kholia/HF-PA-v10/R4-Minimal-K1TE/README.md

Minor tweaks - previous versions are 100% fine ;)

List of changes:

- Base resistor changed to 3.3R

- Use M3 holes ;)

- Longer pads for the SMD-coupled-inductor

- Use SMT caps in LPF
