kholia/HF-PA-v10/R7.1/README.md

Minor tweaks - previous versions are 100% fine ;)

List of changes:

- Various silkscreen improvements
