kholia/HF-PA-v10/GSD-Hacks-v2-SMD/README.md

This version uses SOP-8 gate driver (UCC27614DR) and GSD pinout FET.
