kholia/HF-PA-v10/GSD-Hacks-v3-SMD/README.md

This version uses SOIC-8 gate driver (NCP81074ADR2G) and GSD pinout FET.
