kholia/HF-PA-v10/IRFP-Hacks-v5-SMD/README.md

This works great - tested in June 2024.

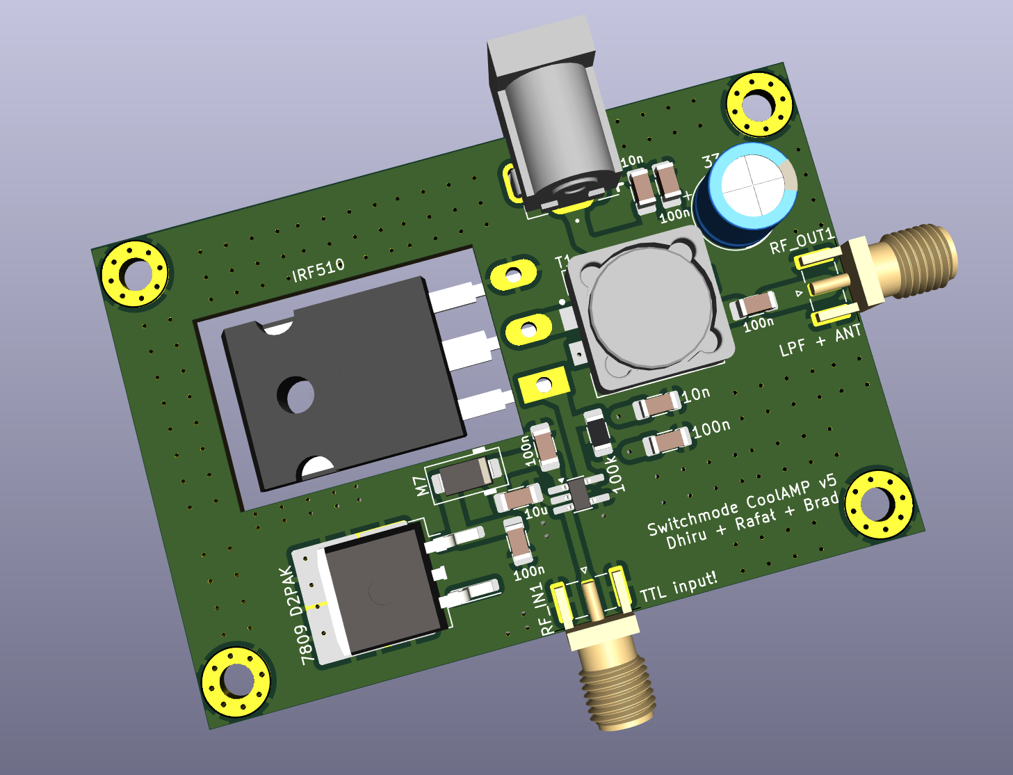
[picture p13: IRFP-Hacks-v5-SMD/Screenshot_2024-08-01_07-13-50.png]
3D render
