kholia/HF-PA-v10/3-Pole-LPF/Screenshot_2024-05-31_14-55-14.png

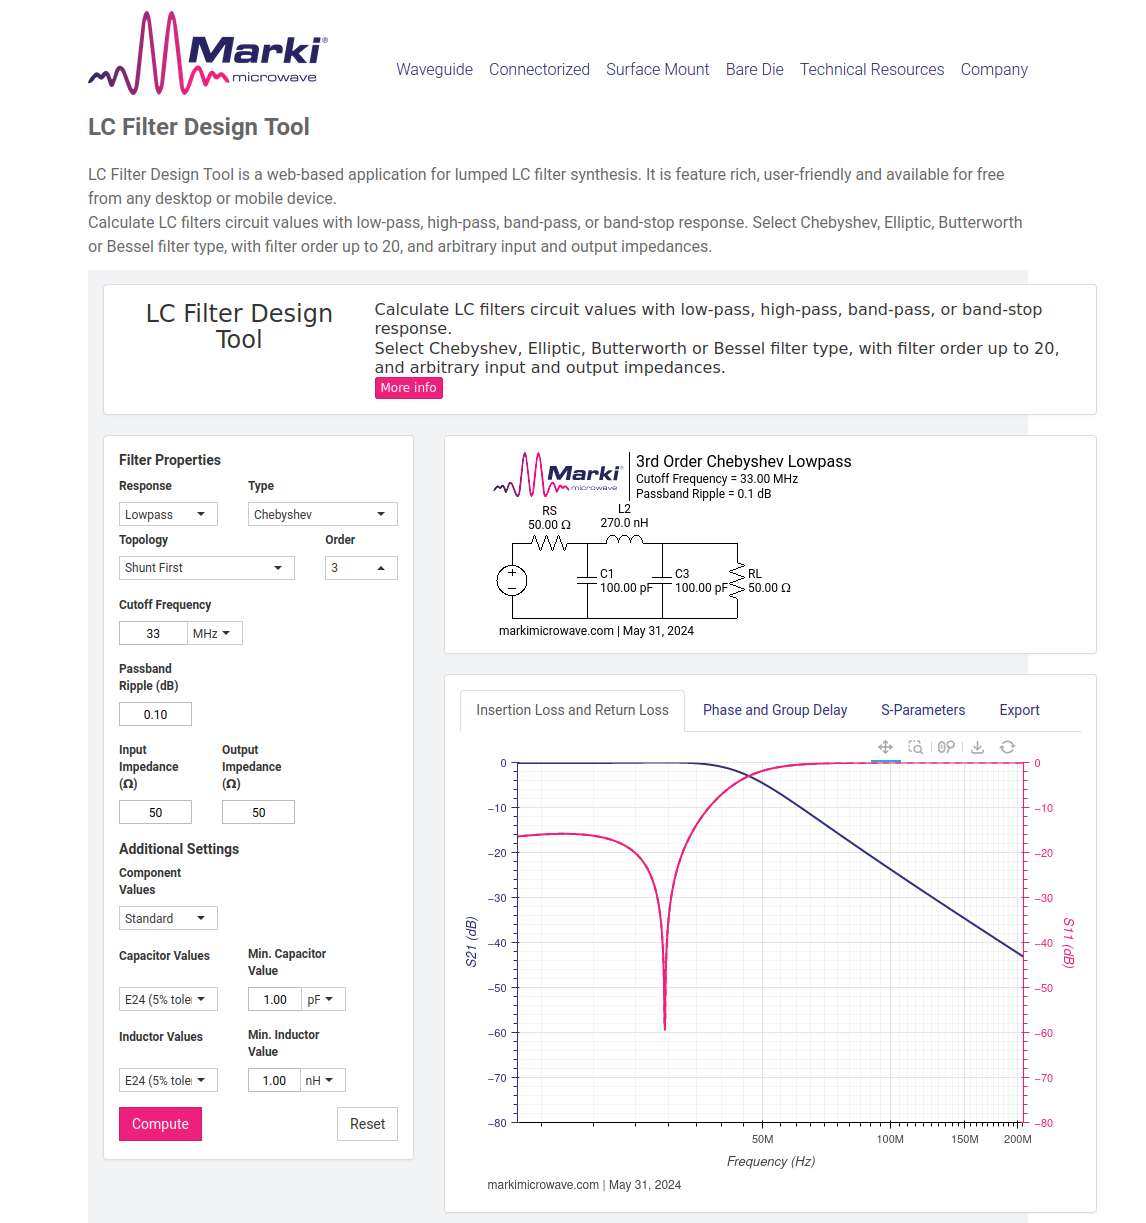
3-Pole-LPF/Screenshot_2024-05-31_14-55-14.png
