kholia/HF-PA-v10/5-Pole-LPF/Screenshot_2024-06-10_09-03-32.png

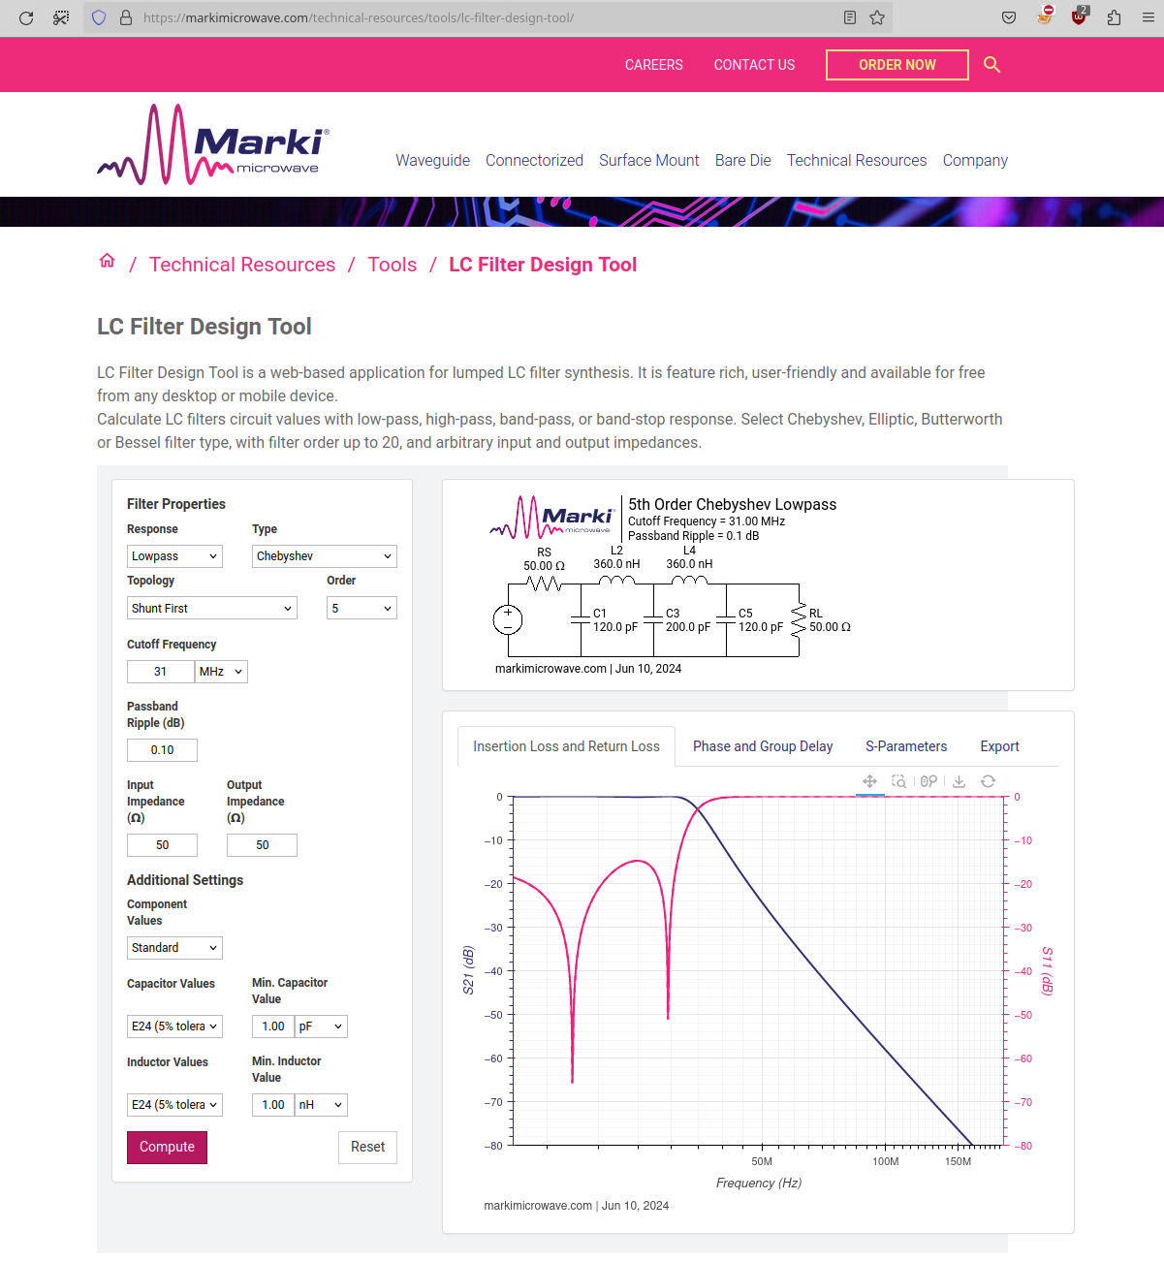
5-Pole-LPF/Screenshot_2024-06-10_09-03-32.png
