kholia/HF-PA-v10/Digital-PA-v3/Screenshot_2023-10-04_21-27-38.png

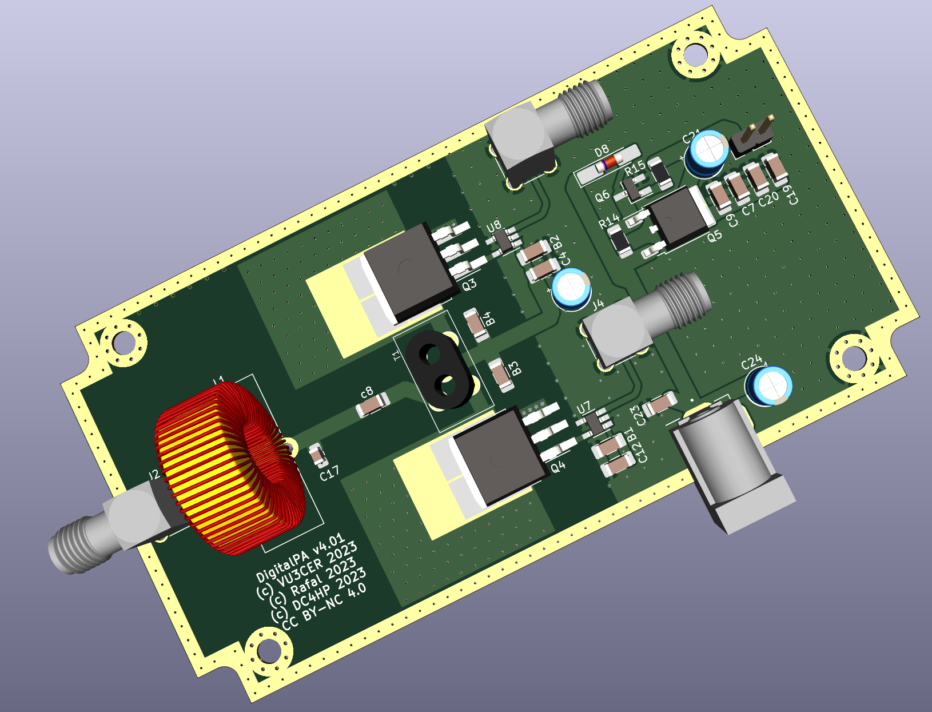
Digital-PA-v3/Screenshot_2023-10-04_21-27-38.png
