kholia/HF-PA-v10/FuturePowerControl/Alinco DX-10 - Retro Feel.png

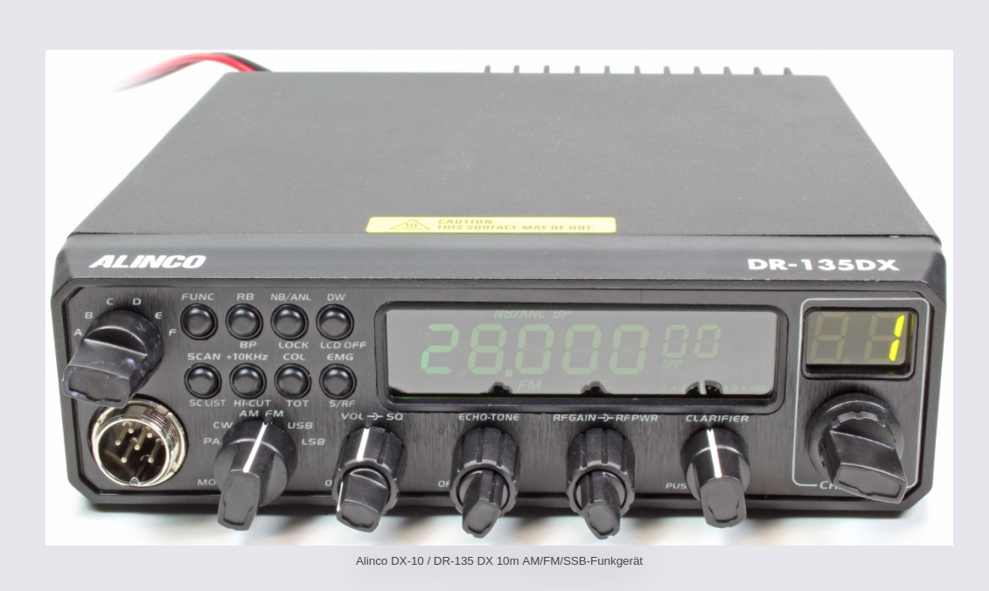
FuturePowerControl/Alinco DX-10 - Retro Feel.png
