kholia/HF-PA-v10/Heat-Sinking/heatsinkmtg.gif

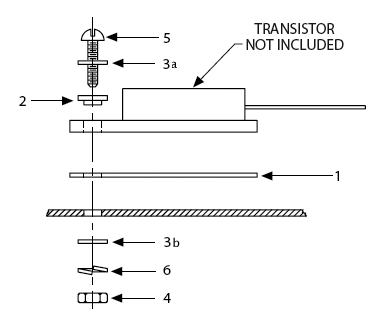
Heat-Sinking/heatsinkmtg.gif
