kholia/HF-PA-v10/Heat-Sinking/heatsinkmtgparts.gif

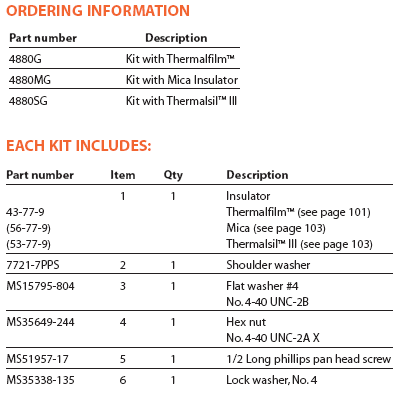
Heat-Sinking/heatsinkmtgparts.gif
