kholia/HF-PA-v10/info/25wlinear-small.png

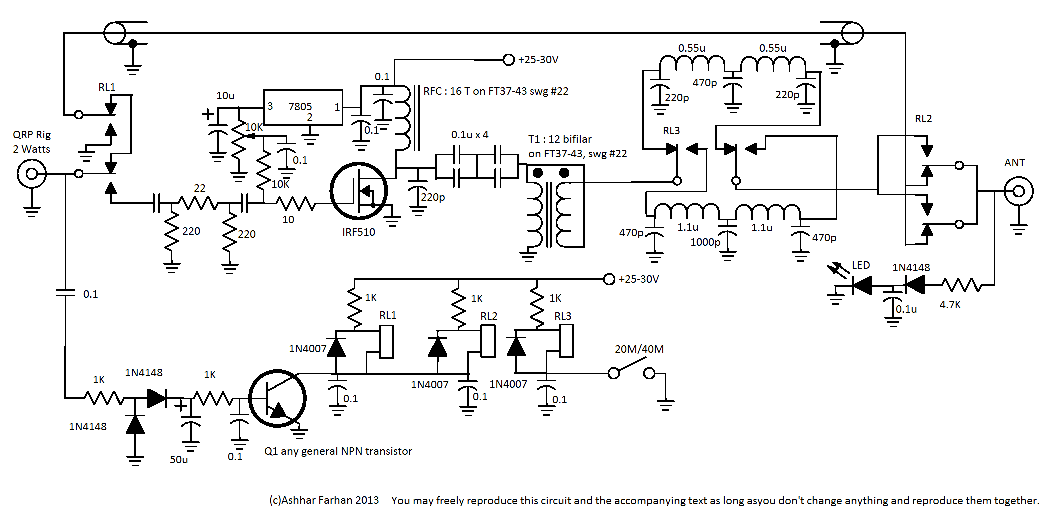
info/25wlinear-small.png
