kholia/HF-PA-v10/info/Henning Paul's PA prototype.jpeg

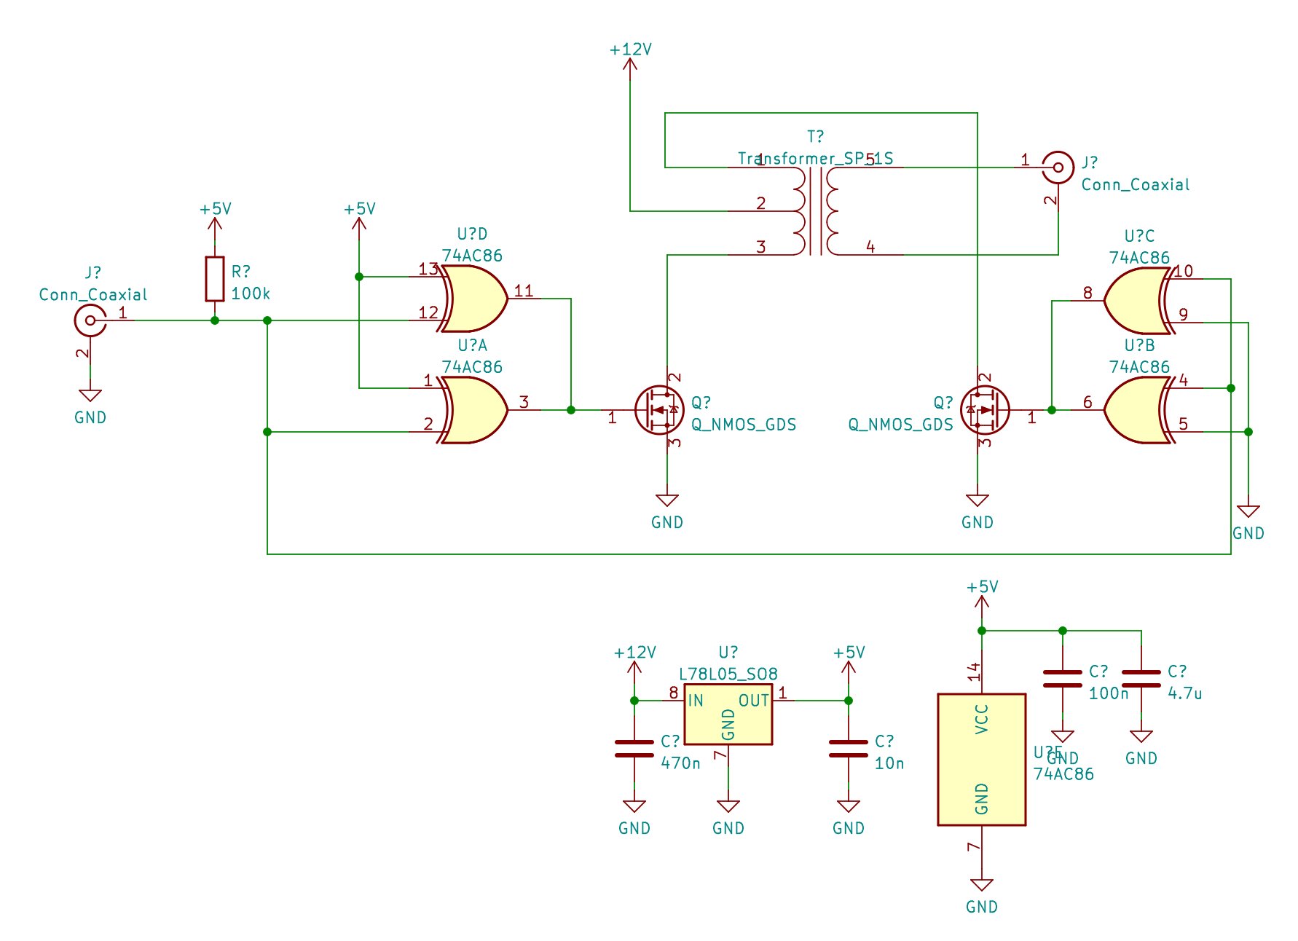
info/Henning Paul's PA prototype.jpeg
