kholia/HF-PA-v10/info/Henning Paul's PA v2.0.jpeg

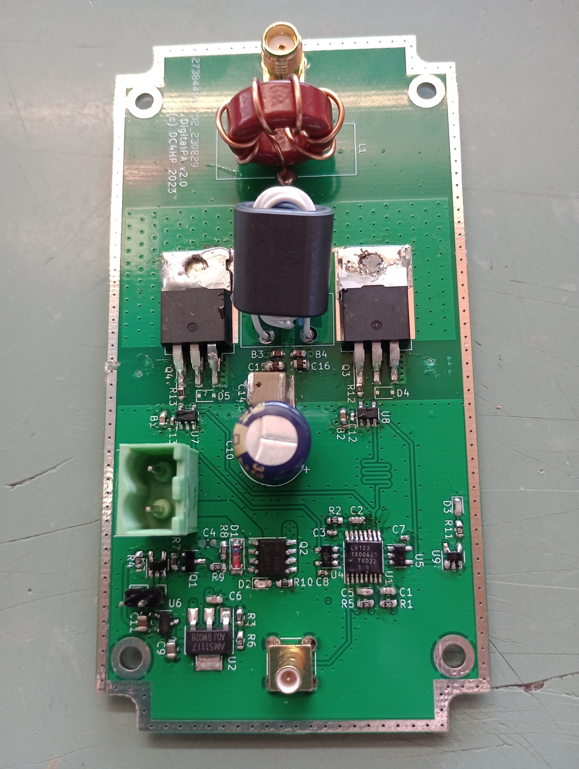
info/Henning Paul's PA v2.0.jpeg
