kholia/HF-PA-v10/info/Screenshot_2023-08-16_22-52-23.png

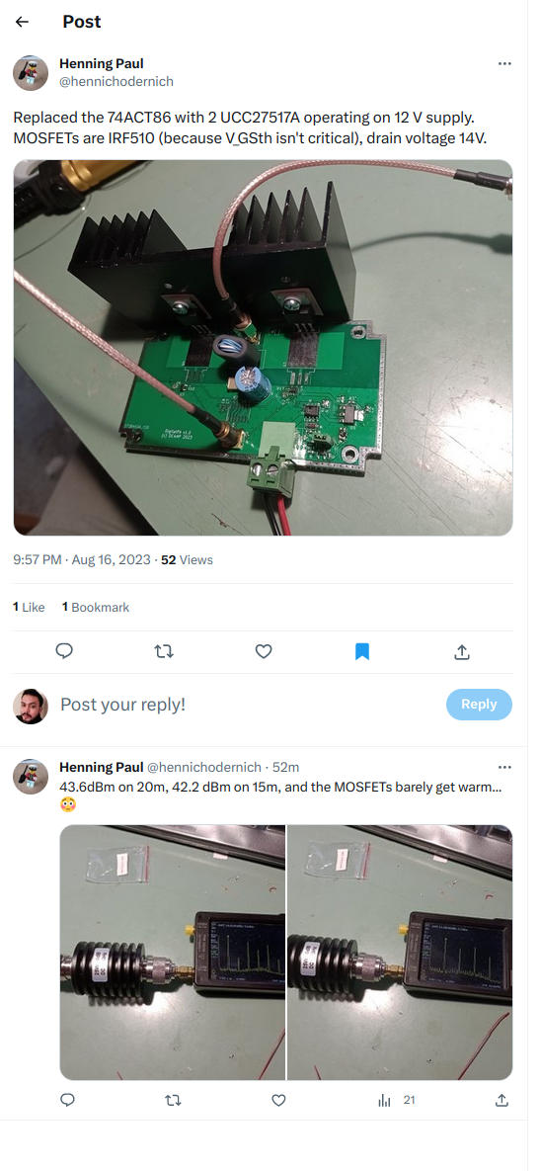
info/Screenshot_2023-08-16_22-52-23.png
