kholia/HF-PA-v10/info/Screenshot_2023-08-20_21-04-47.png

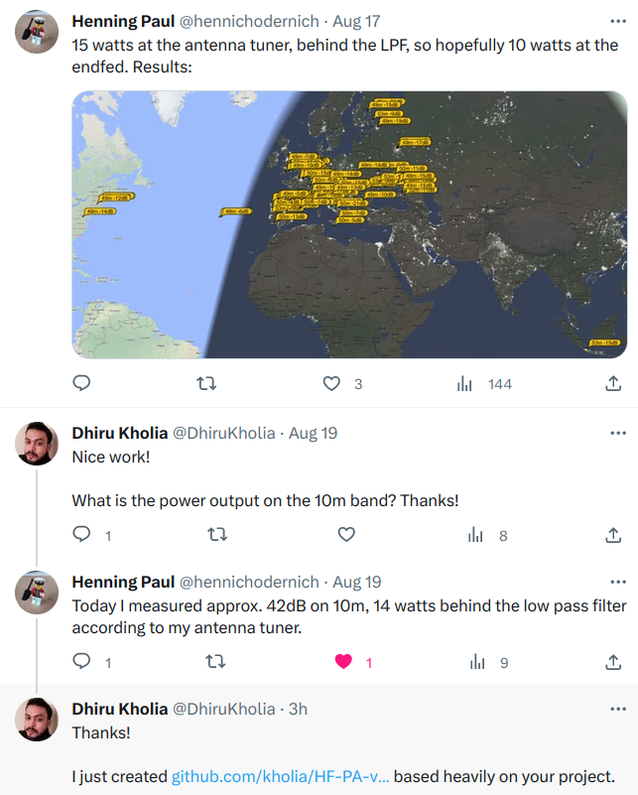
info/Screenshot_2023-08-20_21-04-47.png
