kholia/HF-PA-v10/info/Screenshot_2023-08-23_13-06-54.png

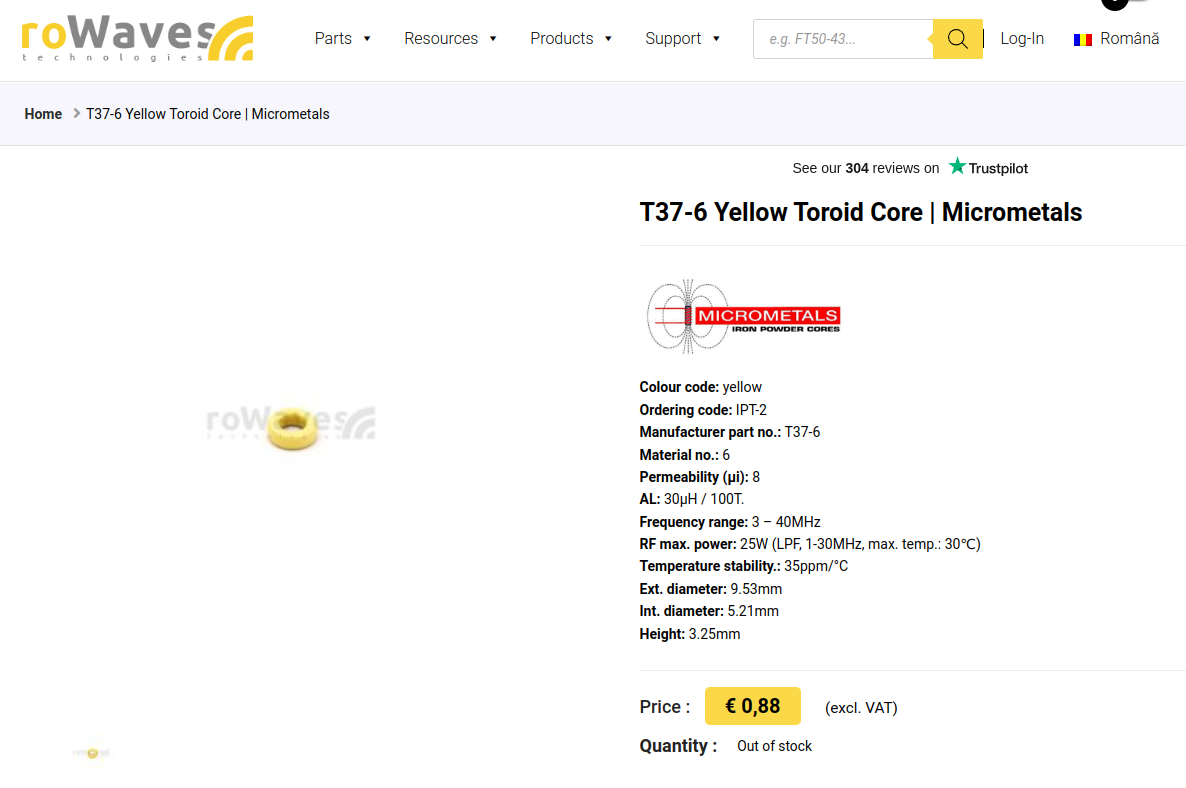
info/Screenshot_2023-08-23_13-06-54.png
