kholia/HF-PA-v10/info/Screenshot_2023-08-23_13-07-39.png

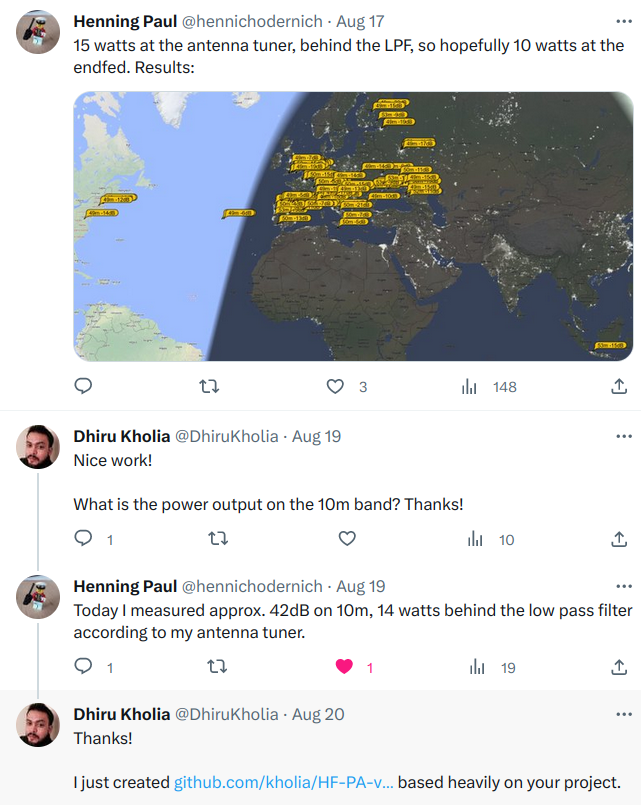
info/Screenshot_2023-08-23_13-07-39.png
