kholia/HF-PA-v10/IRFP-Hacks-v7-SMD-With-SSB/sims/Screenshot_2024-07-24_20-49-58.png

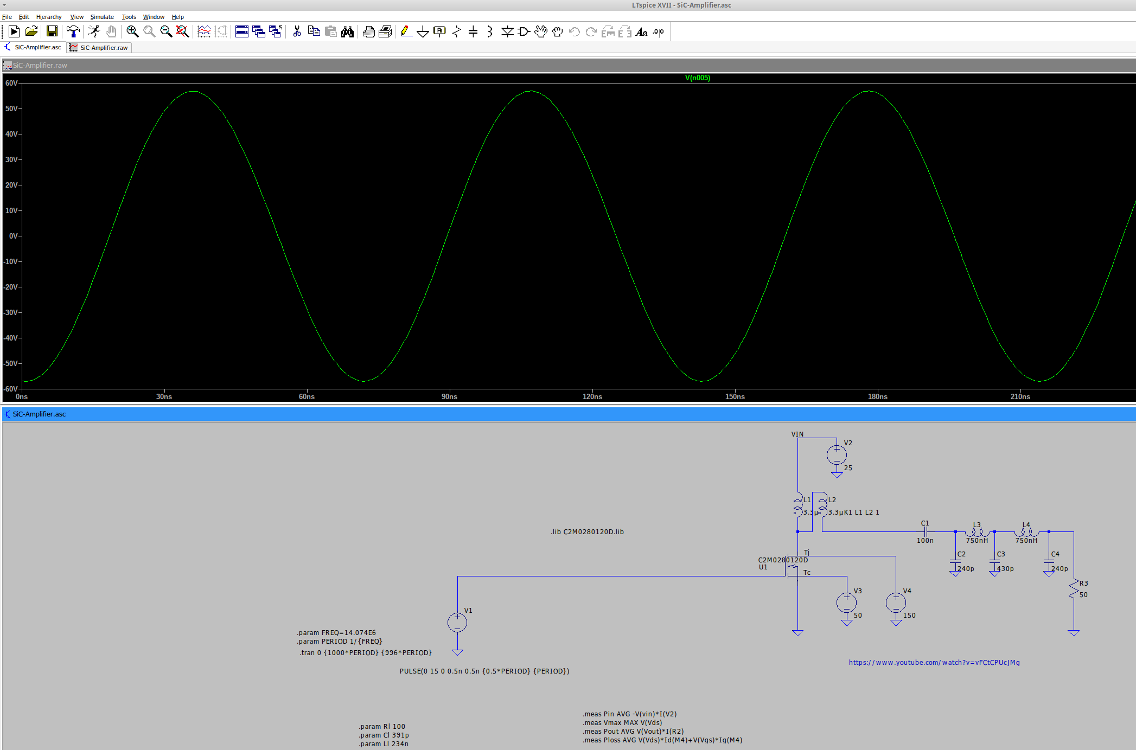
IRFP-Hacks-v7-SMD-With-SSB/sims/Screenshot_2024-07-24_20-49-58.png
