kholia/HF-PA-v10/IRFP-Hacks-v7-SMD-With-SSB/sims/Screenshot_2024-07-25_10-13-01.png

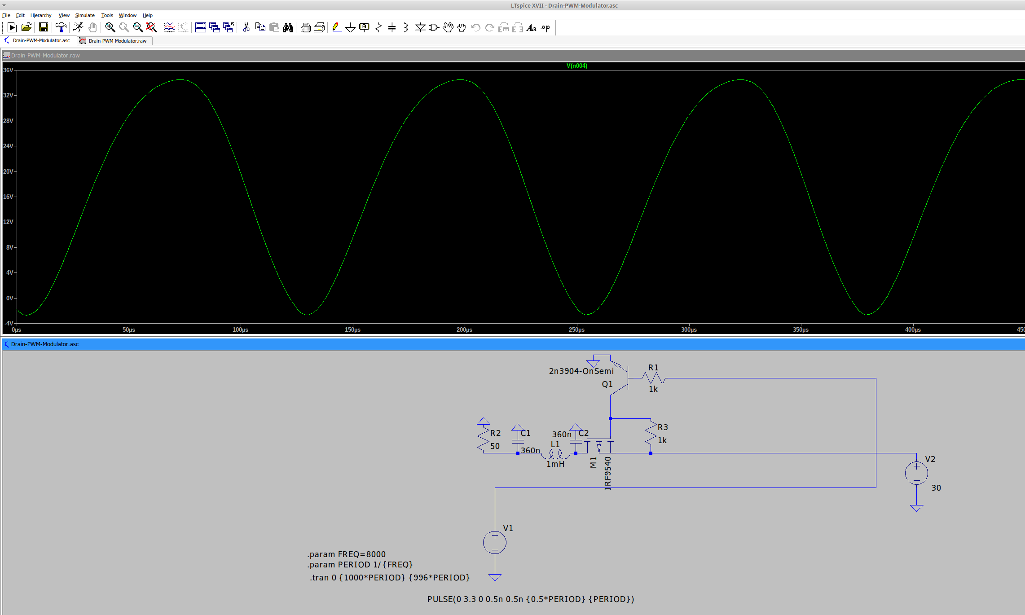
IRFP-Hacks-v7-SMD-With-SSB/sims/Screenshot_2024-07-25_10-13-01.png
