kholia/HF-PA-v10/R5/Screenshot_2023-10-03_14-03-06.png

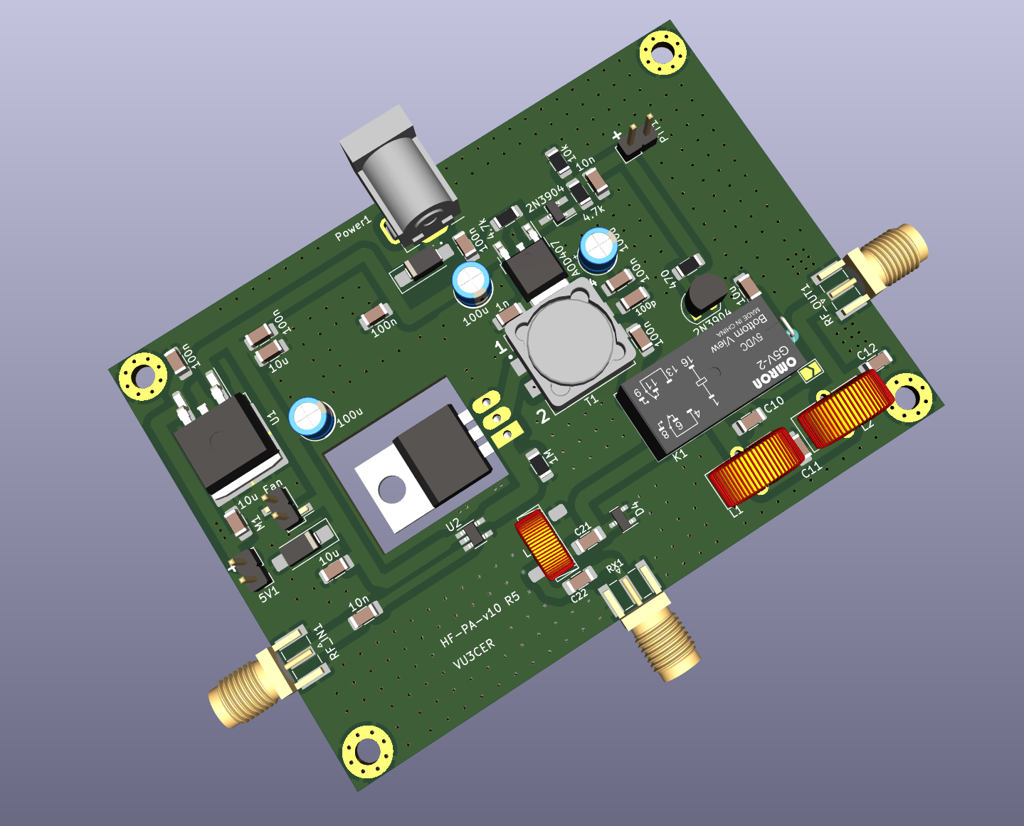
R5/Screenshot_2023-10-03_14-03-06.png
