kholia/HF-PA-v10/R7.1/Screenshot_2023-11-03_10-56-42.png

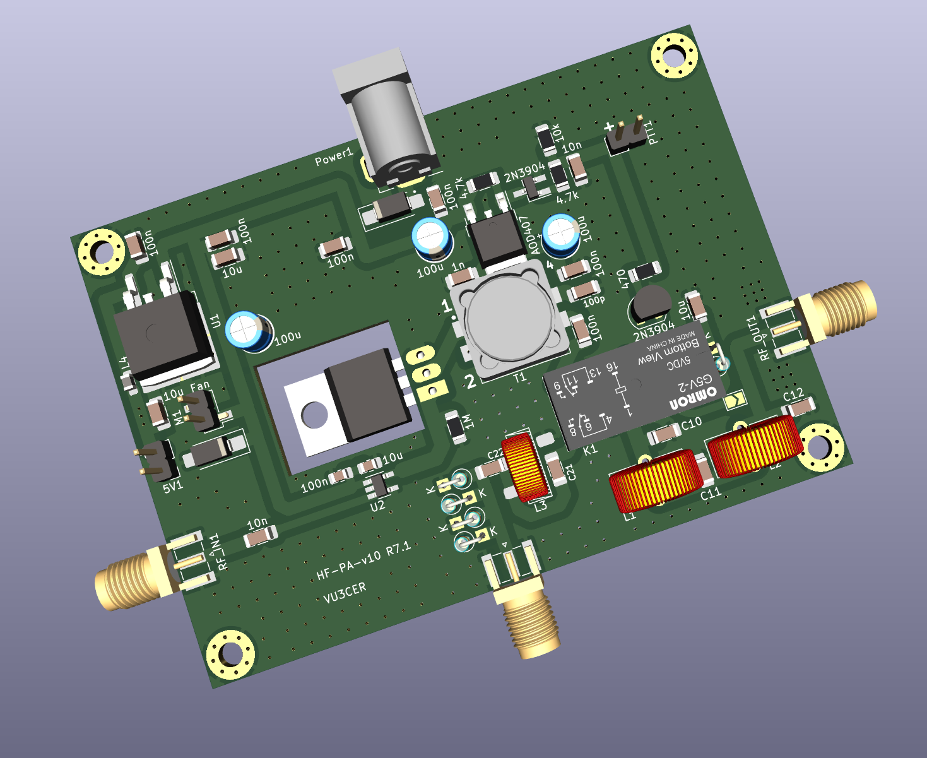
R7.1/Screenshot_2023-11-03_10-56-42.png
