kholia/HF-PA-v10/SiC-QRO-Amp-v2/7448510091.jpg

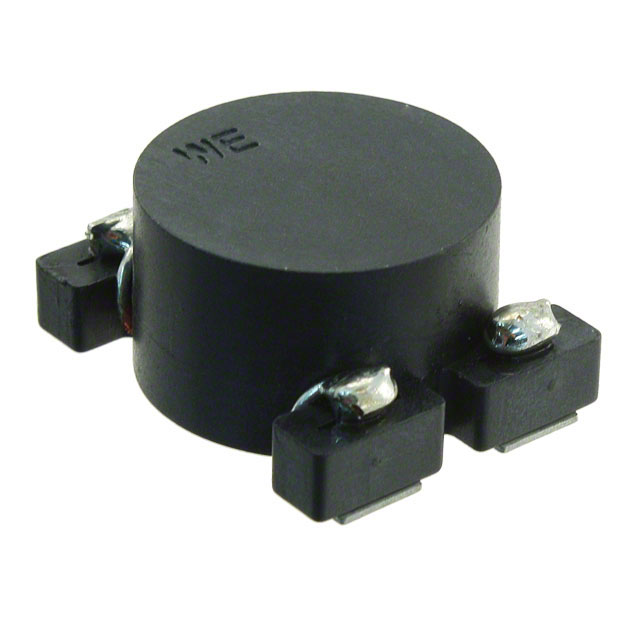
SiC-QRO-Amp-v2/7448510091.jpg
