kholia/HF-PA-v10/Simplified-for-PPT/Screenshot_2023-11-16_07-39-06.png

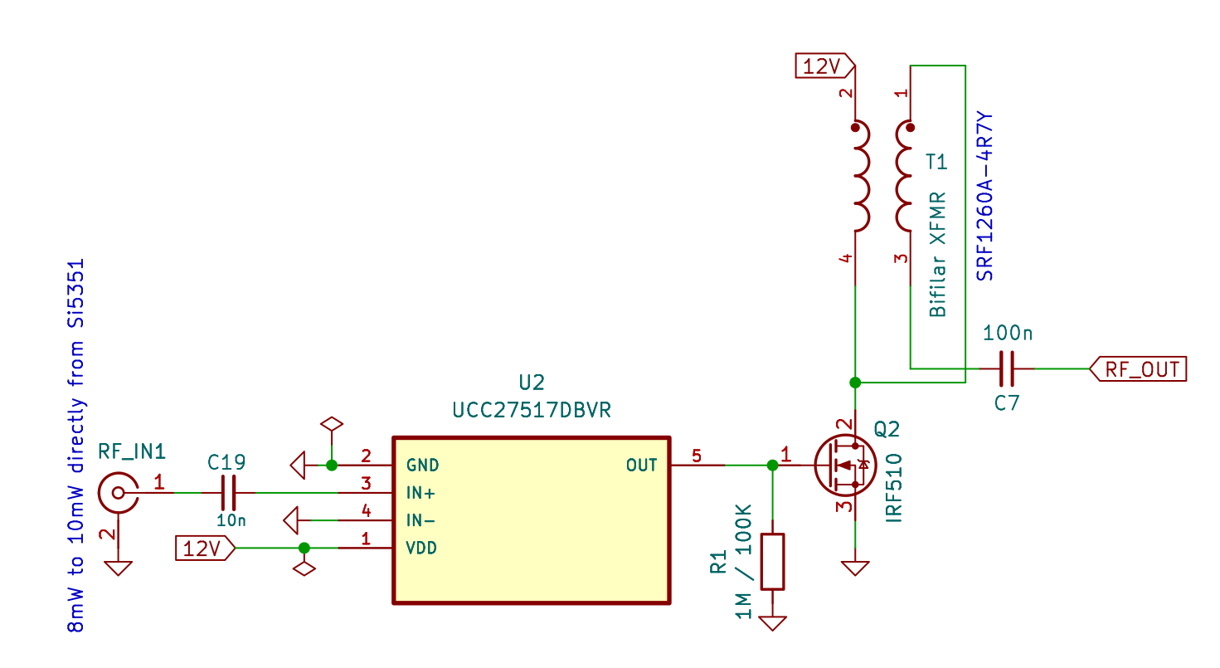
Simplified-for-PPT/Screenshot_2023-11-16_07-39-06.png
