kholia/HF-PA-v10/GSD-Hacks-v8/models/TO-220-3 Bend Mirror.stp

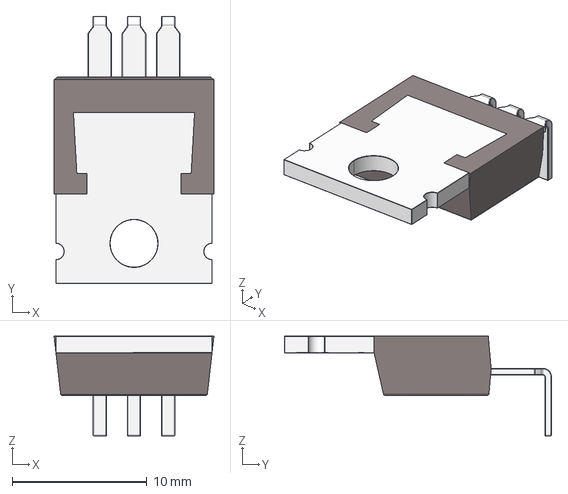
[picture p60: CAD file, 2024-09-08]
GSD-Hacks-v8/models/TO-220-3 Bend Mirror.stp
11.9 x 19.8 x 7.41 mm
