kholia/HF-PA-v10/results/Screenshot_2023-09-14_14-50-23.png

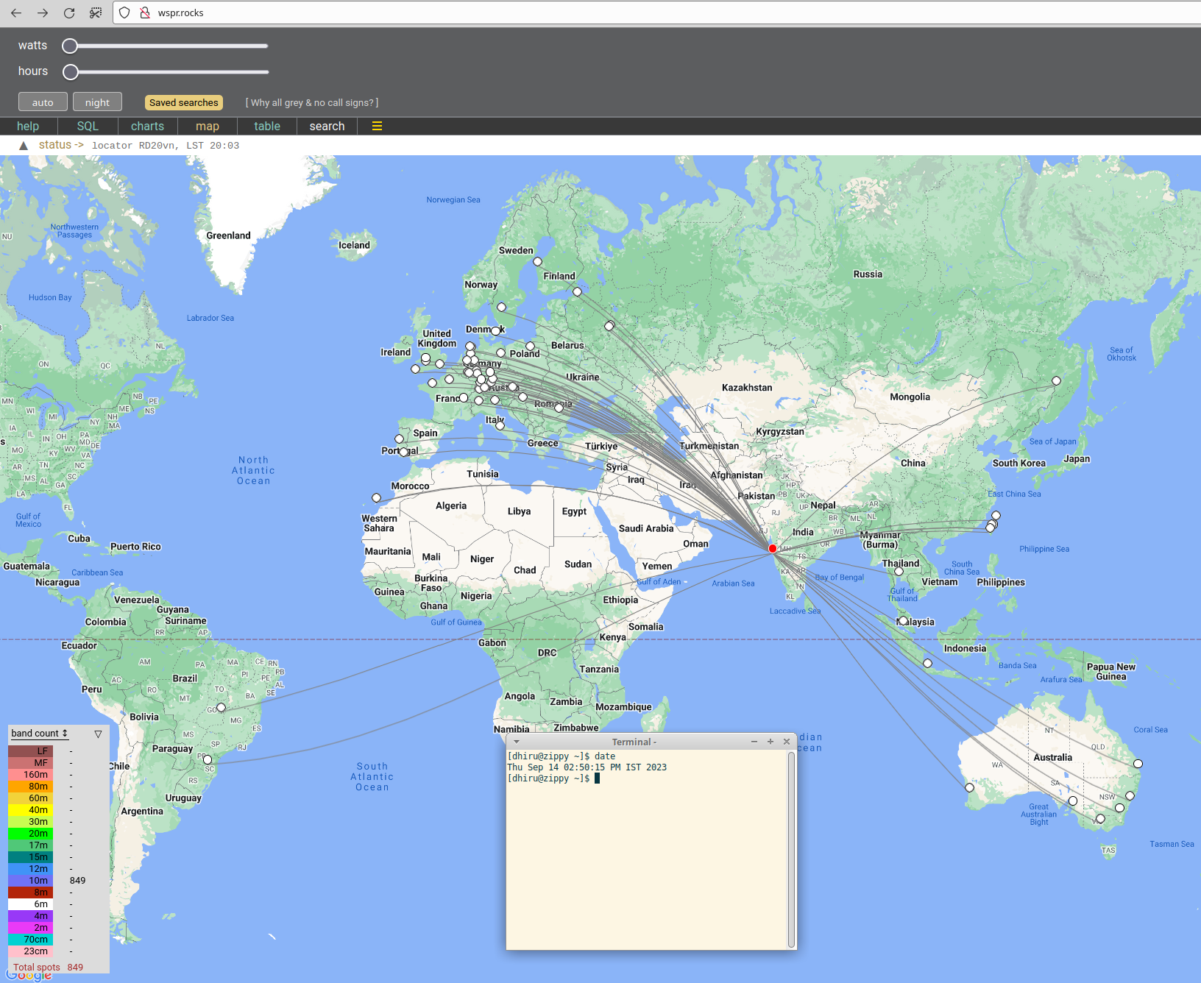
results/Screenshot_2023-09-14_14-50-23.png
