kholia/HF-PA-v10/results/Screenshot_2023-09-15_01-19-01.png

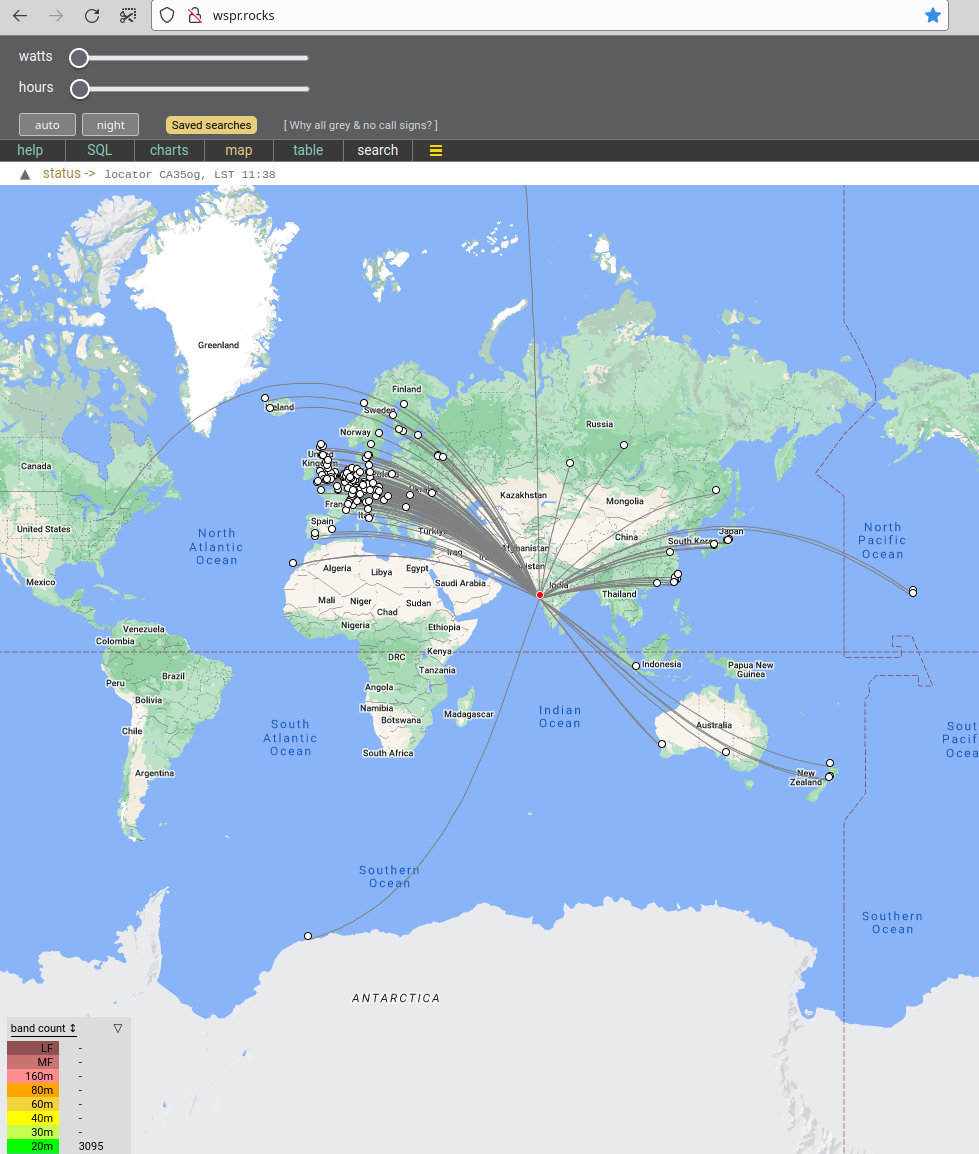
results/Screenshot_2023-09-15_01-19-01.png
