kholia/HF-PA-v10/results/Screenshot_2023-09-15_21-23-19.png

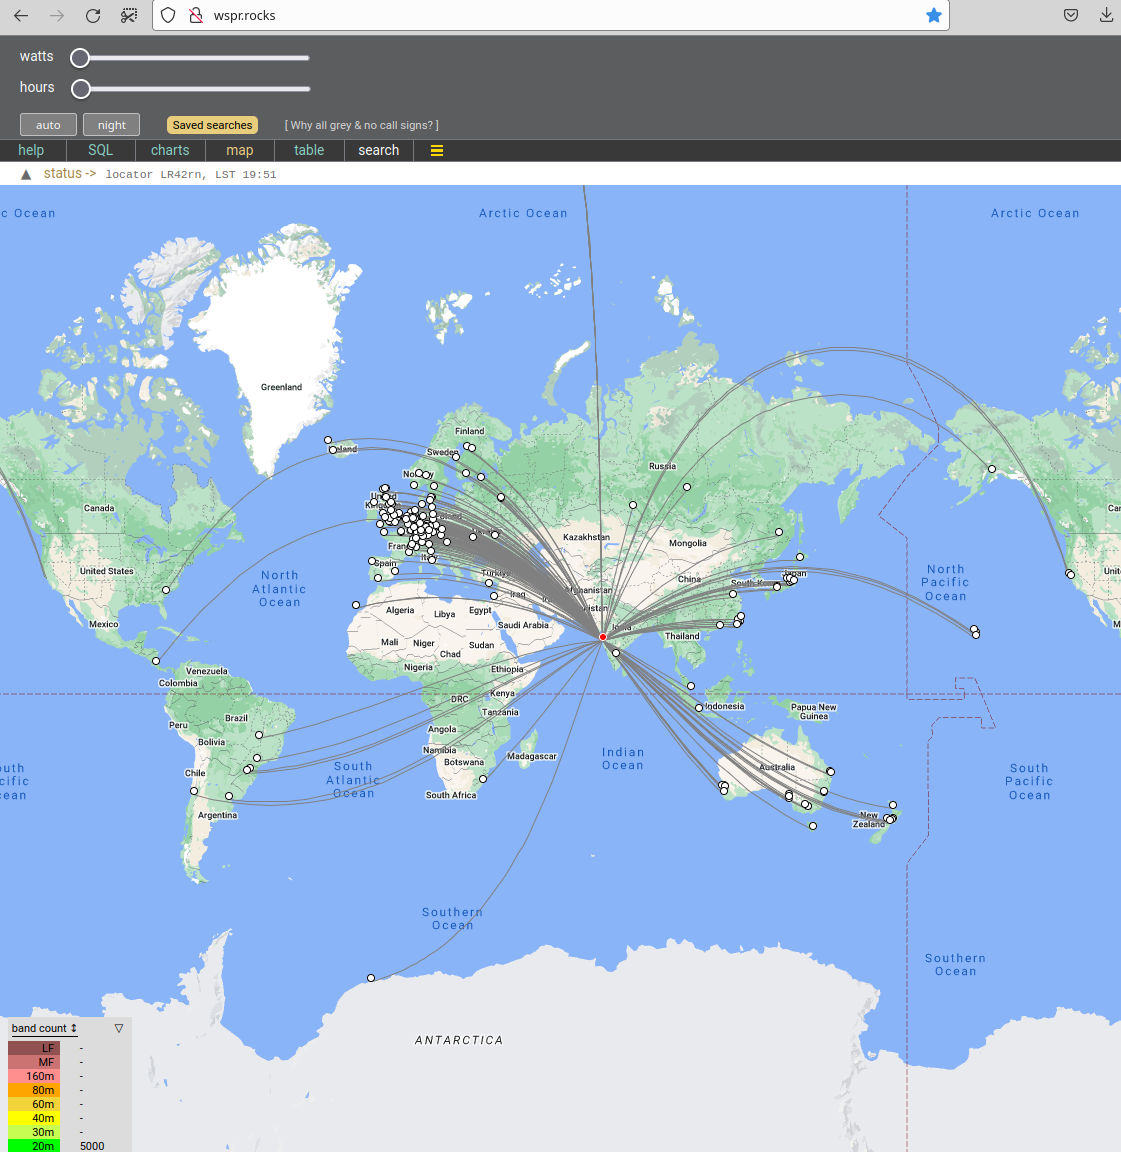
results/Screenshot_2023-09-15_21-23-19.png
