kholia/HF-PA-v10/results/Screenshot_2023-11-05_17-35-47.png

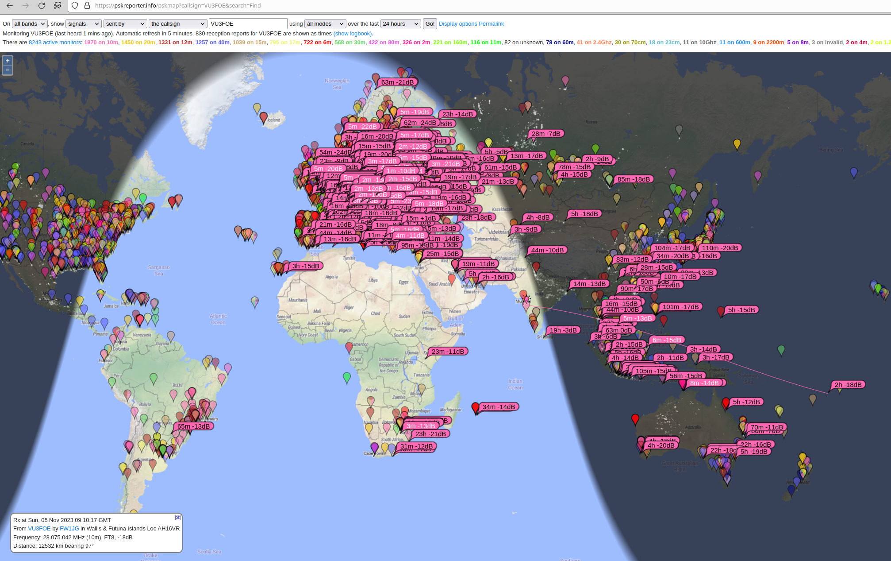
results/Screenshot_2023-11-05_17-35-47.png
