kholia/HF-PA-v10/R7.1/HF-PA-v10-R7.1.pdf

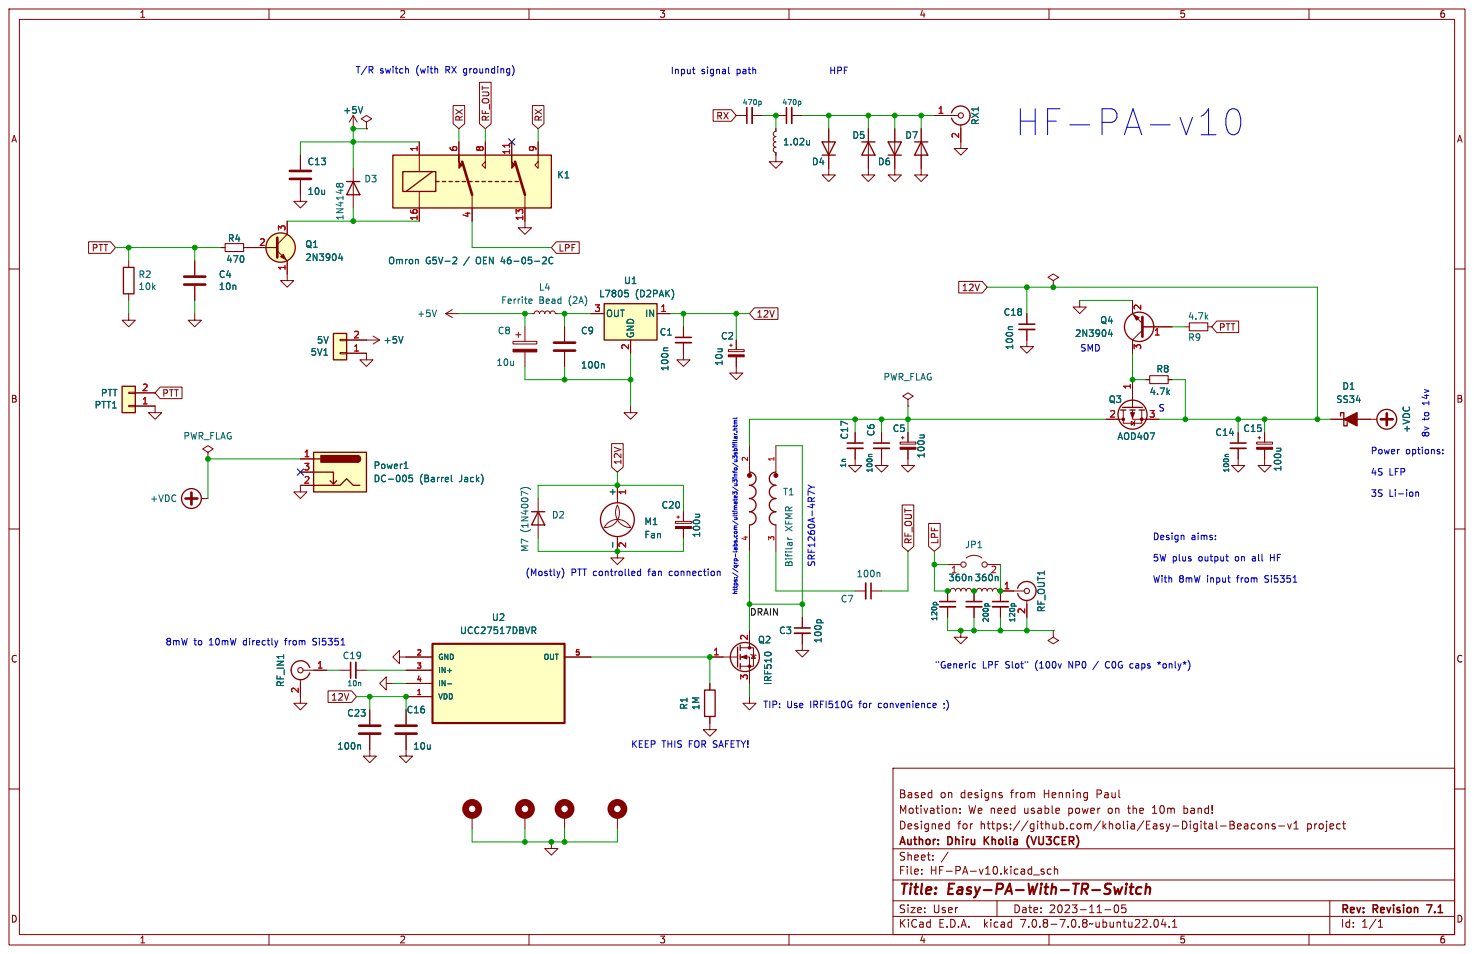
[picture p69: page 1]

"Generic LPF Slot" (100v NP0 / C0G caps *only*) KEEP THIS FOR SAFETY! https://qrp-labs.com/ultimate3/u3info/u3sbifilar.html

Id: 1/1 Title: Easy-PA-With-TR-Switch
