kholia/HF-PA-v10/IRFP-Hacks/HF-PA-v10.pdf

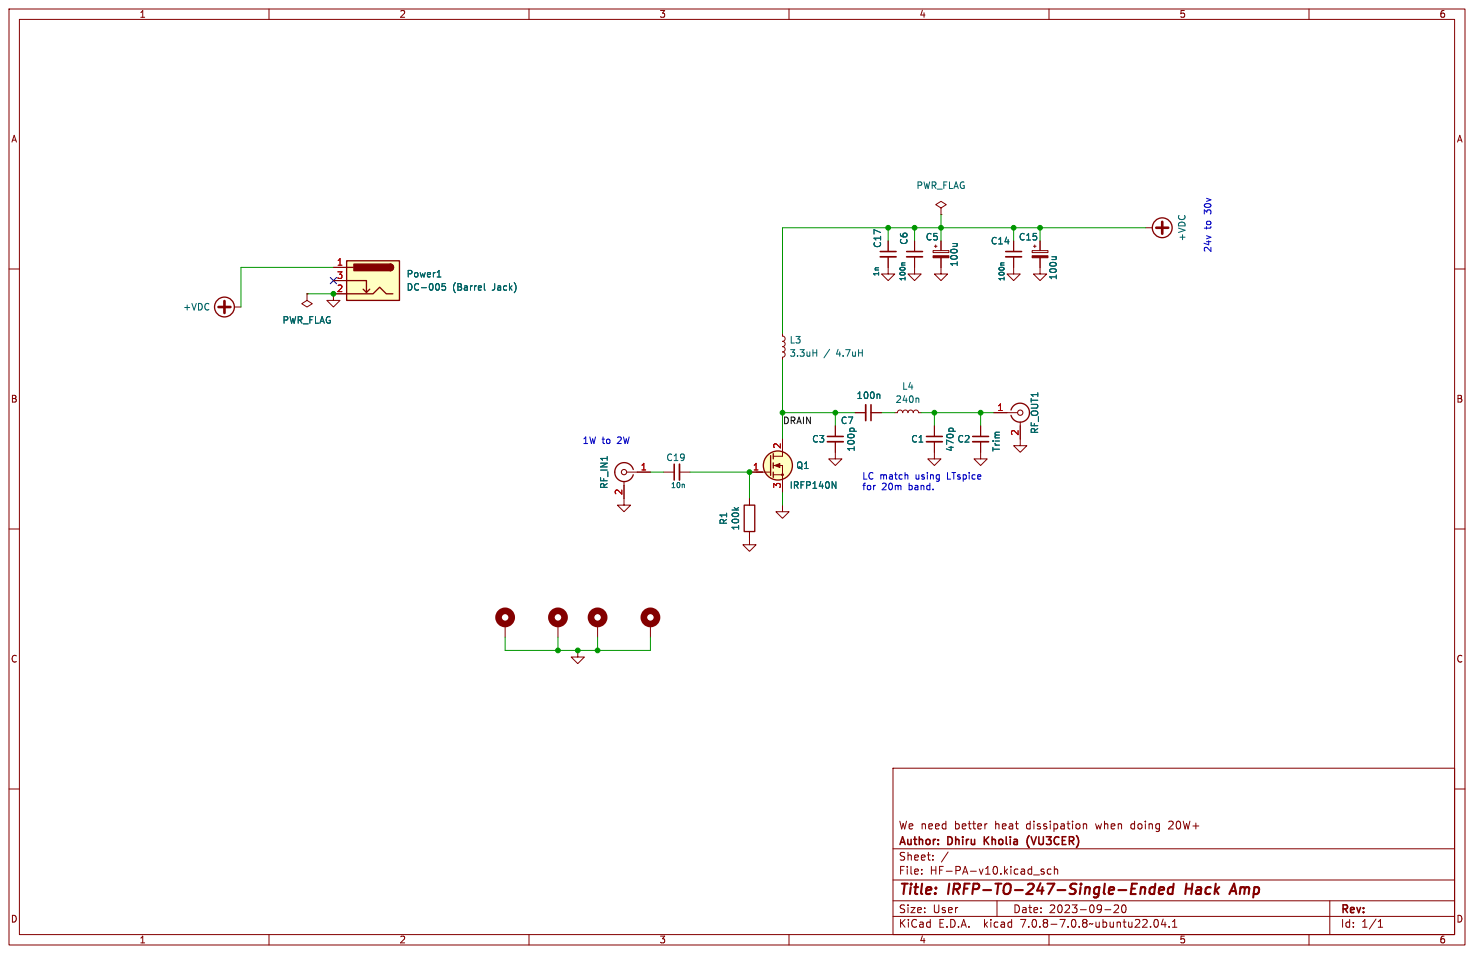
[picture p78: page 1]
