kholia/HF-PA-v10/MRF101-Hack/HF-PA-v10.pdf

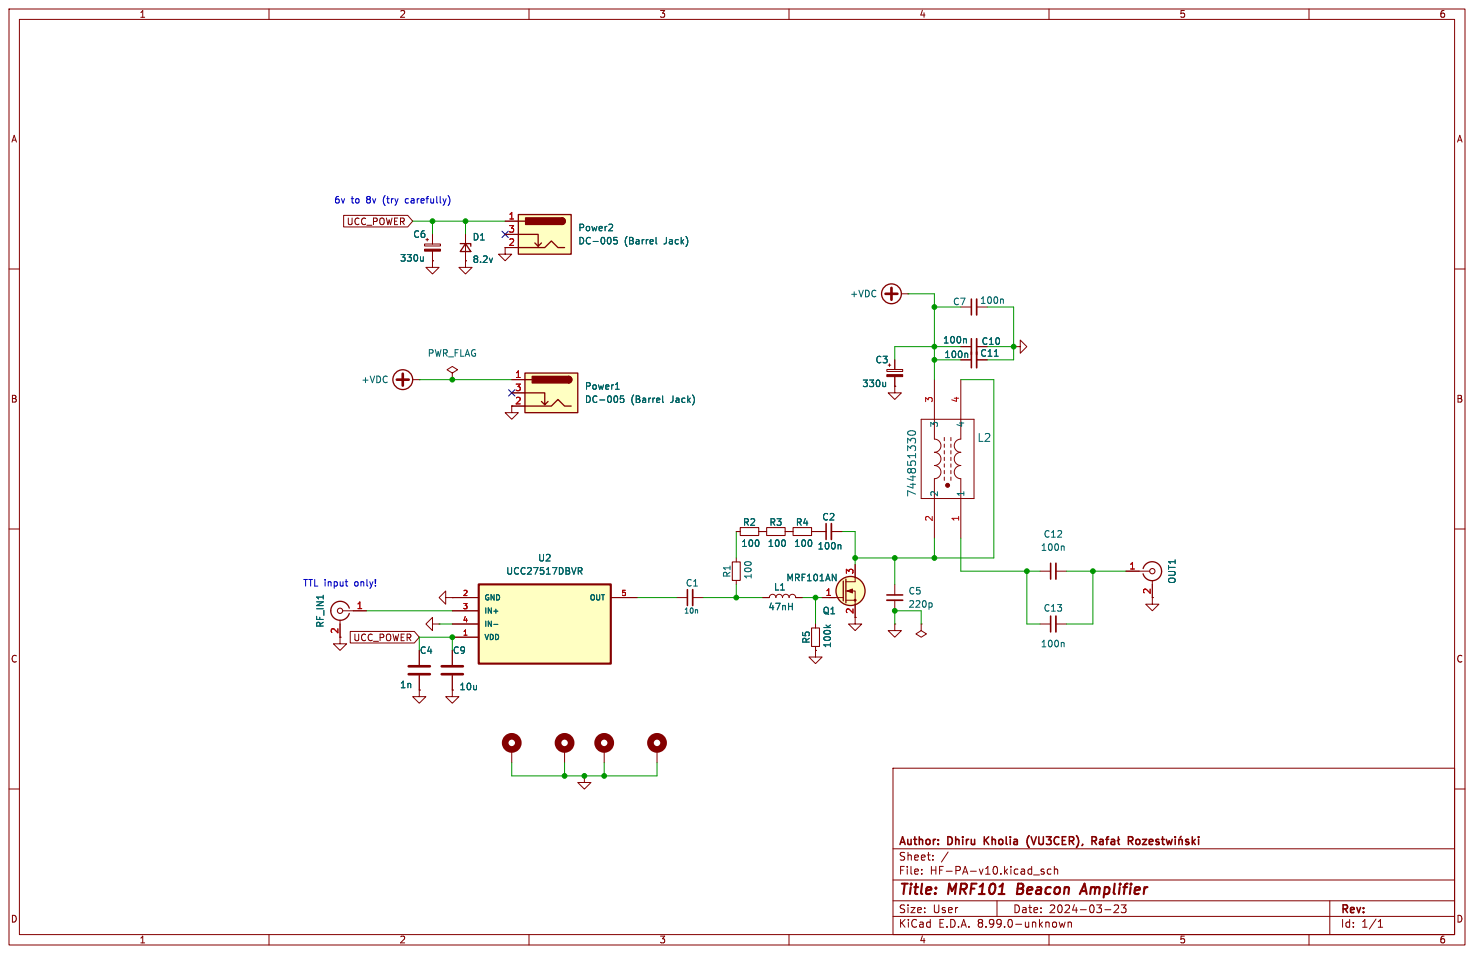
[picture p79: page 1]
