kholia/HF-PA-v10/IRFP-Hacks-v8-SMD/HF-PA-v10.pdf

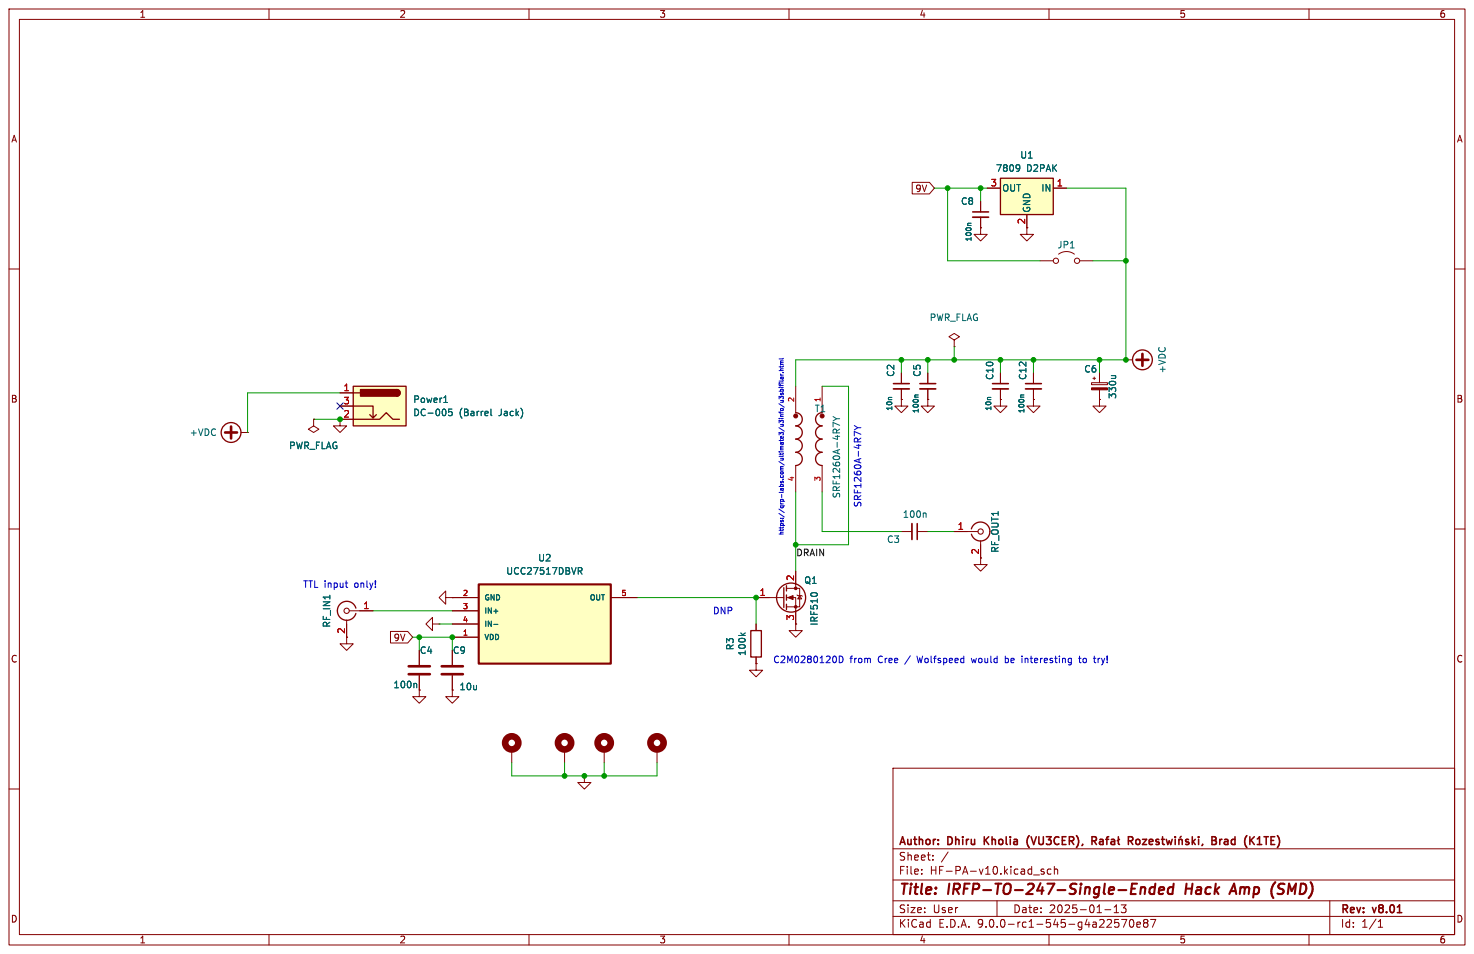
[picture p80: page 1]

2 OUT 3 Power1 DC-005 (Barrel Jack) 1
