kholia/HF-PA-v10/Simplified-for-PPT/HF-PA-v10.pdf

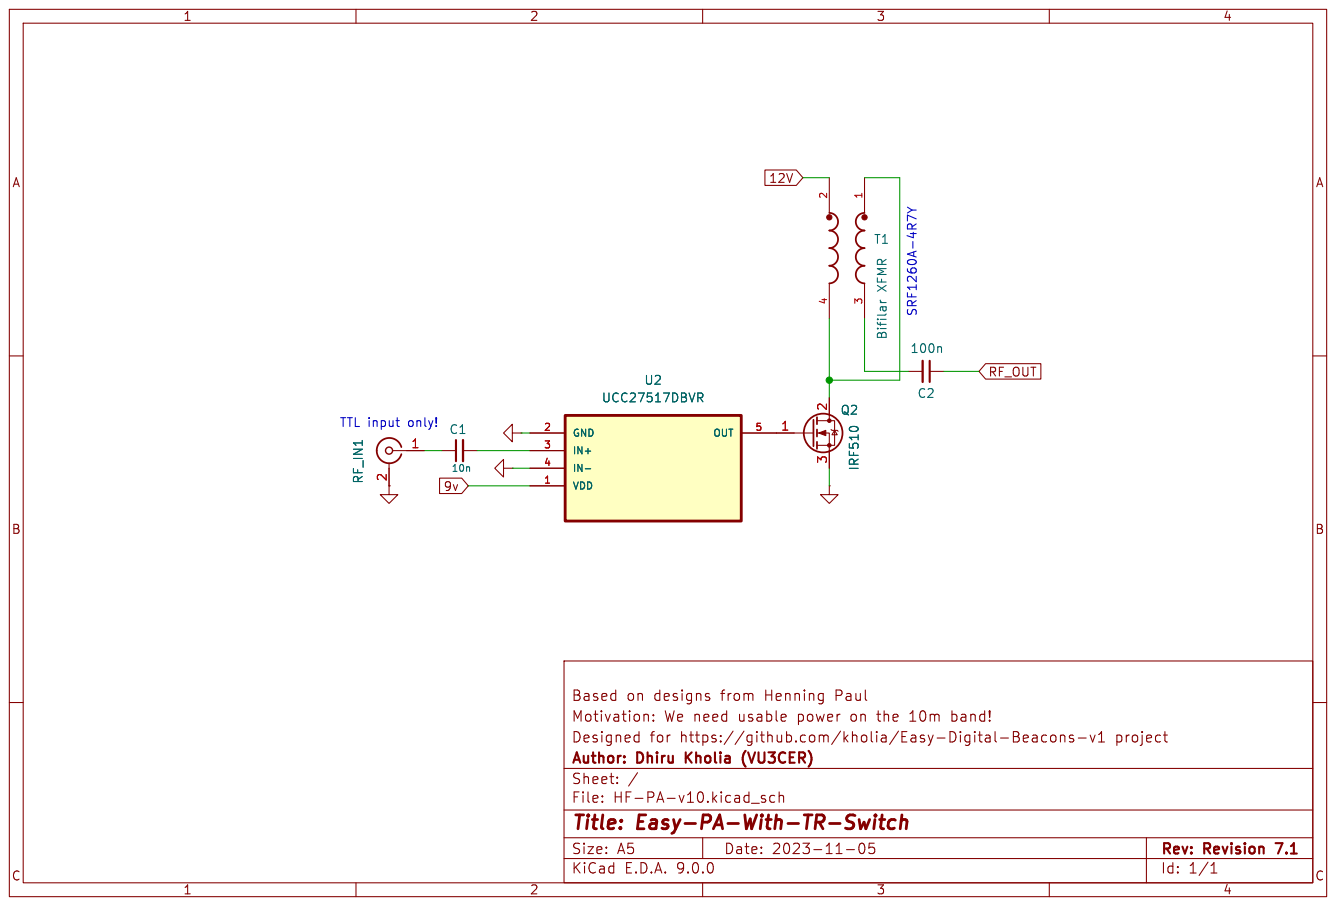
[picture p81: page 1]

Id: 1/1 Title: Easy-PA-With-TR-Switch
