kholia/HF-PA-v10/MRF101-QRO/HF-PA-v10.pdf

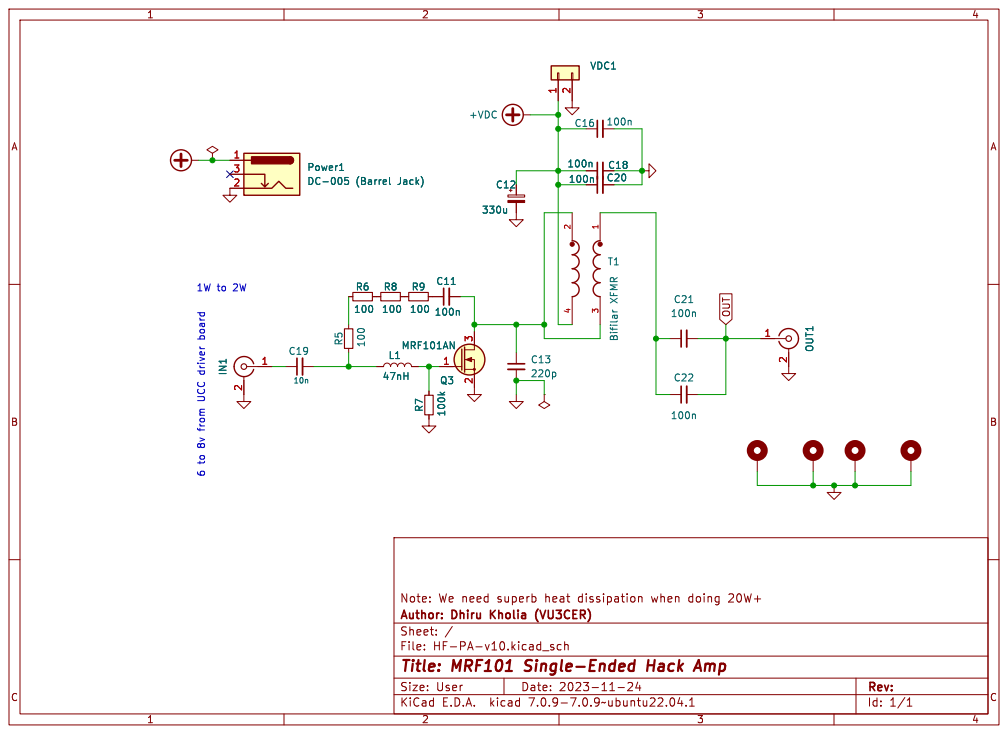
[picture p82: page 1]

6 to 8v from UCC driver board C12
