kholia/HF-PA-v10/R4/HF-PA-v10.pdf

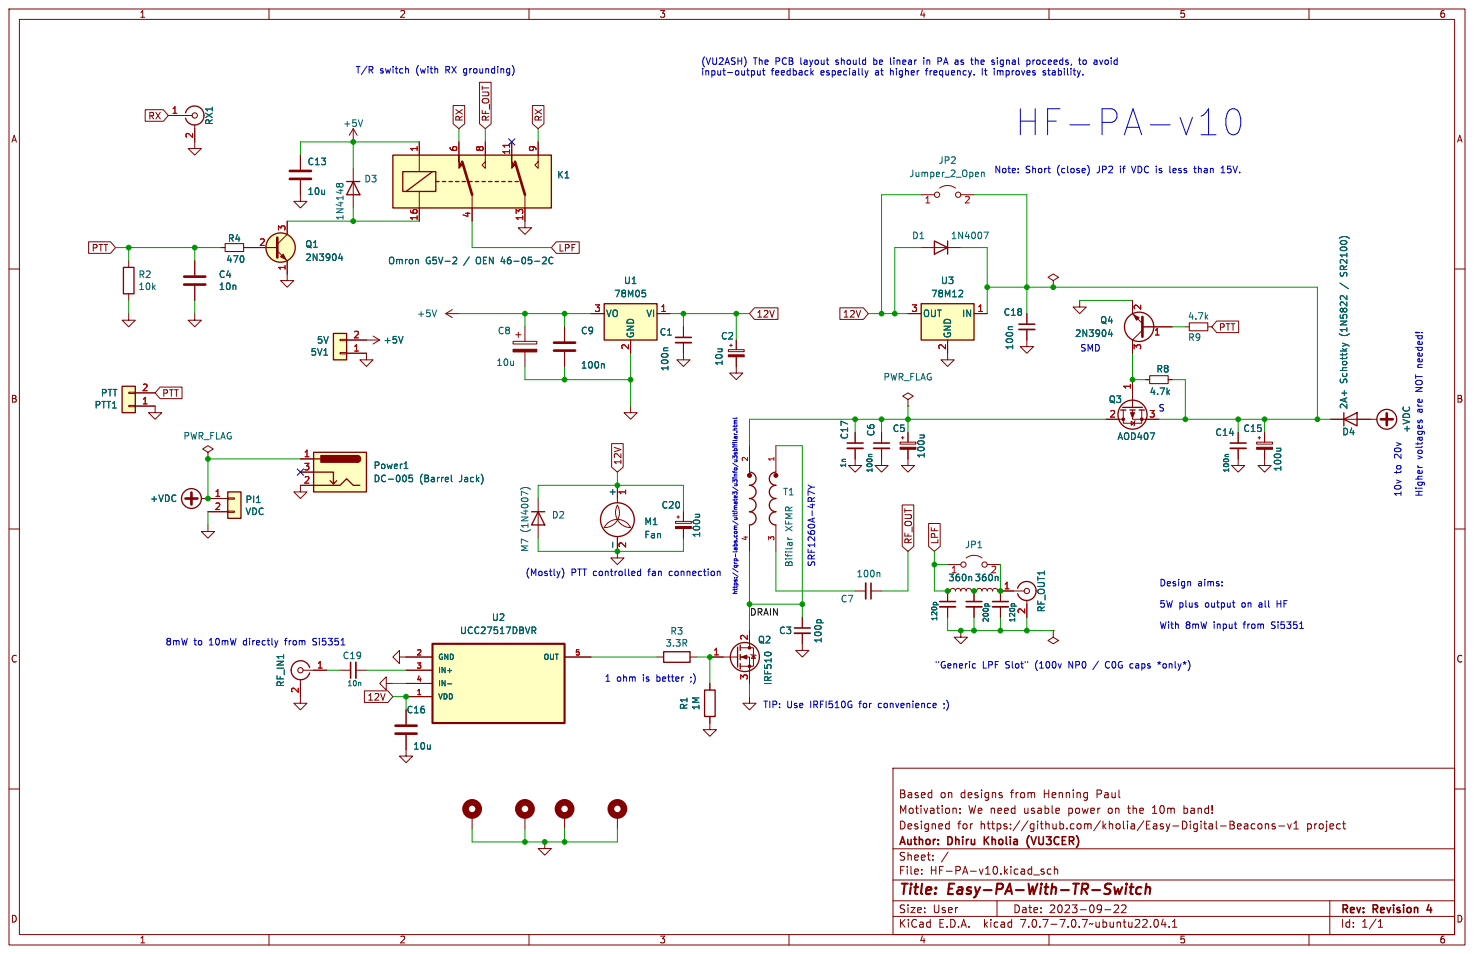
[picture p83: page 1]

T/R switch (with RX grounding)

Design aims: 5W plus output on all HF With 8mW input from Si5351 S

"Generic LPF Slot" (100v NP0 / C0G caps *only*)

Id: 1/1 Title: Easy-PA-With-TR-Switch
