kholia/HF-PA-v10/R5/HF-PA-v10.pdf

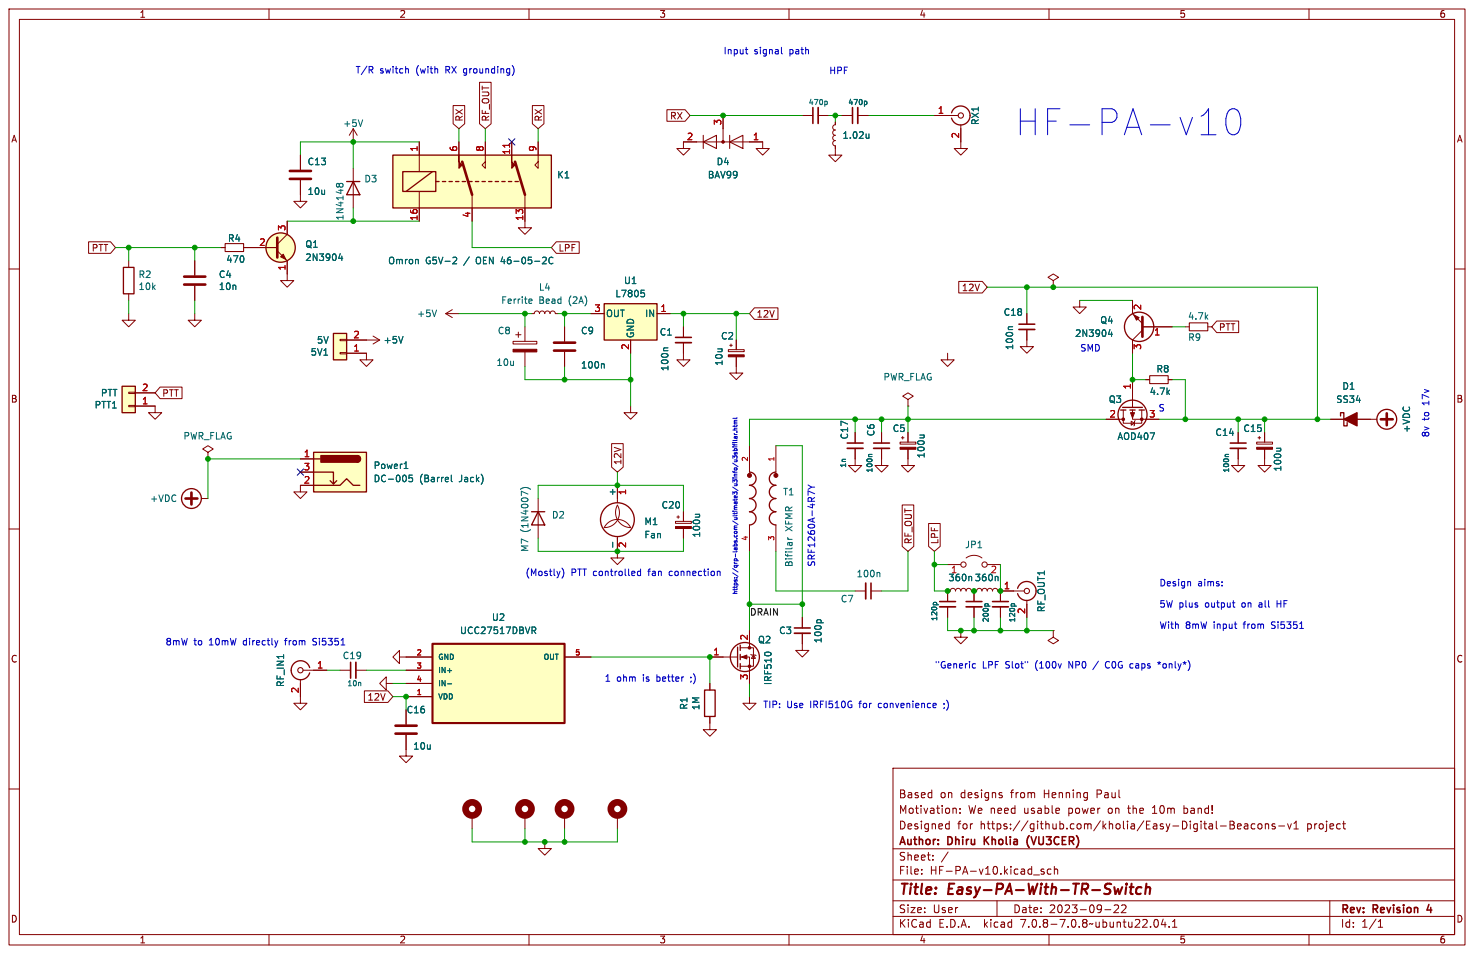
[picture p84: page 1]

2 120p 200p 120p C15 100u Q3AOD407
"Generic LPF Slot" (100v NP0 / C0G caps *only*) S

Id: 1/1 Title: Easy-PA-With-TR-Switch
