kholia/HF-PA-v10/R7/HF-PA-v10.pdf

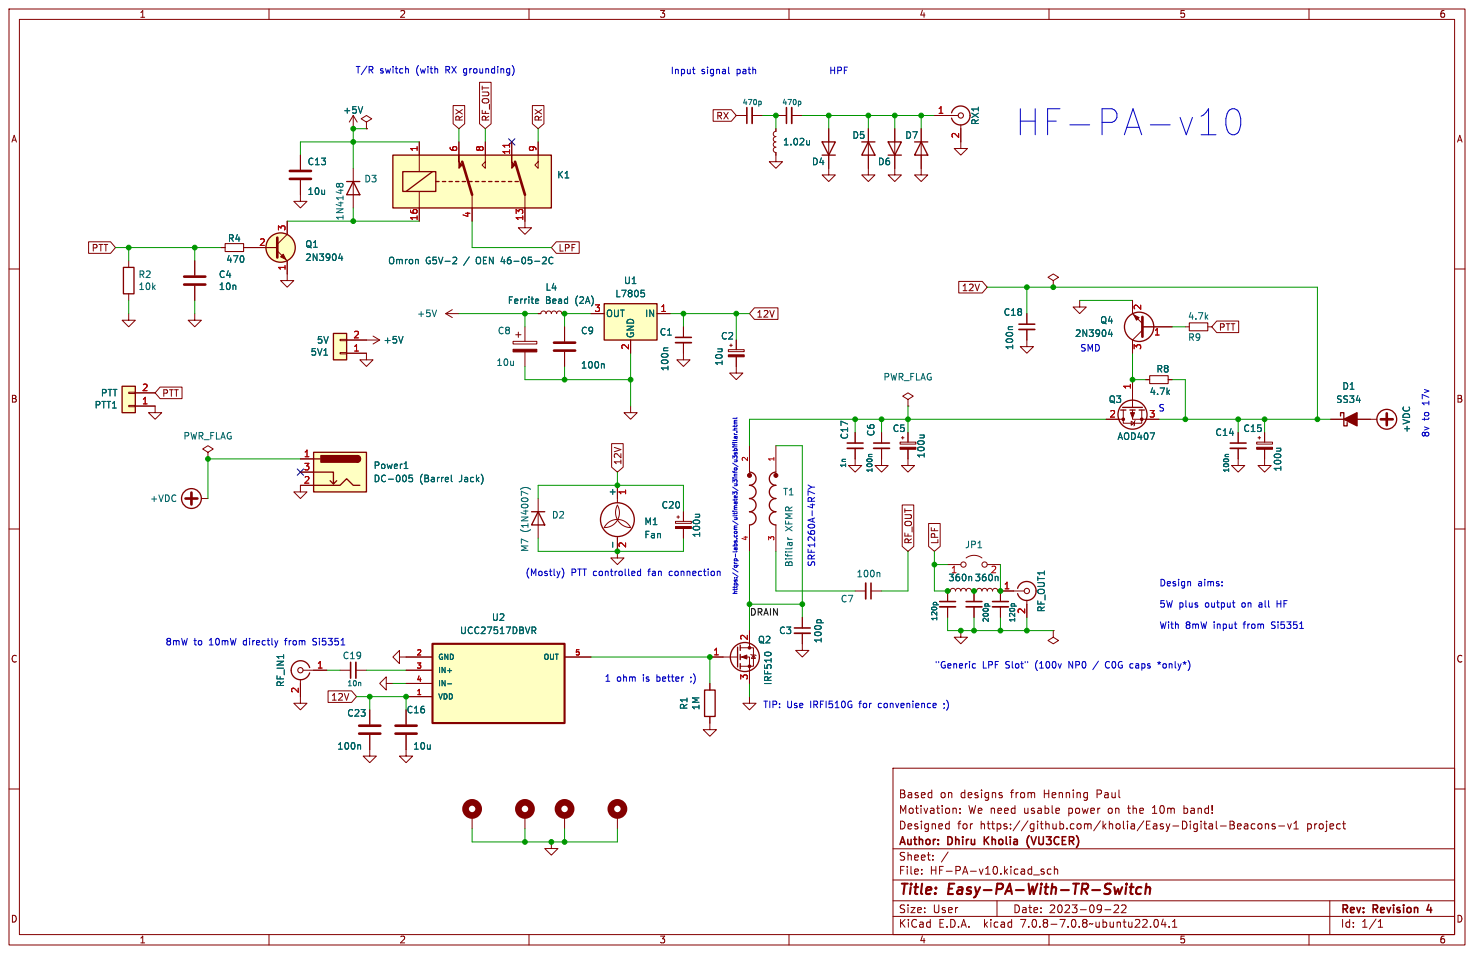
[picture p85: page 1]

Id: 1/1 Title: Easy-PA-With-TR-Switch
