kholia/HF-PA-v10/UCC-Driver-Board/HF-PA-v10.pdf

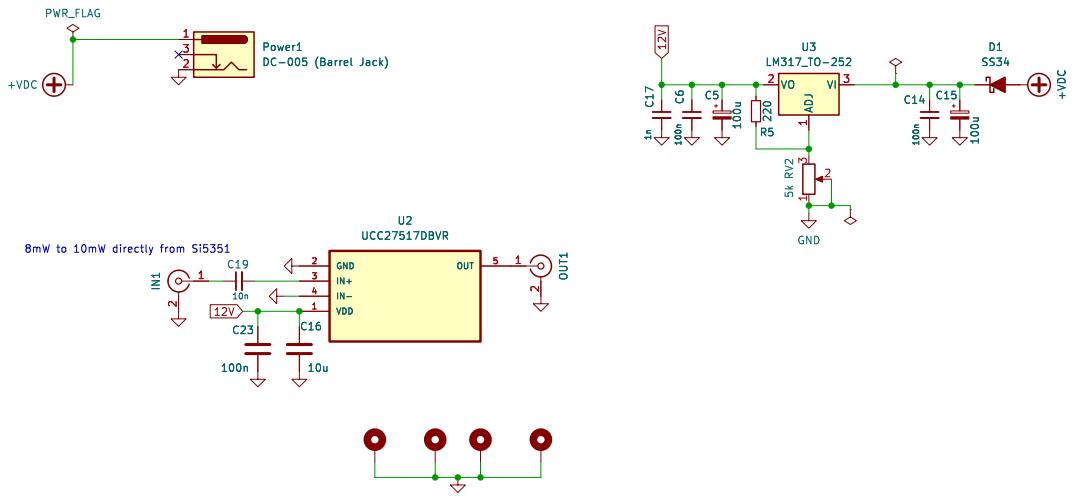
[picture p86: page 1]

3 RV2 5k +VDC C17 1n C15 100u C14100n GNDADJ 1 VO 2 VI 3 U3

Id: 1/1 Title: Easy-PA-With-TR-Switch
