kholia/HF-PA-v10/v3-RD16HHF1/HF-PA-v10.pdf

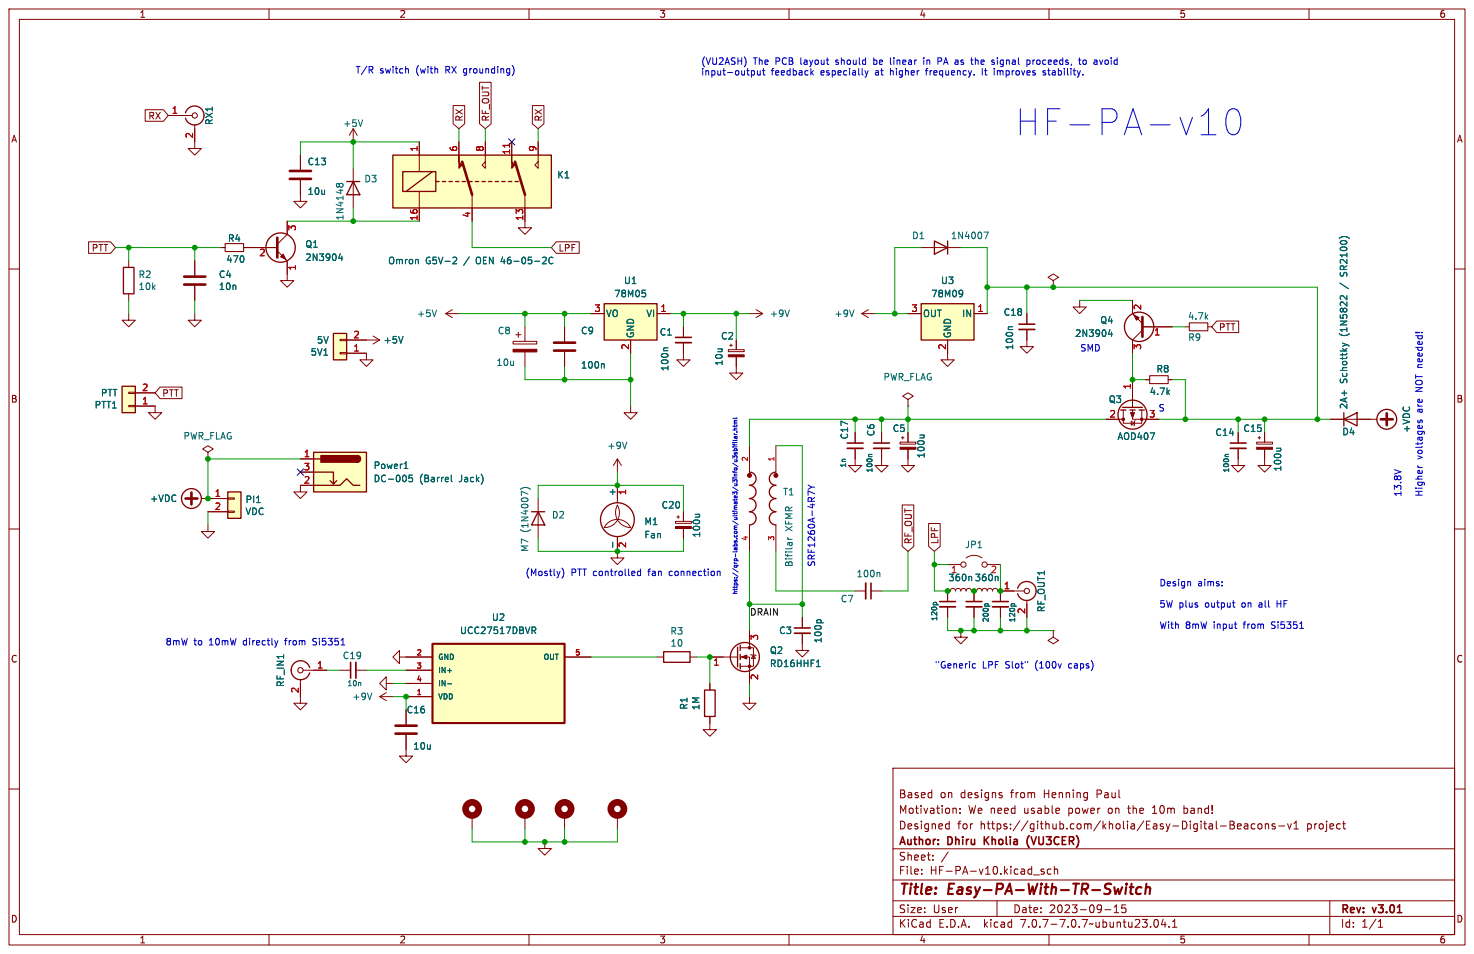
[picture p87: page 1]

Id: 1/1 Title: Easy-PA-With-TR-Switch
