kholia/HF-PA-v10/GSD-Hacks-v7/HF-PA-v10.pdf

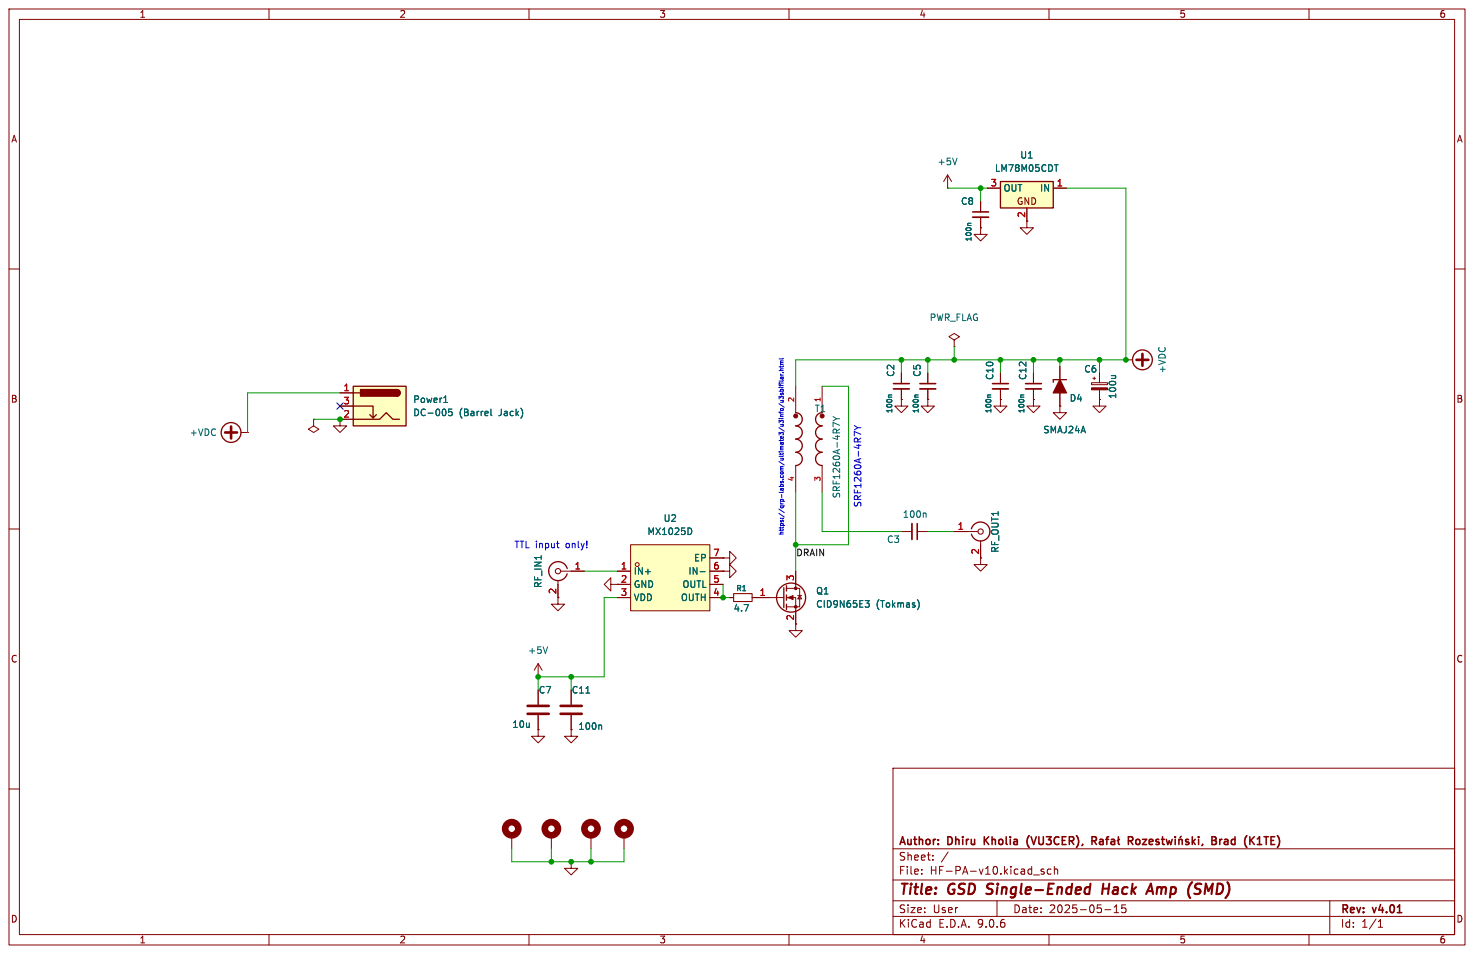
[picture p88: page 1]

3 2 Q1 CID9N65E3 (Tokmas) DRAIN https://qrp-labs.com/ultimate3/u3info/u3sbifilar.html SRF1260A-4R7Y
