kholia/HF-PA-v10/GSD-Hacks-v4-SMD/HF-PA-v10.pdf

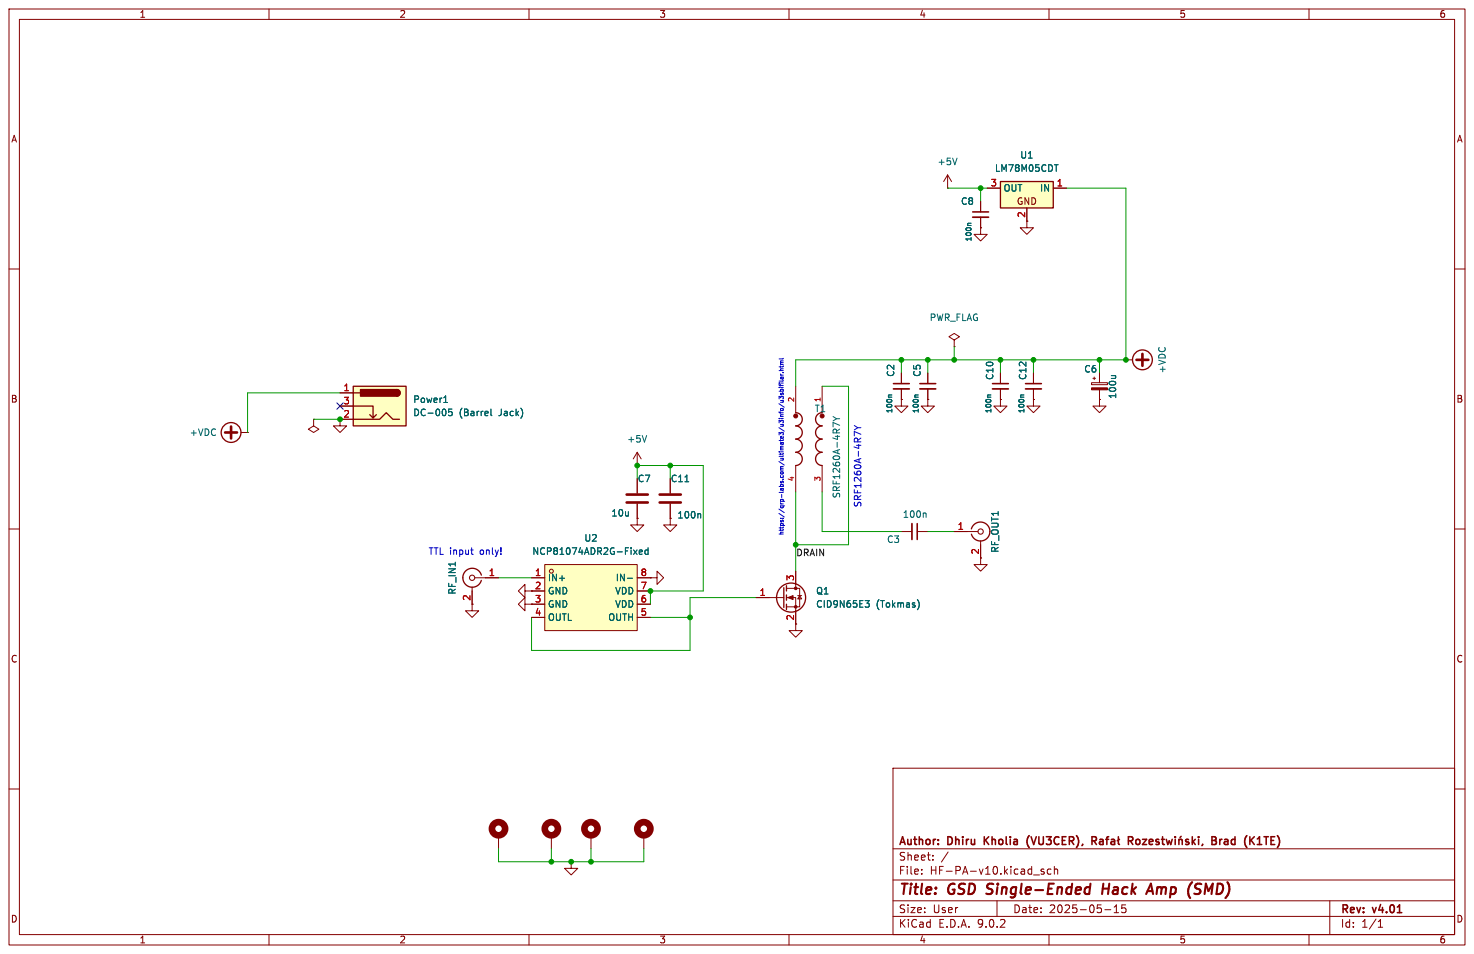
[picture p89: page 1]
