kholia/HF-PA-v10/GSD-Hacks-v5/HF-PA-v10.pdf

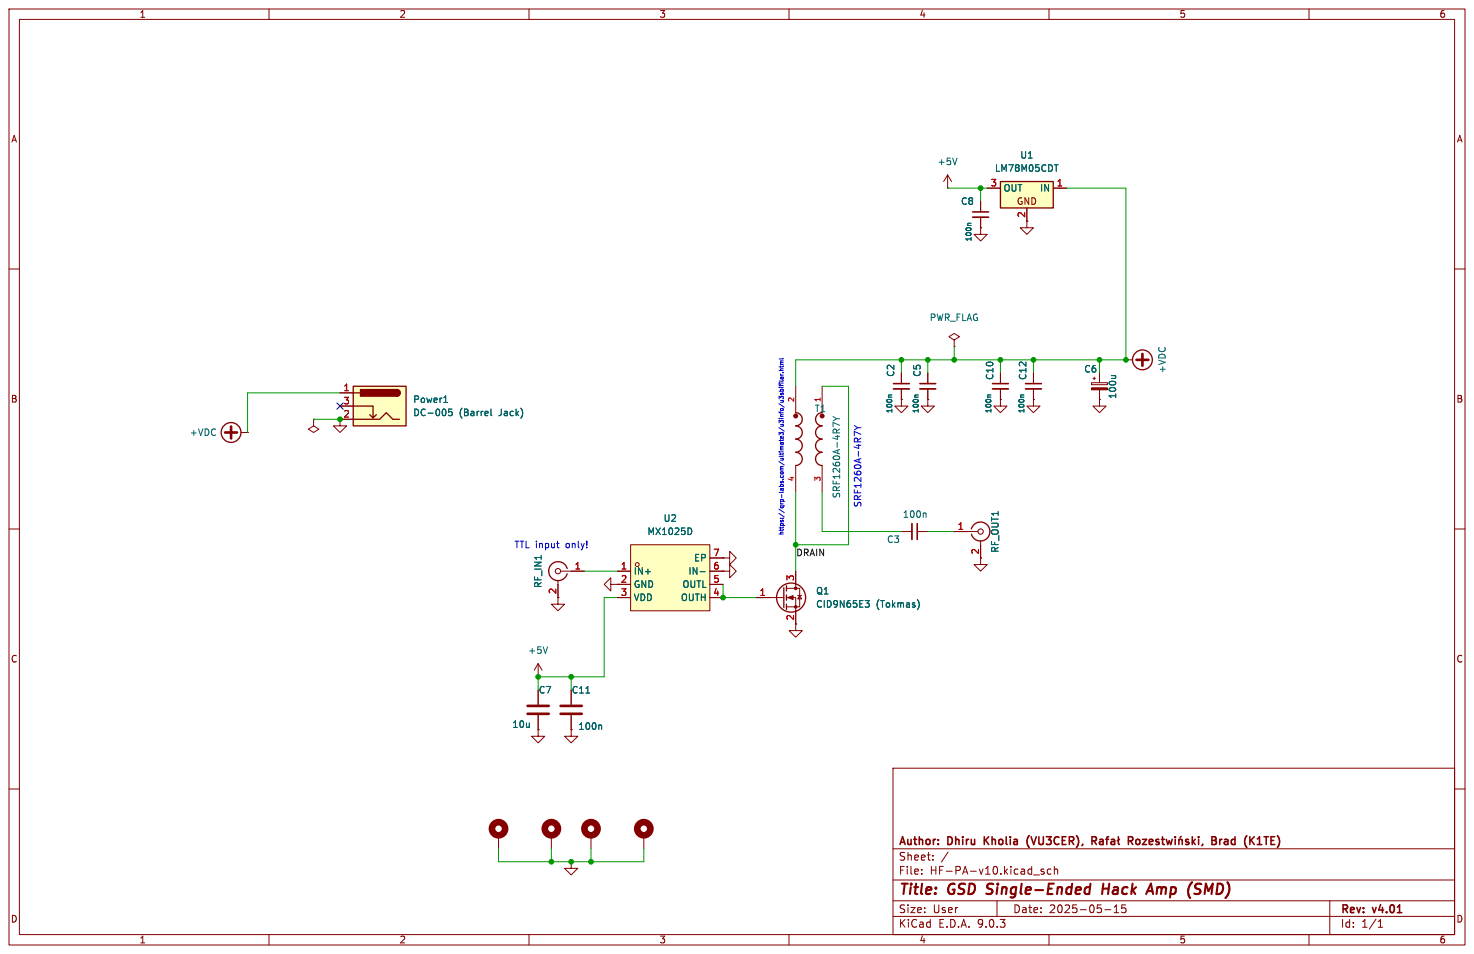
[picture p90: page 1]
