kholia/HF-PA-v10/5V-Production/HF-PA-v10.pdf

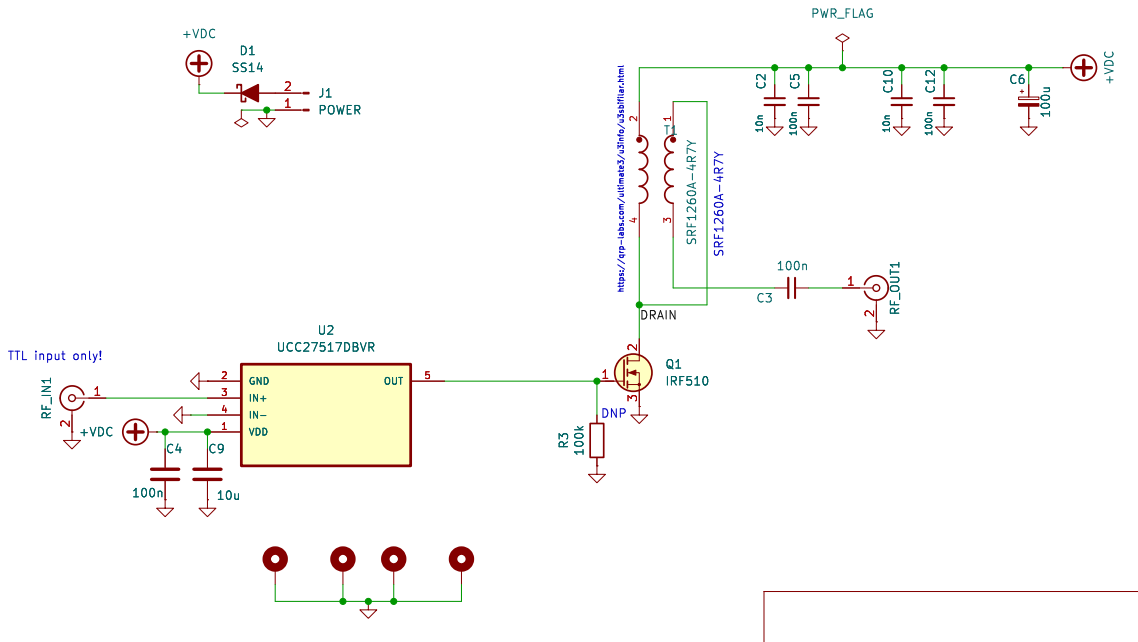
[picture p91: page 1]
