kholia/HF-PA-v10/GSD-Hacks-v1-SMD/HF-PA-v10.pdf

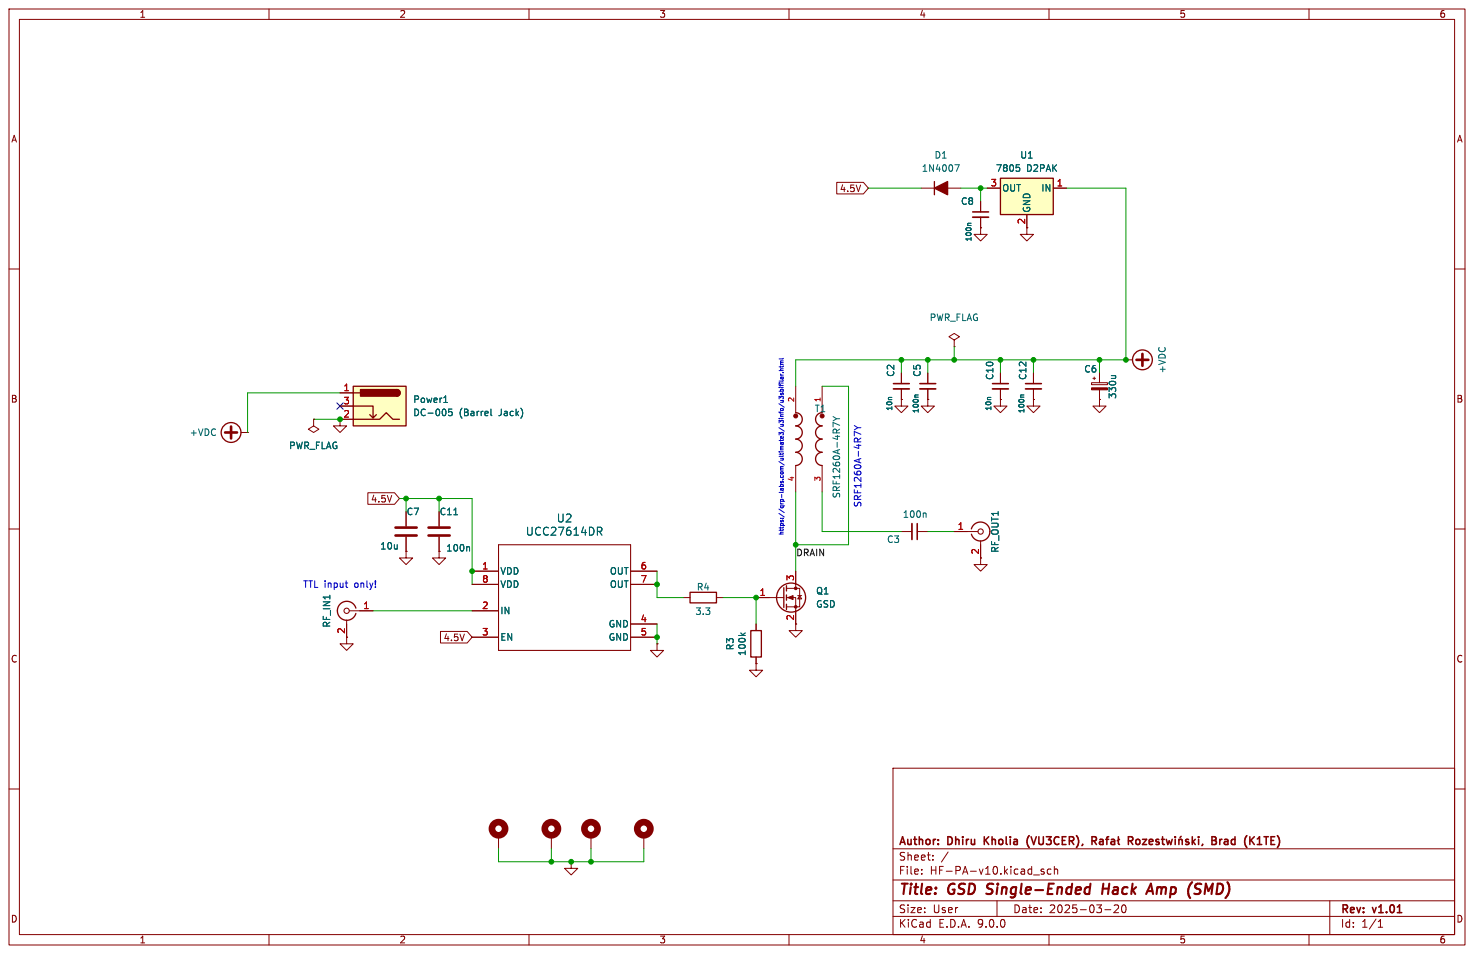
[picture p92: page 1]
