kholia/HF-PA-v10/GSD-Hacks-v2-SMD/HF-PA-v10.pdf

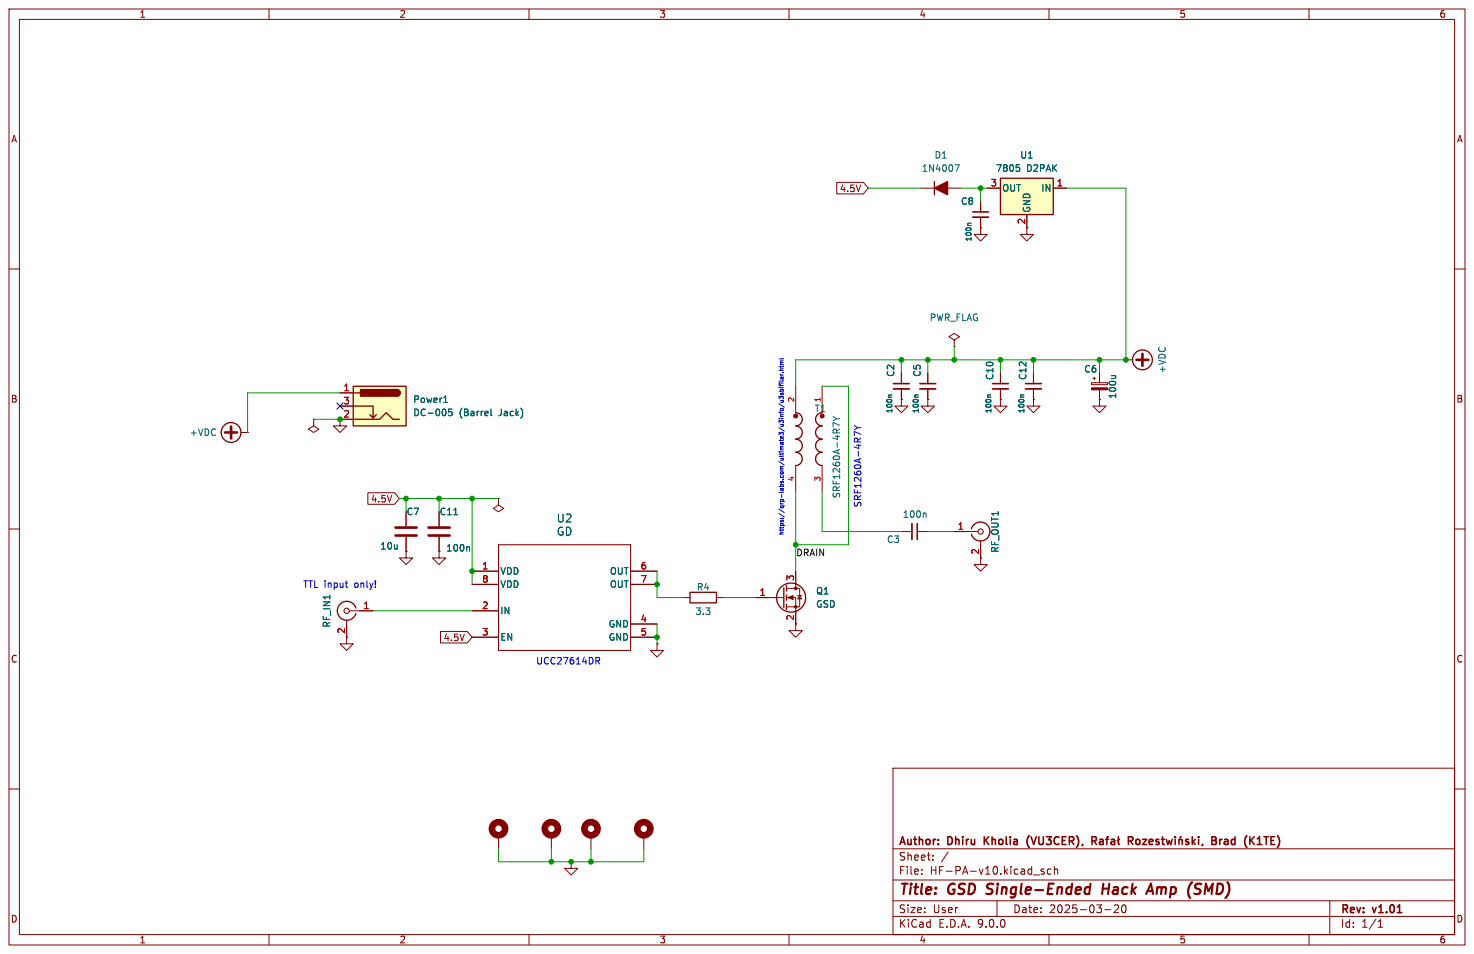
[picture p93: page 1]
