kholia/HF-PA-v10/GSD-Hacks-v3-SMD/HF-PA-v10.pdf

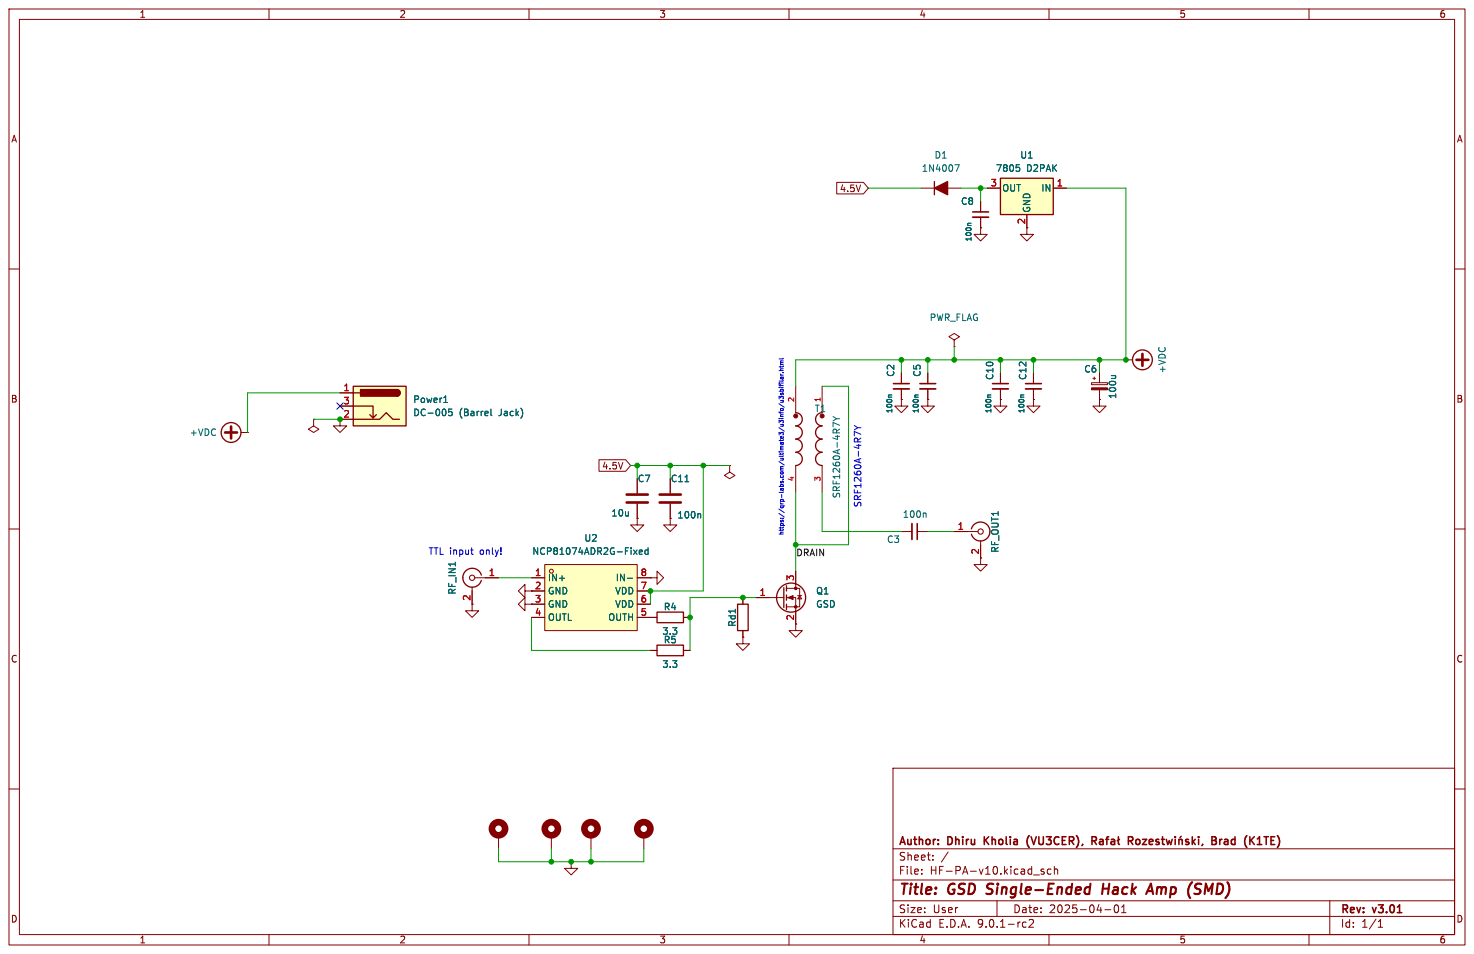
[picture p94: page 1]
