kholia/HF-PA-v10/IRFP-Hacks-v10-SMD/HF-PA-v10.pdf

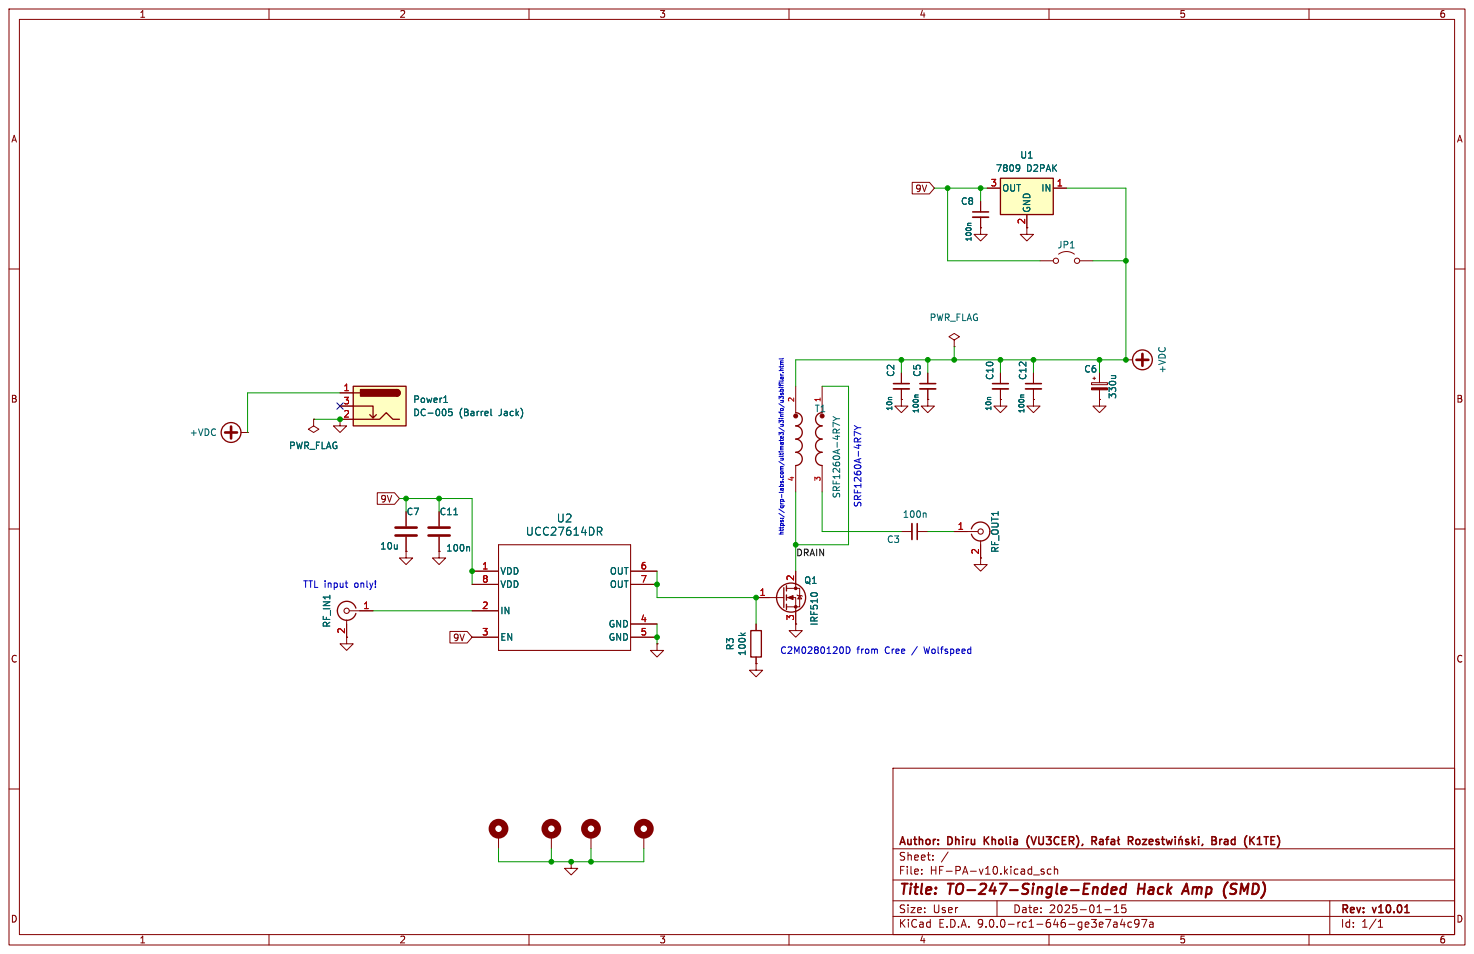
[picture p95: page 1]
