kholia/HF-PA-v10/SiC-QRO-Amp/HF-PA-v10.pdf

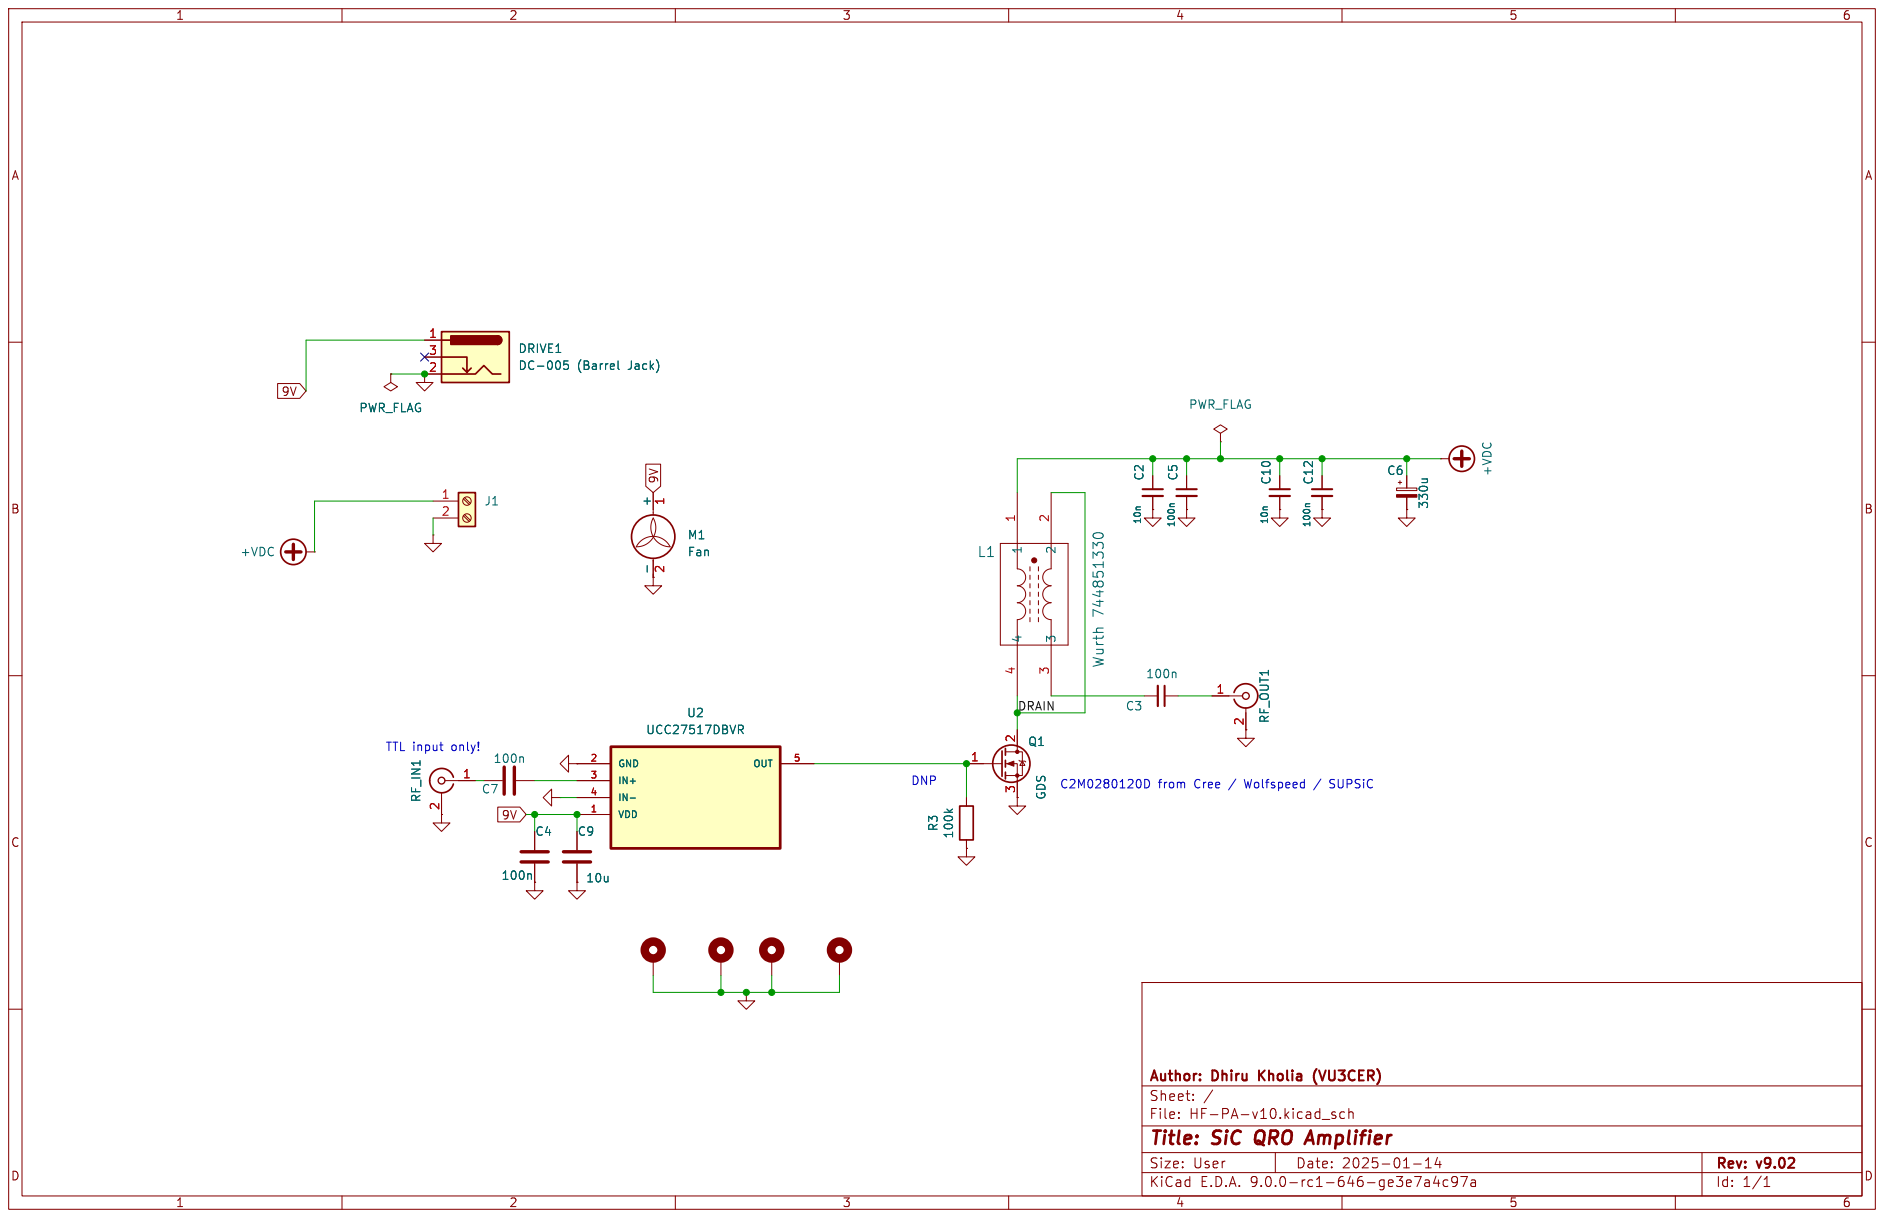
[picture p96: page 1]
