kholia/HF-PA-v10/IRF530-Hack/HF-PA-v10.pdf

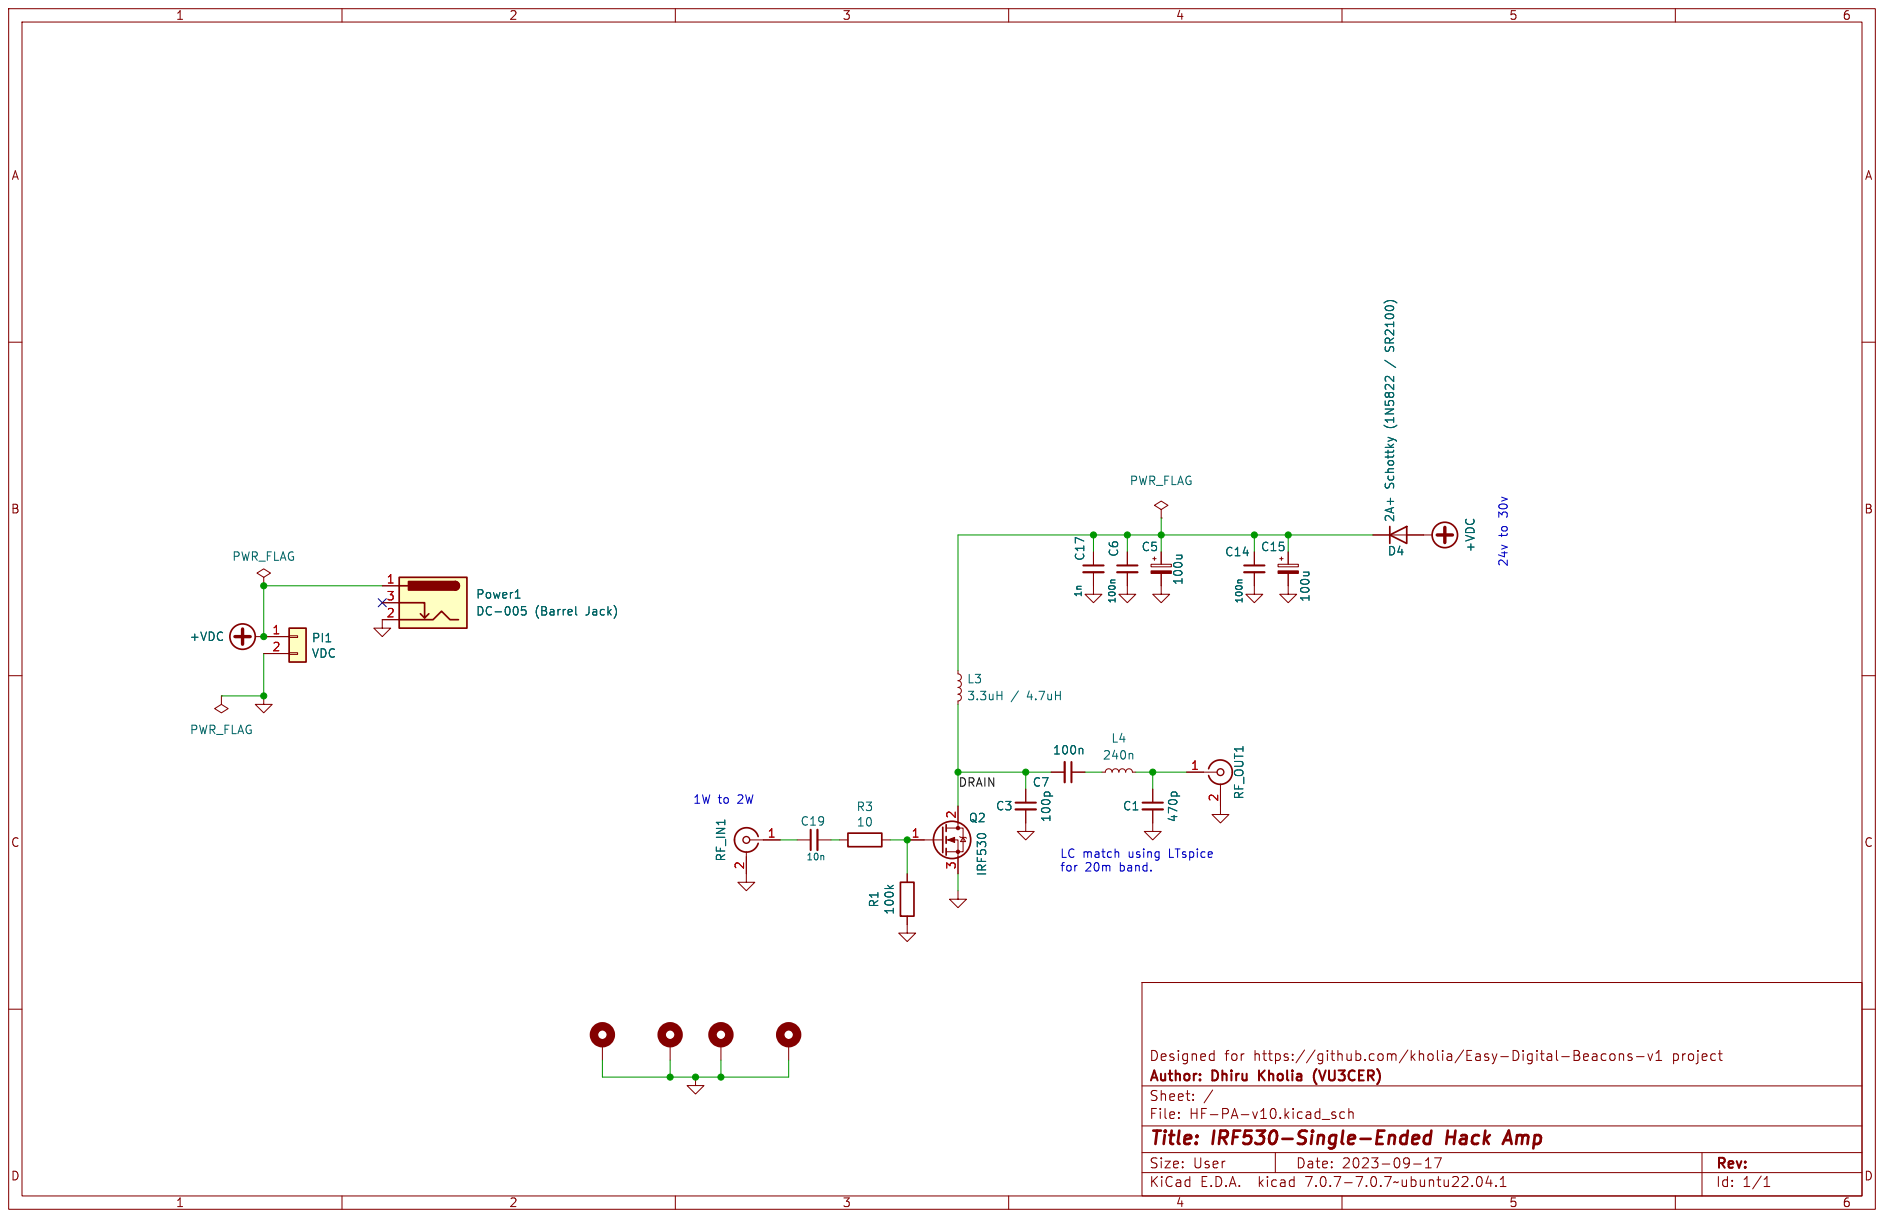
[picture p97: page 1]

LC match using LTspice
