kholia/HF-PA-v10/IRFP-Hacks-v2/HF-PA-v10.pdf

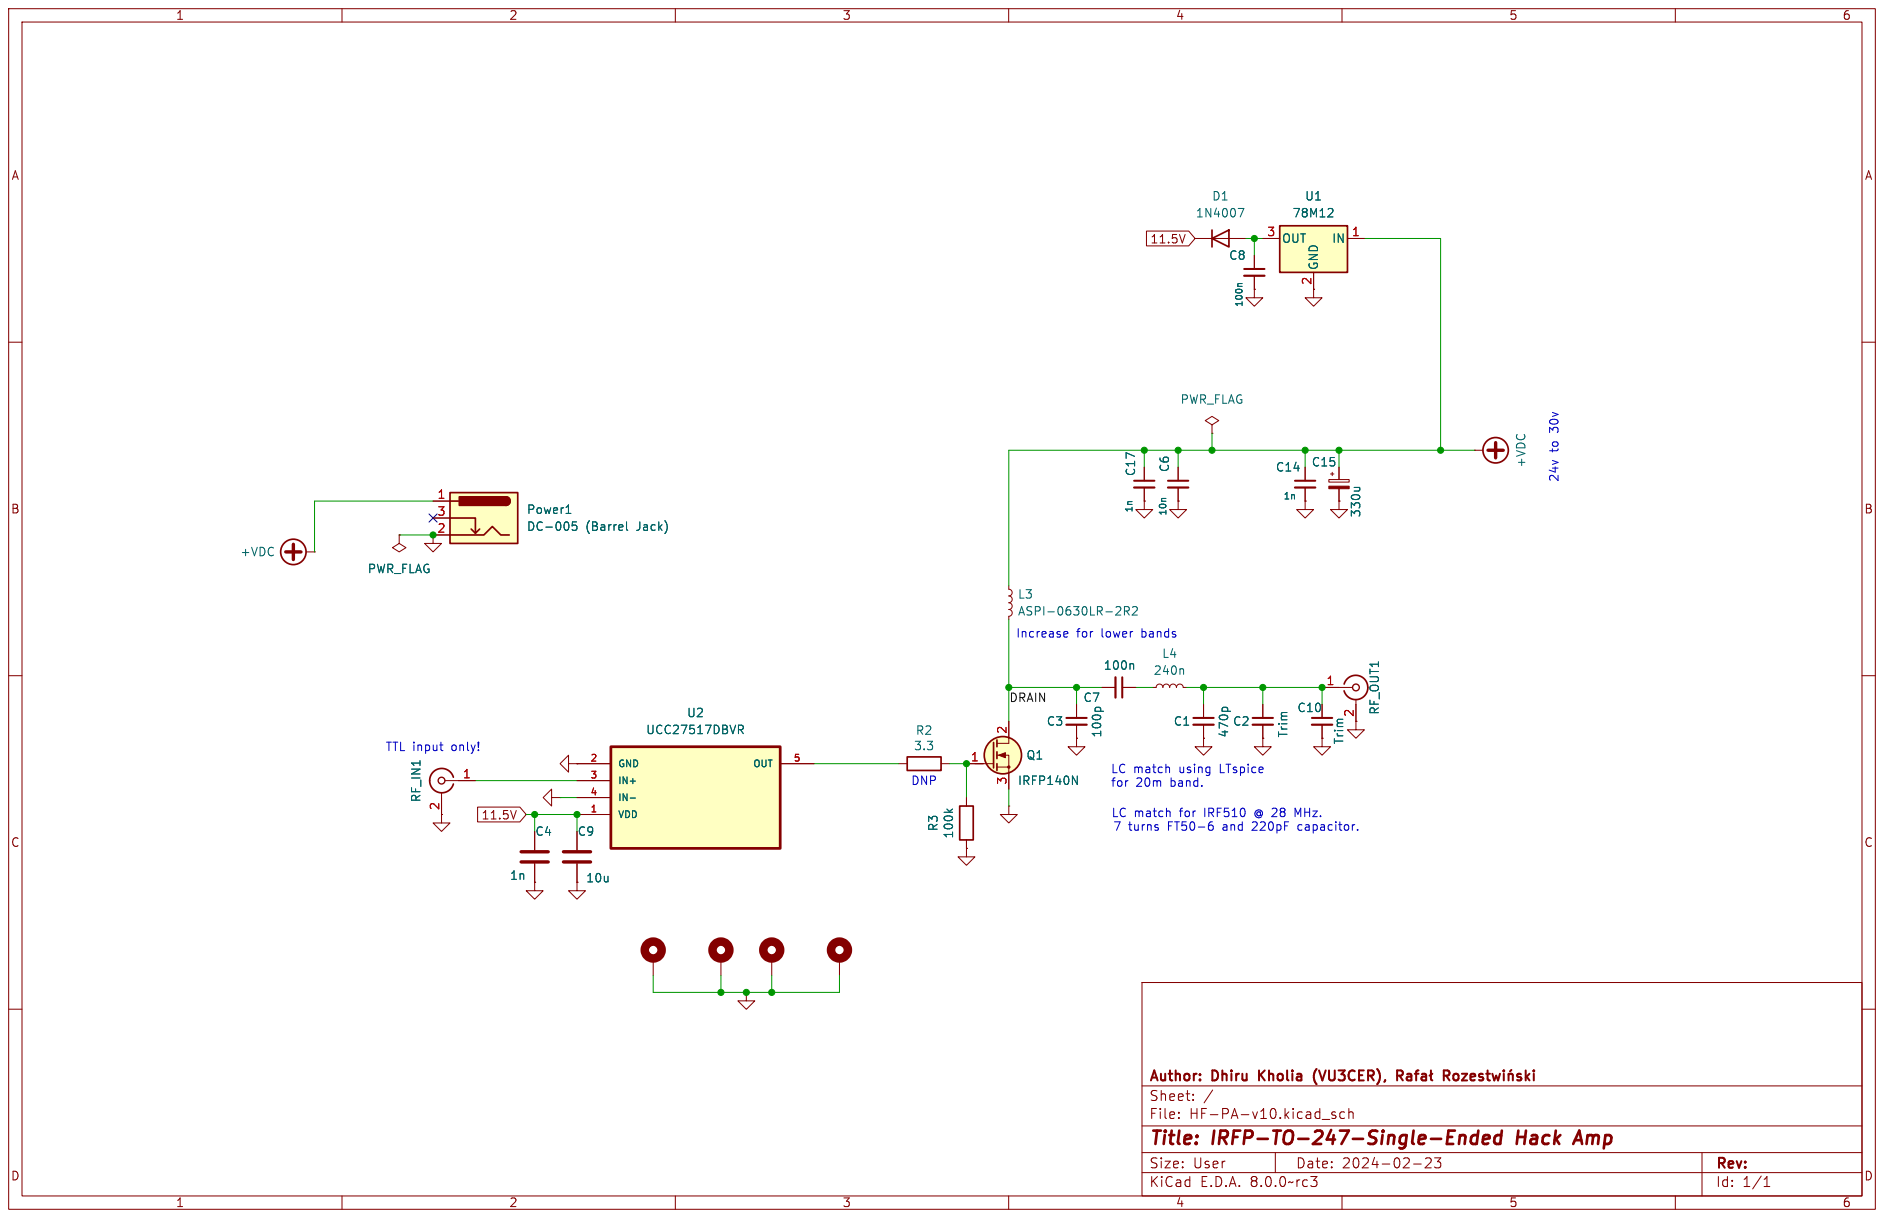
[picture p98: page 1]
