kholia/HF-PA-v10/IRFP-Hacks-v3/HF-PA-v10.pdf

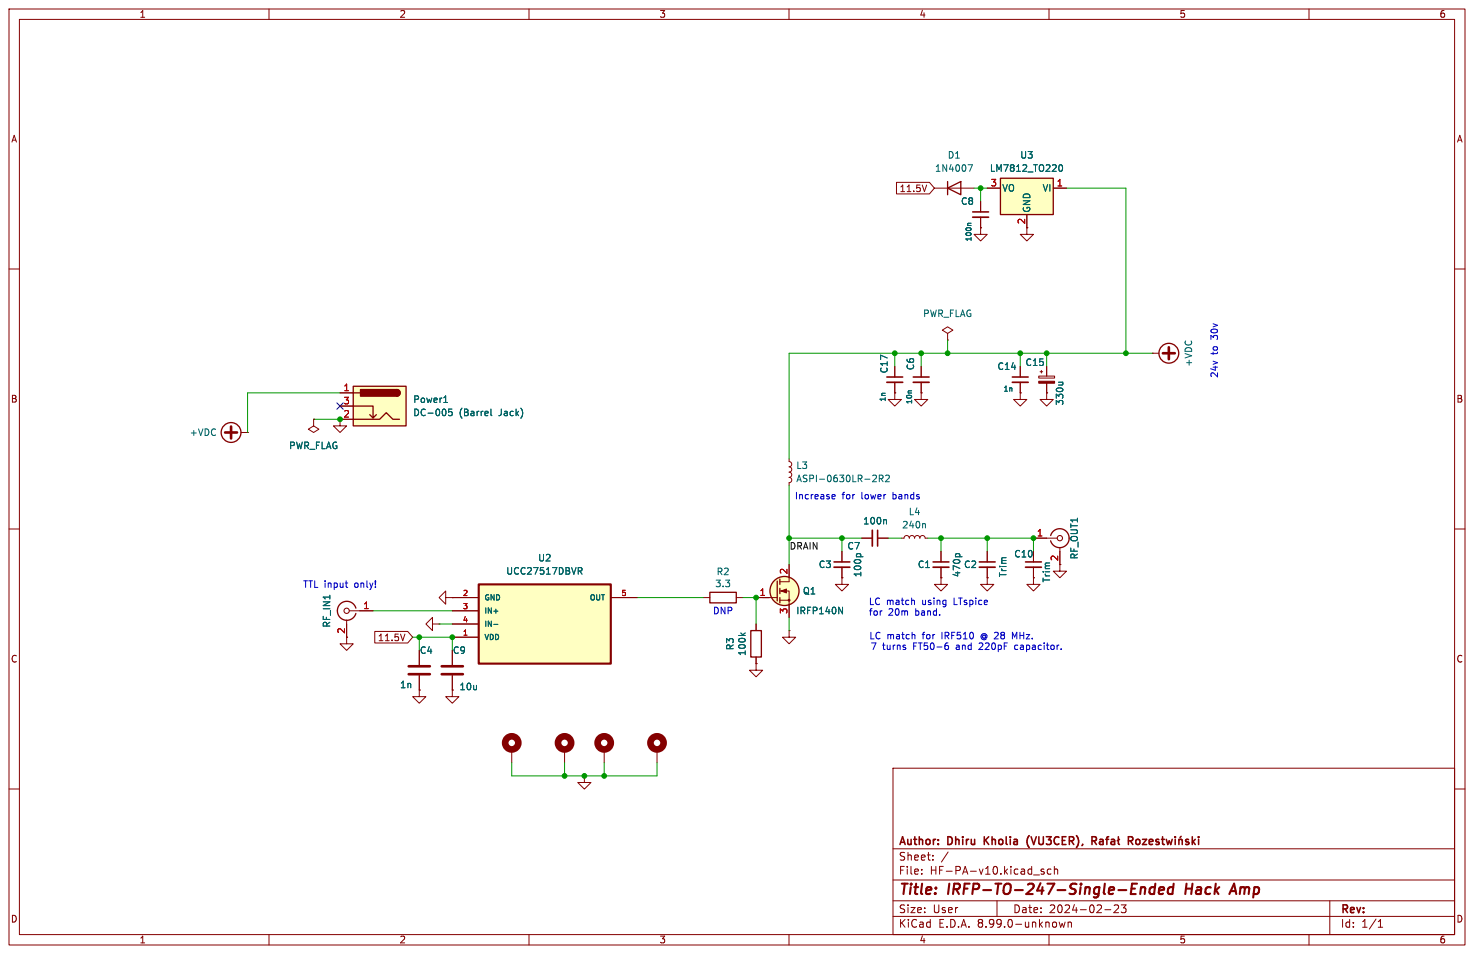
[picture p99: page 1]
