kholia/HF-PA-v10/IRFP-Hacks-v4/HF-PA-v10.pdf

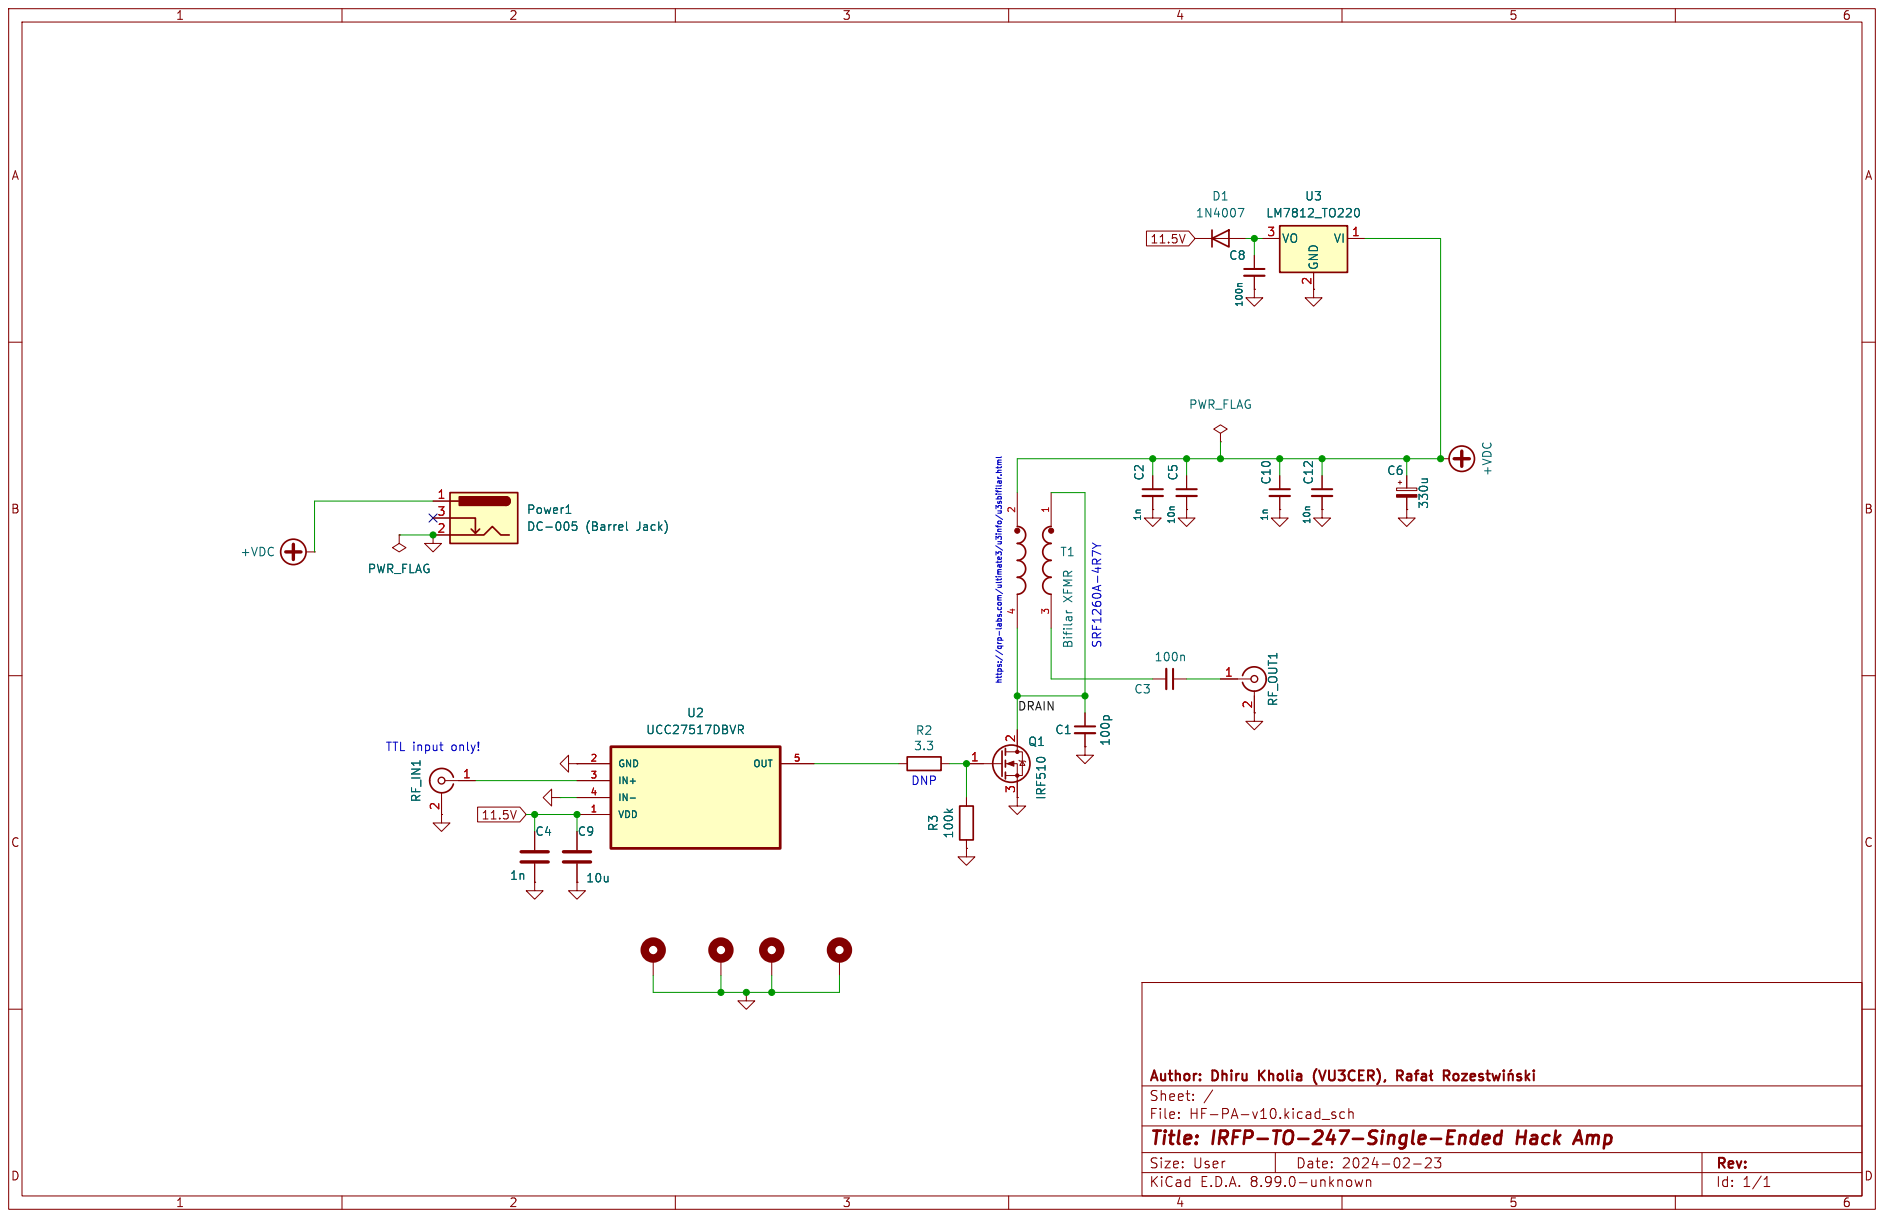
[picture p100: page 1]
