kholia/HF-PA-v10/IRFP-Hacks-v5-SMD/HF-PA-v10.pdf

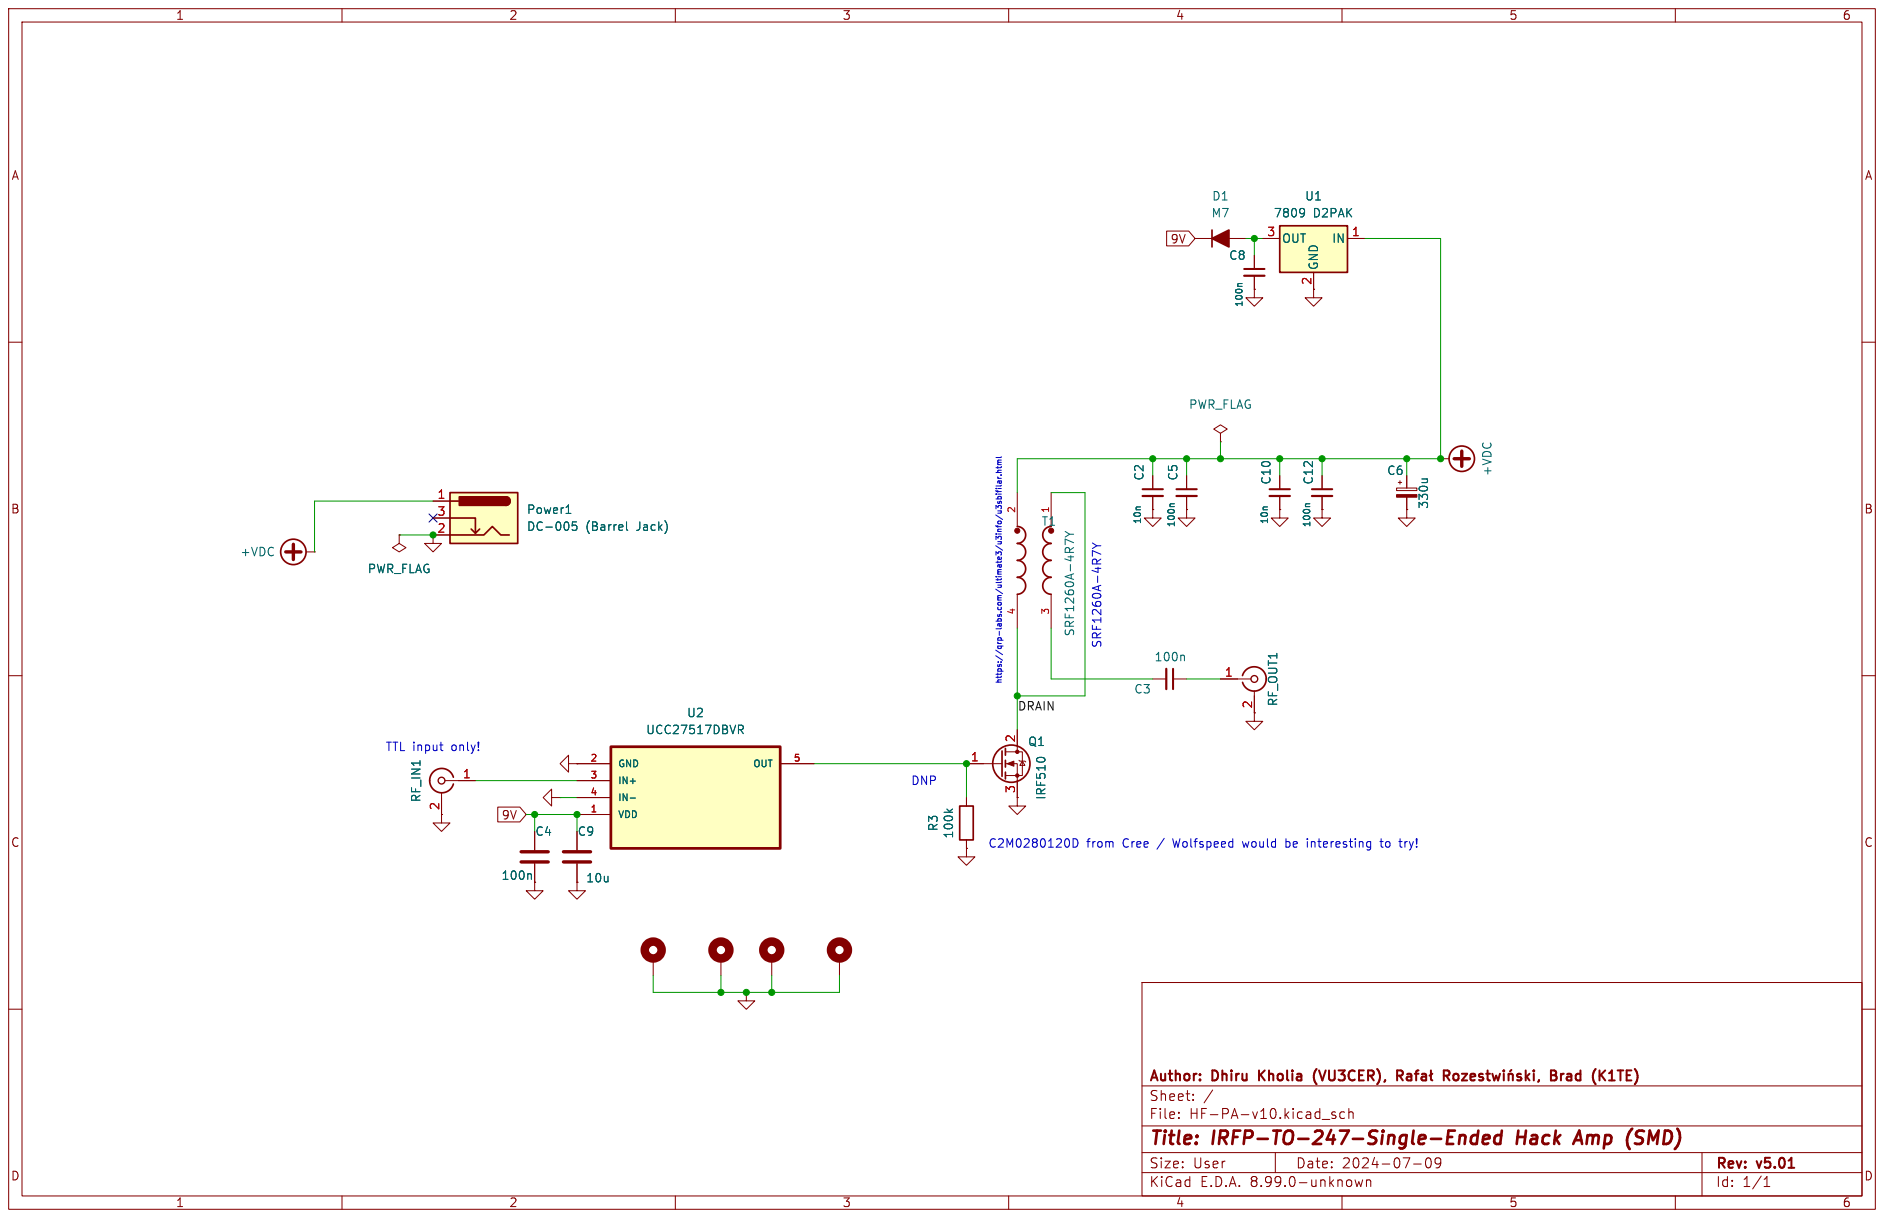
[picture p101: page 1]
