kholia/HF-PA-v10/Linear-Amp-SSB-v1/HF-PA-v10.pdf

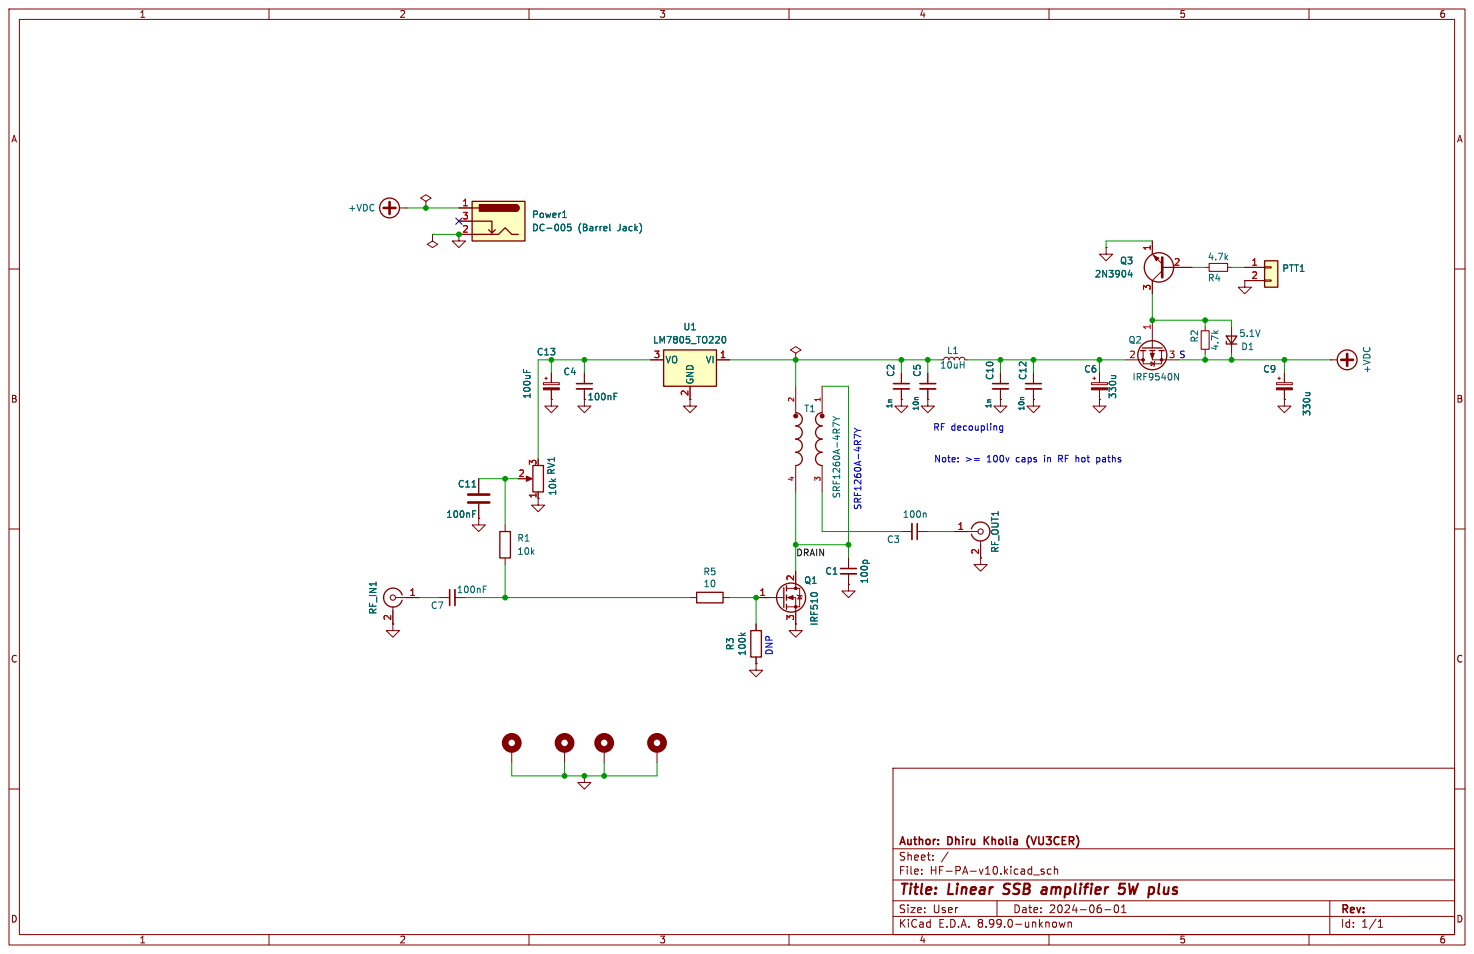
[picture p102: page 1]

Id: 1/1 Title: Linear SSB amplifier 5W plus
