kholia/HF-PA-v10/R4-Minimal-K1TE/HF-PA-v10.pdf

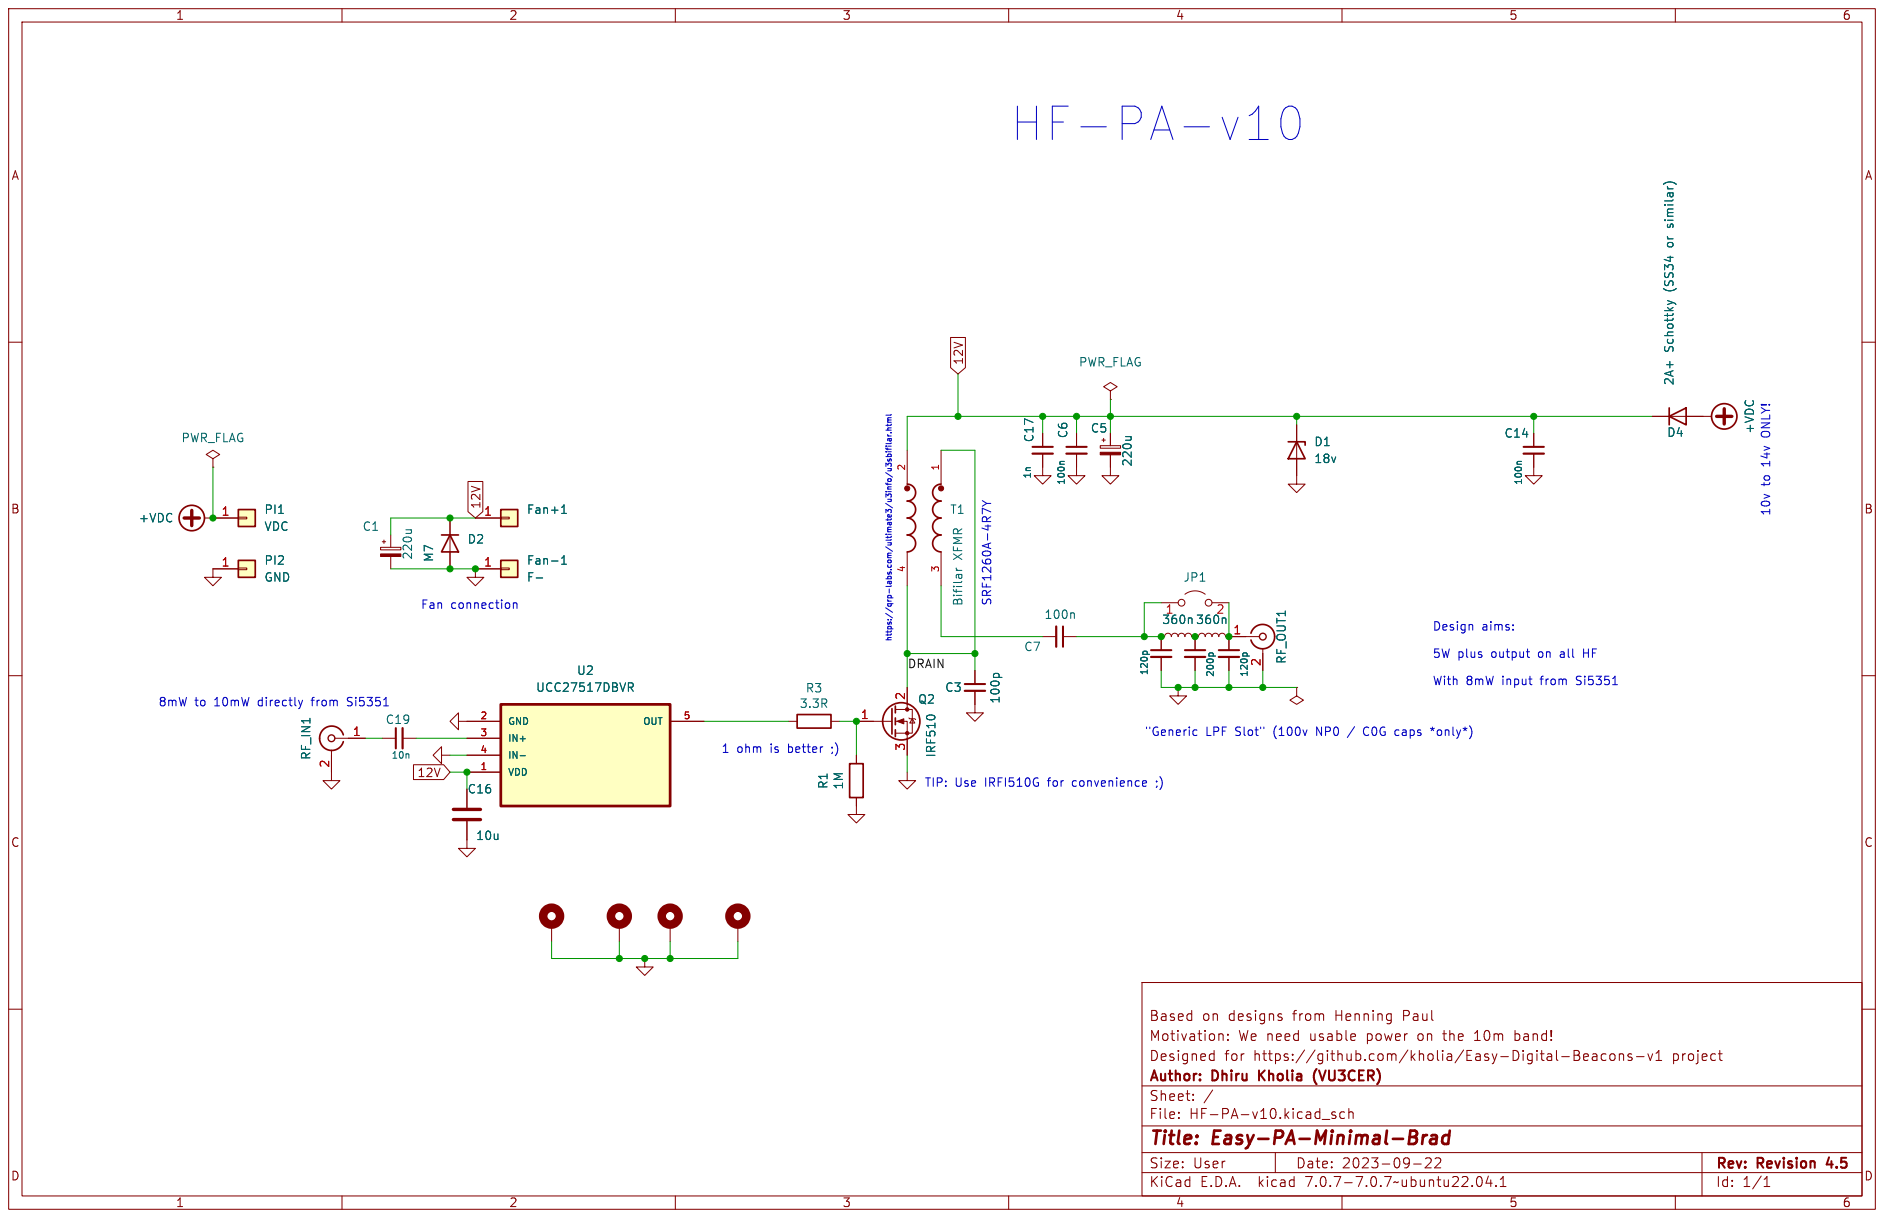
[picture p103: page 1]

2 D4 +VDC 2A+ Schottky (SS34 or similar)

Design aims: 5W plus output on all HF With 8mW input from Si5351

Id: 1/1 Title: Easy-PA-Minimal-Brad
