kholia/HF-PA-v10/IRFP-Hacks-v4/IRF510-LC-Match-Proper.asc

C1: cap; 120p
C3: cap; 200pF
C4: cap; 10nF
C5: cap; 200pF
C6: cap; 120p
L1: ind; 120nH
L2: ind; 2.2µH
L3: ind; 360n
L4: ind; 360n
M1: nmos; IRF510
R2: res; 50
R3: res; 100k
R4: res; 50
V1: voltage; PULSE(0 11 0 1n 1n {0.5*PERIOD} {PERIOD})
V2: voltage; 25
Named nets: 0, VIN, VGS
.param FREQ=28.200E6
.param PERIOD 1/{FREQ}
.tran 0 {1000*PERIOD} {996*PERIOD}
.meas Pin AVG -V(vin)*I(V2)
.meas Vmax MAX V(Vds)
.meas Pout AVG V(Vout)*I(R2)
.meas Ploss AVG V(Vds)*Id(M4)+V(Vgs)*Ig(M4)
.param Rl 100
.param Cl 391p
.param Ll 234n
