kholia/HF-PA-v10/IRFP-Hacks-v7-SMD-With-SSB/sims/Drain-PWM-Modulator.asc

C1: cap; 360n
C2: cap; 360n
L1: ind; 1mH
M1: pmos; IRF9540
Q1: npn; 2n3904-OnSemi
R1: res; 1k
R2: res; 50
R3: res; 1k
V1: voltage; PULSE(0 3.3 0 0.5n 0.5n {0.5*PERIOD} {PERIOD})
V2: voltage; 30
Named nets: 0
.param FREQ=8000
.param PERIOD 1/{FREQ}
.tran 0 {1000*PERIOD} {996*PERIOD}
.meas Pin AVG -V(vin)*I(V2)
.meas Vmax MAX V(Vds)
.meas Pout AVG V(Vout)*I(R2)
.meas Ploss AVG V(Vds)*Id(M4)+V(Vgs)*Ig(M4)
.param Rl 100
.param Cl 391p
.param Ll 234n
