kholia/HF-PA-v10/IRFP-Hacks-v7-SMD-With-SSB/sims/SiC-Amplifier.asc

C1: cap; 100n
C2: cap; 240p
C3: cap; 430p
C4: cap; 240p
L1: ind2; 3.3µ
L2: ind2; 3.3µ
L3: ind; 750nH
L4: ind; 750nH
R3: res; 50
U1: nmos_TO247_3L; C2M0280120D
V1: voltage; PULSE(0 15 0 0.5n 0.5n {0.5*PERIOD} {PERIOD})
V2: voltage; 25
V3: voltage; 50
V4: voltage; 150
Named nets: 0, VIN
.param FREQ=14.074E6
.param PERIOD 1/{FREQ}
.tran 0 {1000*PERIOD} {996*PERIOD}
.meas Pin AVG -V(vin)*I(V2)
.meas Vmax MAX V(Vds)
.meas Pout AVG V(Vout)*I(R2)
.meas Ploss AVG V(Vds)*Id(M4)+V(Vgs)*Ig(M4)
.param Rl 100
.param Cl 391p
.param Ll 234n
K1 L1 L2 1
.lib C2M0280120D.lib
https://www.youtube.com/watch?v=vFCtCPUcJMg
