kholia/HF-PA-v10/R4-Minimal-K1TE/HF-PA-v10.kicad_pcb

## KiCad design R4-Minimal-K1TE/HF-PA-v10.kicad_pcb (2024-09-08, an earlier design)

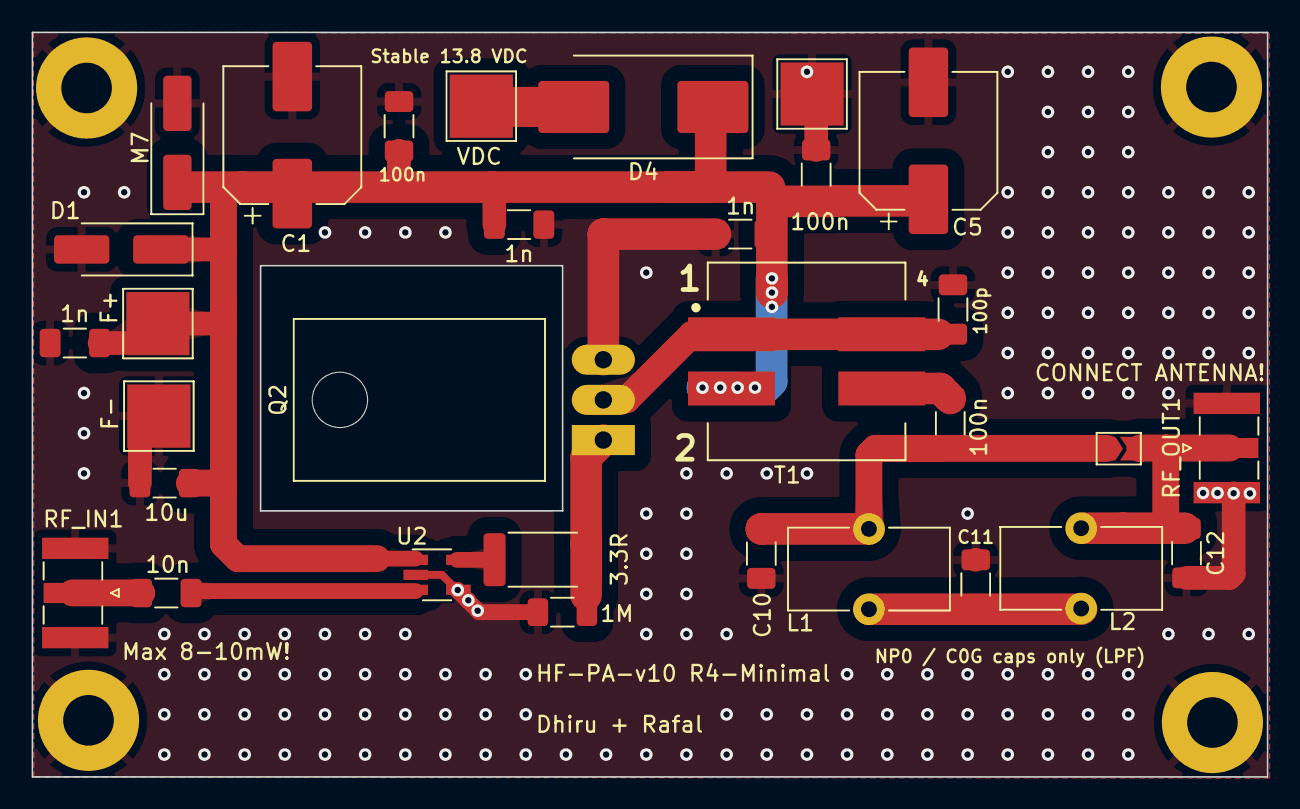
[picture p110: board R4-Minimal-K1TE/HF-PA-v10.kicad_pcb from above]

Board: 2 copper layers, 78.1 x 47.1 mm, 35 parts (0 on the bottom side), 12 nets.

Parts:
C1, C5: 220u; CP_Elec_8x10.5
C2, C4, C17: 1n; C_1206_3216Metric_Pad1.33x1.80mm_HandSolder
C3: 100p; C_1206_3216Metric_Pad1.33x1.80mm_HandSolder
C6, C7, C14: 100n; C_1206_3216Metric_Pad1.33x1.80mm_HandSolder
C10, C12: 120p; C_1206_3216Metric_Pad1.33x1.80mm_HandSolder
C11: 200p; C_1206_3216Metric_Pad1.33x1.80mm_HandSolder
C16: 10u; C_1206_3216Metric_Pad1.33x1.80mm_HandSolder
C19: 10n; C_1206_3216Metric_Pad1.33x1.80mm_HandSolder
D1: 18v; D_SMA_Handsoldering
D2: M7; D_SMA_Handsoldering
D4: 2A+ Schottky (SS34 or similar); D_SMC_Handsoldering
Fan+1: F+; TestPoint_Pad_4.0x4.0mm
Fan-1: F-; TestPoint_Pad_4.0x4.0mm
H1, H2, H3, H4: MountingHole_Pad; MountingHole_3.2mm_M3_Pad
JP1: Jumper_2_Open; SolderJumper-2_P1.3mm_Open_TrianglePad1.0x1.5mm
L1, L2: 360n; L_Toroid_Vertical_L10.0mm_W5.0mm_P5.08mm
PI1: VDC; TestPoint_Pad_4.0x4.0mm
PI2: GND; TestPoint_Pad_4.0x4.0mm
Q2: IRF510; TO-220-3_Horizontal_TabDown
R1: 1M; R_1206_3216Metric_Pad1.30x1.75mm_HandSolder
R3: 3.3R; R_2512_6332Metric_Pad1.40x3.35mm_HandSolder
RF_IN1: SMA; SMA_Samtec_SMA-J-P-X-ST-EM1_EdgeMount
RF_OUT1: SMA; SMA_Samtec_SMA-J-P-X-ST-EM1_EdgeMount
T1: Bifilar XFMR; IND_SRF1260A-4R7Y-Longer-Pads
U2: UCC27517DBVR; SOT-23-5_HandSoldering

Connections:
12V: C1.1, C2.1, C4.1, C5.1, C6.1, C14.1, C16.1, C17.1, D1.1 (K), D2.1 (K), D4.1 (K), Fan+1.1, T1.2, U2.1 (VDD)
+VDC: D4.2 (A), PI1.1
/DRAIN: C3.1, Q2.2 (D), T1.1, T1.4
GND: C1.2, C2.2, C3.2, C4.2, C5.2, C6.2, C10.2, C11.2, C12.2, C14.2, C16.2, C17.2, D1.2 (A), D2.2 (A), Fan-1.1, H1.1, H2.1, H3.1, H4.1, PI2.1, Q2.3 (S), R1.2, RF_IN1.2 (Ext), RF_OUT1.2 (Ext), U2.2 (GND), U2.4 (IN-)
unnamed: C7.2, T1.3
unnamed: C11.1, L1.2, L2.1
unnamed: C7.1, C10.1, JP1.1 (A), L1.1
unnamed: C12.1, JP1.2 (B), L2.2, RF_OUT1.1 (In)
unnamed: Q2.1 (G), R1.1, R3.1
unnamed: C19.1, RF_IN1.1 (In)
unnamed: C19.2, U2.3 (IN+)
unnamed: R3.2, U2.5 (OUT)
