kholia/HF-PA-v10/IRFP-Hacks/HF-PA-v10.kicad_pcb

## KiCad design IRFP-Hacks/HF-PA-v10.kicad_pcb (2024-09-08)

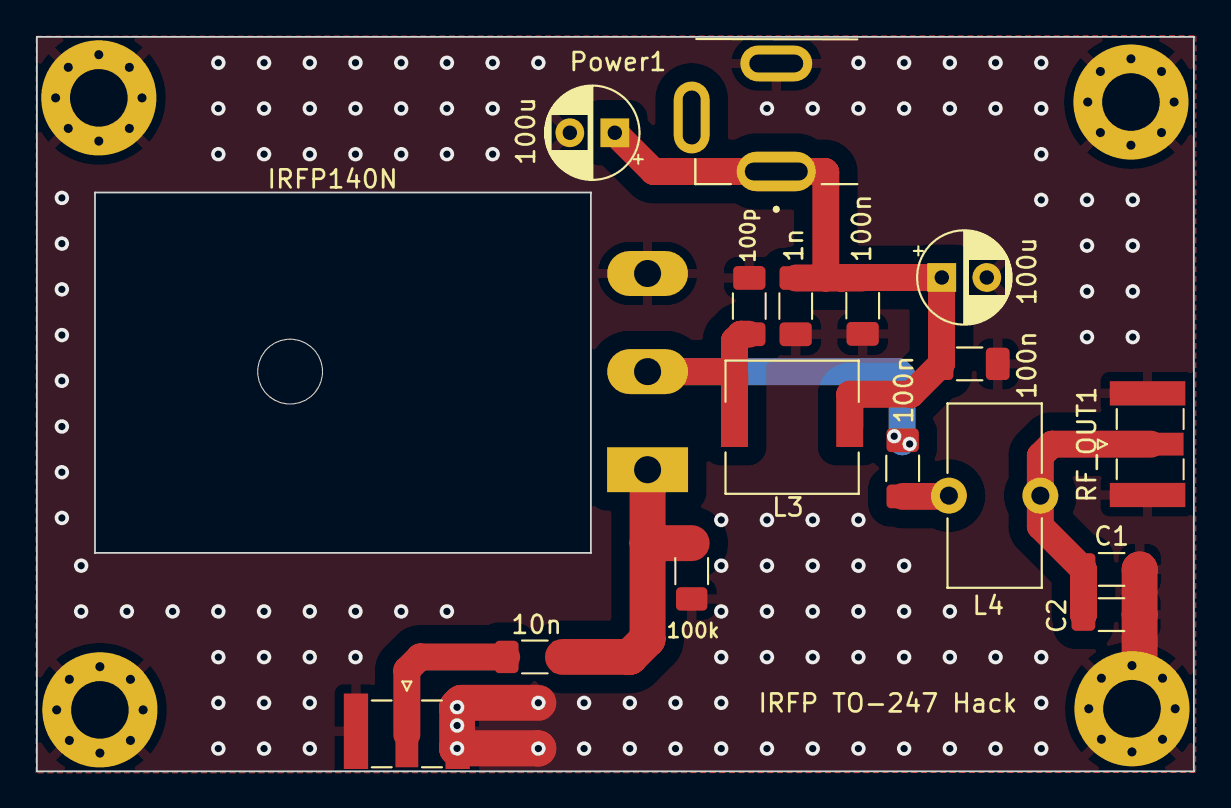
[picture p111: board IRFP-Hacks/HF-PA-v10.kicad_pcb from above]

Board: 2 copper layers, 64.3 x 40.8 mm, 21 parts (0 on the bottom side), 7 nets.

Parts:
C1: 470p; C_1206_3216Metric_Pad1.33x1.80mm_HandSolder
C2: Trim; C_1206_3216Metric_Pad1.33x1.80mm_HandSolder
C3: 100p; C_1206_3216Metric_Pad1.33x1.80mm_HandSolder
C5, C15: 100u; CP_Radial_D5.0mm_P2.50mm
C6, C7, C14: 100n; C_1206_3216Metric_Pad1.33x1.80mm_HandSolder
C17: 1n; C_1206_3216Metric_Pad1.33x1.80mm_HandSolder
C19: 10n; C_1206_3216Metric_Pad1.33x1.80mm_HandSolder
H1, H2, H3, H4: MountingHole_Pad; MountingHole_3.2mm_M3_Pad_Via
L3: 3.3uH / 4.7uH; L_7.3x7.3_H3.5
L4: 240n; L_Toroid_Vertical_L10.0mm_W5.0mm_P5.08mm
Power1: DC-005 (Barrel Jack); XKB_DC-005-5A-2.0_Modded
Q1: IRFP140N; TO-247-3_Horizontal_TabDown_Modded
R1: 100k; R_1206_3216Metric_Pad1.30x1.75mm_HandSolder
RF_IN1: SMA; SMA_Samtec_SMA-J-P-X-ST-EM1_EdgeMount
RF_OUT1: SMA; SMA_Samtec_SMA-J-P-X-ST-EM1_EdgeMount

Connections:
+VDC: C5.1, C6.1, C14.1, C15.1, C17.1, L3.1, Power1.1
/DRAIN: C3.1, C7.2, L3.2, Q1.2 (D)
GND: C1.2, C2.2, C3.2, C5.2, C6.2, C14.2, C15.2, C17.2, H1.1, H2.1, H3.1, H4.1, Power1.2, Q1.3 (S), R1.2, RF_IN1.2 (Ext), RF_OUT1.2 (Ext)
unnamed: C7.1, L4.1
unnamed: C19.2, Q1.1 (G), R1.1
unnamed: C19.1, RF_IN1.1 (In)
unnamed: C1.1, C2.1, L4.2, RF_OUT1.1 (In)
