kholia/HF-PA-v10/IRFP-Hacks-v4/HF-PA-v10.kicad_pcb

## KiCad design IRFP-Hacks-v4/HF-PA-v10.kicad_pcb (2024-09-08, an earlier design)

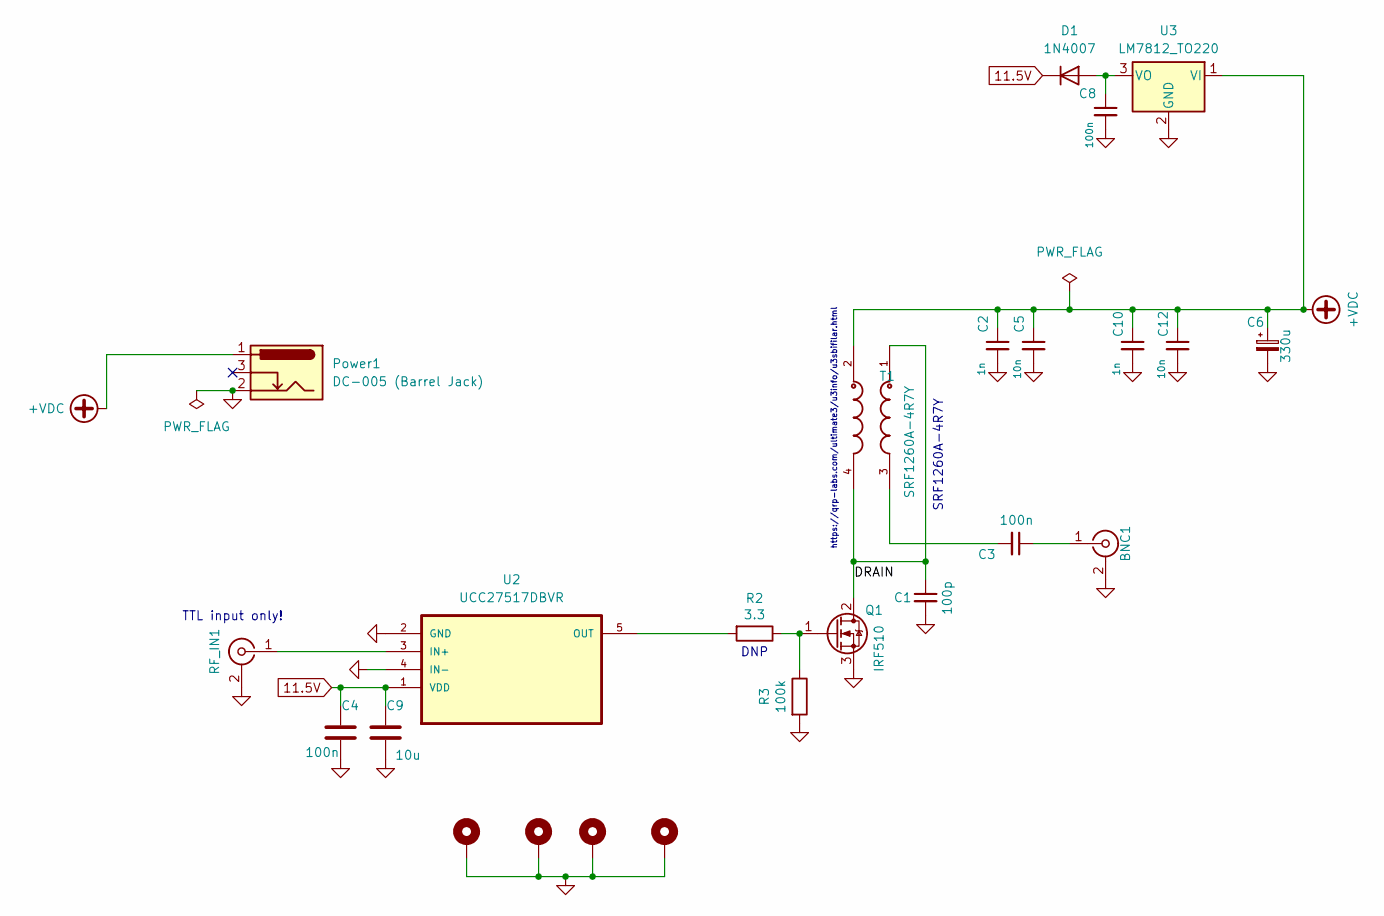
[picture p112: schematic HF-PA-v10.kicad_sch, IRFP-TO-247-Single-Ended Hack Amp]

Parts:
BNC1: SMA; SMA_Samtec_SMA-J-P-X-ST-EM1_EdgeMount
C1: 100p; C_1206_3216Metric_Pad1.33x1.80mm_HandSolder
C2, C10: 1n; C_1206_3216Metric_Pad1.33x1.80mm_HandSolder
C3, C4, C8: 100n; C_1206_3216Metric_Pad1.33x1.80mm_HandSolder
C5, C12: 10n; C_1206_3216Metric_Pad1.33x1.80mm_HandSolder
C6: 330u; CP_Radial_D8.0mm_P5.00mm
C9: 10u; C_1206_3216Metric_Pad1.33x1.80mm_HandSolder
D1: 1N4007; D_DO-41_SOD81_P2.54mm_Vertical_KathodeUp
H1, H2, H3, H4: MountingHole_Pad; MountingHole_3.2mm_M3_Pad_Via
Power1: DC-005 (Barrel Jack); XKB_DC-005-5A-2.0_Modded
Q1: IRF510; TO-247-3_Horizontal_TabDown_Modded
R2: 3.3; R_1206_3216Metric_Pad1.30x1.75mm_HandSolder
R3: 100k; R_1206_3216Metric_Pad1.30x1.75mm_HandSolder
RF_IN1: SMA; SMA_Samtec_SMA-J-P-X-ST-EM1_EdgeMount
T1: SRF1260A-4R7Y; IND_SRF1260A-4R7Y-Longer-Pads
U2: UCC27517DBVR; TSOT-23-5_HandSoldering
U3: LM7812_TO220; TO-220-3_Horizontal_TabDown

Connections:
11.5V: C4.1, C9.1, D1.1 (K), U2.1 (VDD)
+VDC: C2.1, C5.1, C6.1, C10.1, C12.1, Power1.1, T1.2, U3.1 (VI)
/DRAIN: C1.1, Q1.2 (D), T1.1, T1.4
GND: C1.2, C2.2, C4.2, C5.2, C6.2, C8.2, C9.2, C10.2, C12.2, H1.1, H2.1, H3.1, H4.1, Power1.2, Q1.3 (S), R3.2, RF_IN1.2 (Ext), U2.2 (GND), U2.4 (IN-), U3.2 (GND); also elsewhere on the board
unnamed: C3.2, T1.3
unnamed: C8.1, D1.2 (A), U3.3 (VO)
unnamed: Q1.1 (G), R2.1, R3.1
unnamed: RF_IN1.1 (In), U2.3 (IN+)
unnamed 8: C3.1; also elsewhere on the board
unnamed: R2.2, U2.5 (OUT)

Notes on the sheet:
DNP
https://qrp-labs.com/ultimate3/u3info/u3sbifilar.html
SRF1260A-4R7Y
TTL input only!

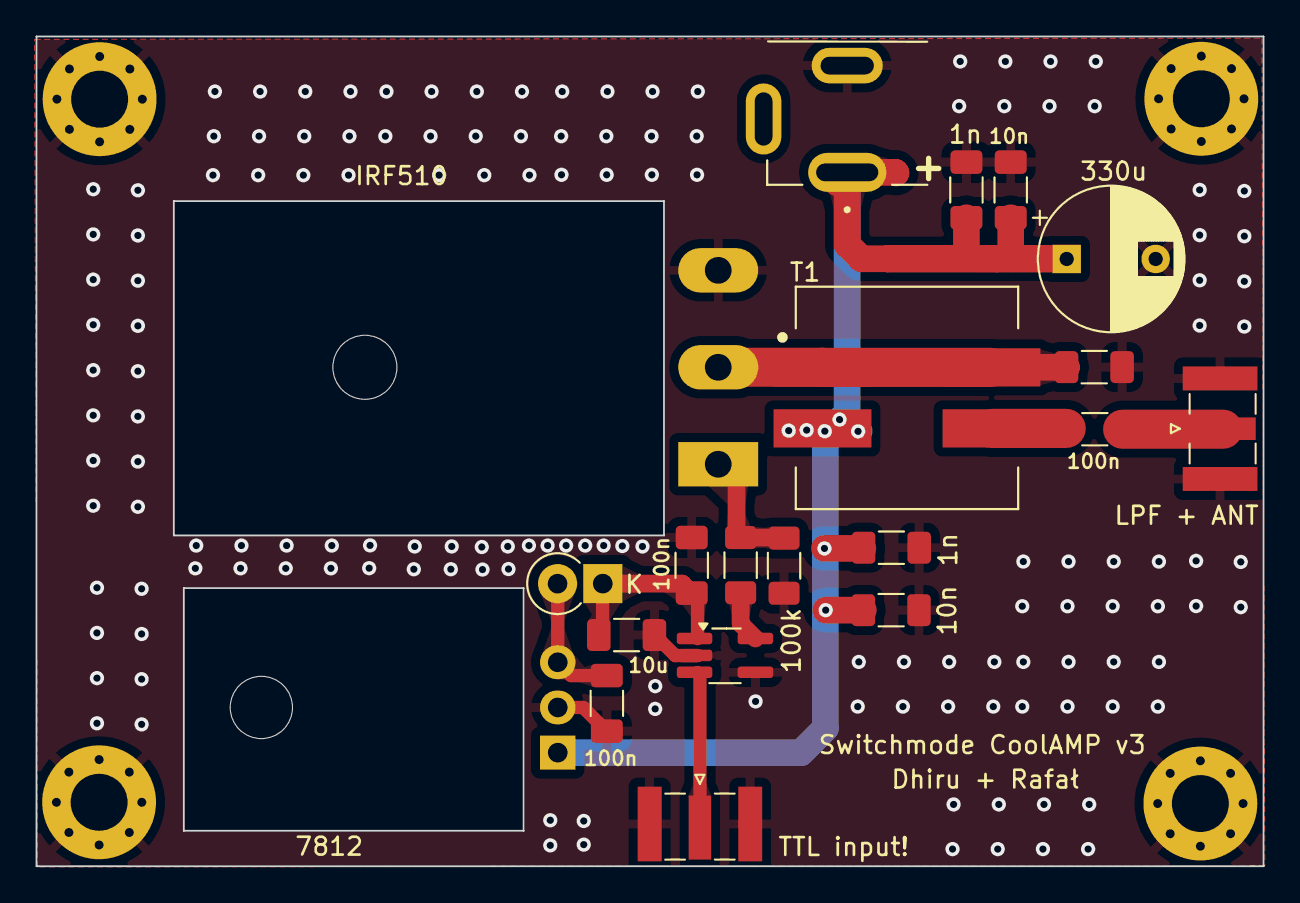
[picture p113: board IRFP-Hacks-v4/HF-PA-v10.kicad_pcb from above]

Board: 2 copper layers, 69.0 x 46.6 mm, 24 parts (0 on the bottom side), 10 nets.

Other parts of the board:
RF_OUT1: SMA; SMA_Samtec_SMA-J-P-X-ST-EM1_EdgeMount

Their connections:
GND: RF_OUT1.2 (Ext); also elsewhere on the board
unnamed 8: RF_OUT1.1 (In); also elsewhere on the board
