kholia/HF-PA-v10/Digital-PA-v3/digital-amp.kicad_pcb

## KiCad design Digital-PA-v3/digital-amp.kicad_pcb (2024-09-08)

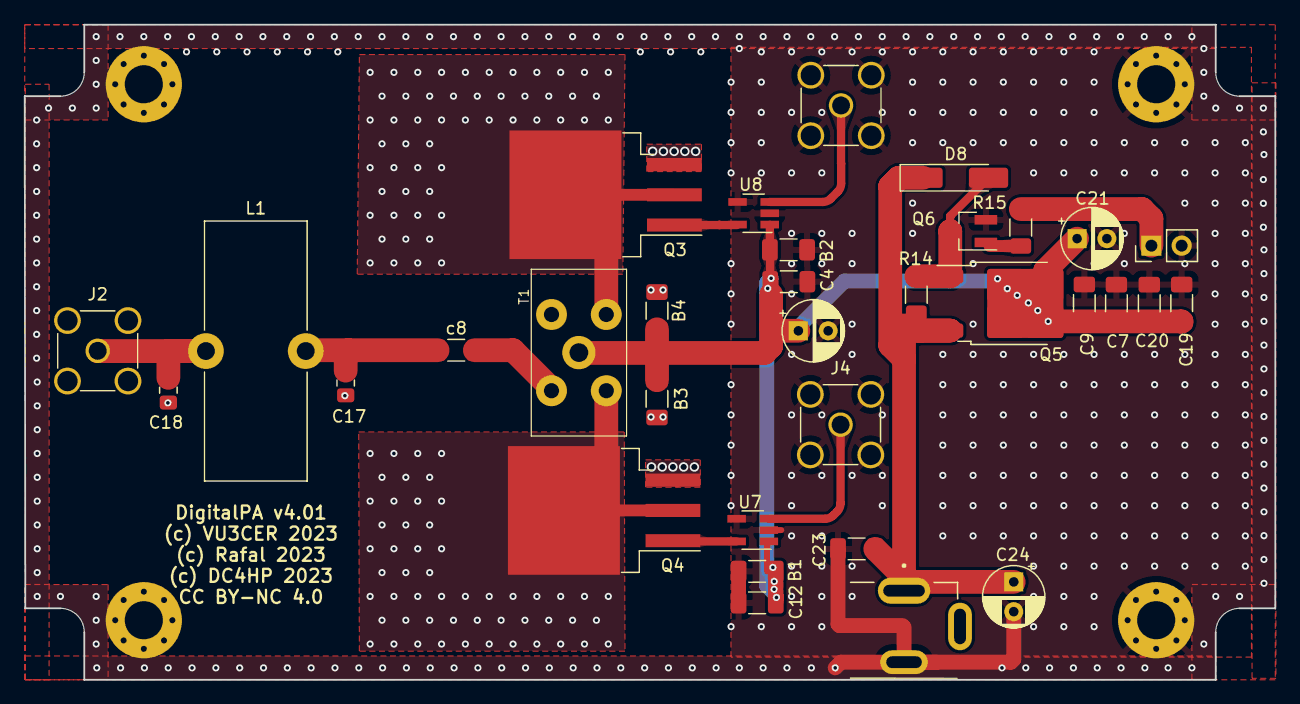
[picture p114: board digital-amp.kicad_pcb from above]

Board: 2 copper layers, 105.0 x 55.0 mm, 37 parts (0 on the bottom side), 15 nets.

Parts:
B1, B2, B3, B4: 0.1uF; C_1206_3216Metric_Pad1.33x1.80mm_HandSolder
C4, C7, C12, C19: 1n; C_1206_3216Metric_Pad1.33x1.80mm_HandSolder
C9, C20, C23: 100n; C_1206_3216Metric_Pad1.33x1.80mm_HandSolder
C10, C21, C24: 100u; CP_Radial_D5.0mm_P2.50mm
C17, C18: 100p; C_0805_2012Metric_Pad1.18x1.45mm_HandSolder
D8: 5.1V; D_MiniMELF_Handsoldering
H1, H2, H3, H4: MountingHole_Pad; MountingHole_3.2mm_M3_Pad_Via
J1, J2, J4: Conn_Coaxial; SMA_Amphenol_901-144_Vertical
J3: Conn_01x02_Male; PinHeader_1x02_P2.54mm_Vertical
L1: 318.5nH; L_Toroid_Vertical_L21.6mm_W8.4mm_P8.38mm_Pulse_G
Power1: DC-005 (Barrel Jack); XKB_DC-005-5A-2.0_Modded
Q3, Q4: IRF510; TO-263-3_TabPin2
Q5: AOD407; TO-252-2
Q6: 2N3904; SOT-23_Handsoldering
R14: 100k; R_1206_3216Metric_Pad1.30x1.75mm_HandSolder
R15: 4.7k; R_1206_3216Metric_Pad1.30x1.75mm_HandSolder
T1: BN-61-202, 2+2T:6T; BN202V
U7, U8: UCC27517DBVR; SOT-23-5_HandSoldering
c8: 0.1uF; C_1206_3216Metric_Pad1.33x1.80mm_HandSolder

Connections:
GND: B1.1, B2.1, B3.1, B4.1, C4.2, C7.2, C9.2, C10.2, C12.2, C17.2, C18.2, C19.2, C20.2, C21.2, C23.2, C24.2, H1.1, H2.1, H3.1, H4.1, J1.2 (Ext), J2.2 (Ext), J3.2, J4.2 (Ext), Power1.2, Q3.3 (S), Q4.3 (S), Q6.2 (E), T1.5, U7.2 (GND), U7.4 (IN-), U8.2 (GND), U8.4 (IN-)
unnamed: C17.1, L1.1, c8.1
unnamed: D8.2 (A), Q5.1 (G), Q6.3 (C), R14.2
unnamed: J1.1 (In), U8.3 (IN+)
unnamed: C18.1, J2.1 (In), L1.2
unnamed: J4.1 (In), U7.3 (IN+)
unnamed: Q3.2 (D), T1.1
unnamed: Q3.1 (G), U8.5 (OUT)
unnamed: Q4.2 (D), T1.3
unnamed: Q4.1 (G), U7.5 (OUT)
unnamed: Q6.1 (B), R15.1
unnamed: T1.4, c8.2
PTT: J3.1, R15.2
VDC: B1.2, B2.2, B3.2, B4.2, C4.1, C7.1, C9.1, C10.1, C12.1, C19.1, C20.1, C21.1, Q5.2 (D), T1.2, U7.1 (VDD), U8.1 (VDD)
VIN: C23.1, C24.1, D8.1 (K), Power1.1, Q5.3 (S), R14.1
