kholia/HF-PA-v10/3-Pole-LPF/LPF.kicad_pcb

## KiCad design 3-Pole-LPF/LPF.kicad_pcb (2024-09-08)

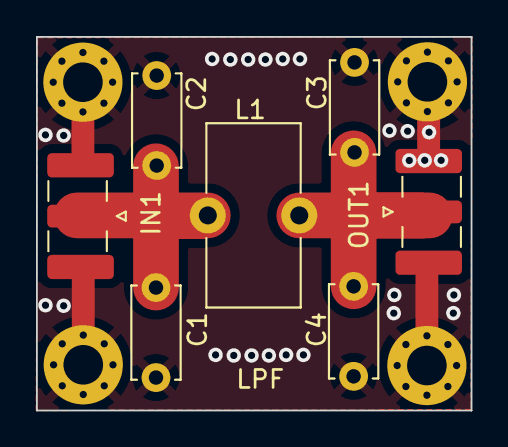
[picture p115: board 3-Pole-LPF/LPF.kicad_pcb from above]

Board: 2 copper layers, 24.1 x 20.8 mm, 11 parts (0 on the bottom side), 3 nets.

Parts:
C1, C2, C3, C4: 100n; C_Disc_D5.0mm_W2.5mm_P5.00mm
H1, H2, H3, H4: MountingHole_Pad; MountingHole_2.2mm_M2_Pad_Via
IN1: SMA; SMA_Samtec_SMA-J-P-H-ST-EM1_EdgeMount
L1: L_Small; L_Toroid_Vertical_L10.0mm_W5.0mm_P5.08mm
OUT1: SMA; SMA_Samtec_SMA-J-P-H-ST-EM1_EdgeMount

Connections:
GND: C1.2, C2.2, C3.2, C4.2, H1.1, H2.1, H3.1, H4.1, IN1.2 (Ext), OUT1.2 (Ext)
unnamed: C1.1, C2.1, IN1.1 (In), L1.1
unnamed: C3.1, C4.1, L1.2, OUT1.1 (In)
