kholia/HF-PA-v10/FuturePowerControl/FPC.kicad_pcb

## KiCad design FuturePowerControl/FPC.kicad_pcb (2024-09-08)

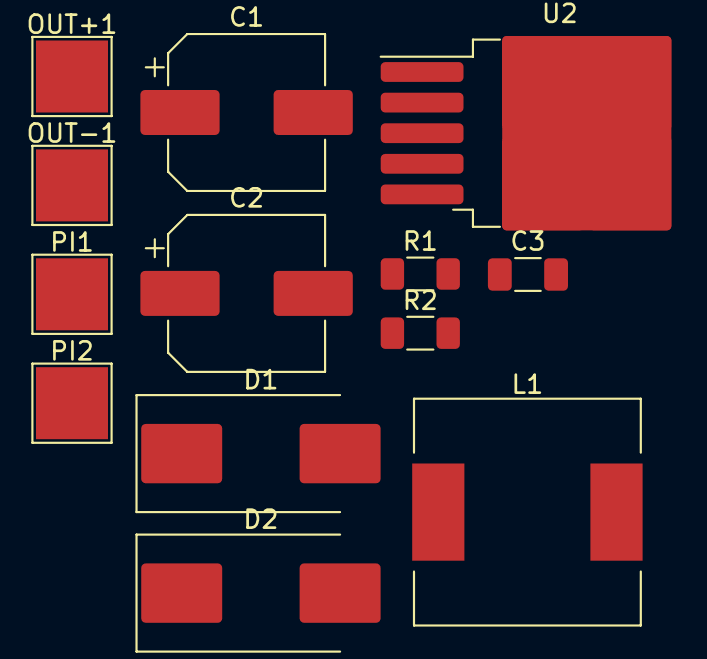
[picture p116: board FPC.kicad_pcb from above]

Board: 2 copper layers, 13 parts (0 on the bottom side), 6 nets, no tracks yet.

Parts:
C1: 220u; CP_Elec_8x10.5
C2: 470uF; CP_Elec_8x10.5
C3: 100n; C_1206_3216Metric_Pad1.33x1.80mm_HandSolder
D1, D2: SS54; D_SMC_Handsoldering
L1: 68uH; L_12x12mm_H6mm
OUT+1: OVDC; TestPoint_Pad_4.0x4.0mm
OUT-1: GND; TestPoint_Pad_4.0x4.0mm
PI1: VDC; TestPoint_Pad_4.0x4.0mm
PI2: GND; TestPoint_Pad_4.0x4.0mm
R1: 270; R_1206_3216Metric_Pad1.30x1.75mm_HandSolder
R2: 5k; R_1206_3216Metric_Pad1.30x1.75mm_HandSolder
U2: LM2596S-ADJ; TO-263-5_TabPin3

Connections:
+VDC: D2.2 (A), PI1.1
GND: C1.2, C2.2, C3.2, D1.2 (A), OUT-1.1, PI2.1, R1.2, U2.3 (GND), U2.5 (~ON/OFF)
unnamed: D1.1 (K), L1.1, U2.2 (OUT)
unnamed: C2.1, D2.1 (K), U2.1 (VIN)
unnamed: C1.1, C3.1, L1.2, OUT+1.1, R2.1
unnamed: R2.2, U2.4 (FB)
