kholia/HF-PA-v10/UCC-Driver-Board/HF-PA-v10.kicad_pcb

## KiCad design UCC-Driver-Board/HF-PA-v10.kicad_pcb (2024-09-08, an earlier design)

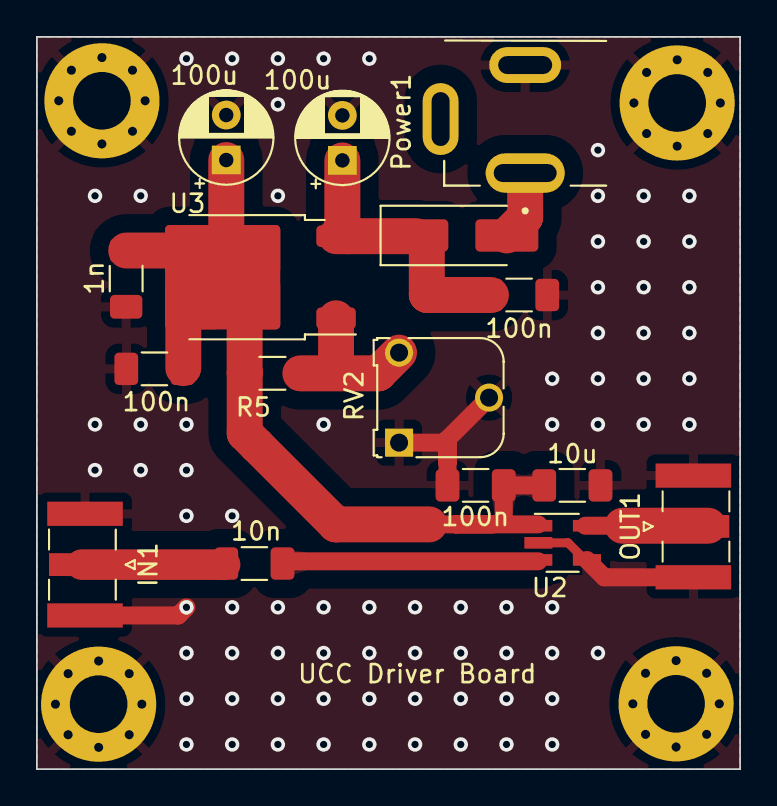
[picture p117: board UCC-Driver-Board/HF-PA-v10.kicad_pcb from above]

Board: 2 copper layers, 39.1 x 40.7 mm, 20 parts (0 on the bottom side), 8 nets.

Parts:
C5, C15: 100u; CP_Radial_D5.0mm_P2.50mm
C6, C14, C23: 100n; C_1206_3216Metric_Pad1.33x1.80mm_HandSolder
C16: 10u; C_1206_3216Metric_Pad1.33x1.80mm_HandSolder
C17: 1n; C_1206_3216Metric_Pad1.33x1.80mm_HandSolder
C19: 10n; C_1206_3216Metric_Pad1.33x1.80mm_HandSolder
D1: SS34; D_SMA_Handsoldering
H1, H2, H3, H4: MountingHole_Pad; MountingHole_3.2mm_M3_Pad_Via
IN1: SMA; SMA_Samtec_SMA-J-P-X-ST-EM1_EdgeMount
OUT1: SMA; SMA_Samtec_SMA-J-P-X-ST-EM1_EdgeMount
Power1: DC-005 (Barrel Jack); XKB_DC-005-5A-2.0_Modded
R5: 220; R_1206_3216Metric_Pad1.30x1.75mm_HandSolder
RV2: 5k; Potentiometer_Runtron_RM-065_Vertical
U2: UCC27517DBVR; SOT-23-5_HandSoldering
U3: LM317_TO-252; TO-252-2

Connections:
12V: C5.1, C6.1, C16.1, C17.1, C23.1, R5.1, U2.1 (VDD), U3.2 (VO)
+VDC: D1.2 (A), Power1.1
GND: C5.2, C6.2, C14.2, C15.2, C16.2, C17.2, C23.2, H1.1, H2.1, H3.1, H4.1, IN1.2 (Ext), OUT1.2 (Ext), Power1.2, RV2.1, RV2.2, U2.2 (GND), U2.4 (IN-)
unnamed: C14.1, C15.1, D1.1 (K), U3.3 (VI)
unnamed: C19.1, IN1.1 (In)
unnamed: OUT1.1 (In), U2.5 (OUT)
unnamed: C19.2, U2.3 (IN+)
unnamed: R5.2, RV2.3, U3.1 (ADJ)
