kholia/HF-PA-v10/5-Pole-LPF/LPF.kicad_pcb

## KiCad design 5-Pole-LPF/LPF.kicad_pcb (2024-09-08)

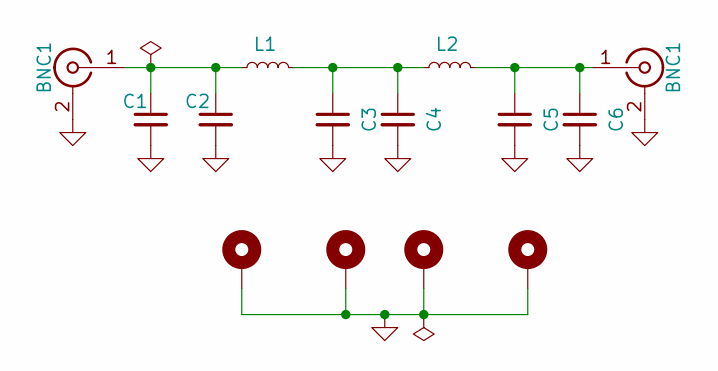
[picture p119: schematic LPF.kicad_sch, 5-Pole LPF]

Parts:
BNC1: SMA; SMA_Samtec_SMA-J-P-H-ST-EM1_EdgeMount
C1, C2, C3, C4, C5, C6: 100n; C_Disc_D5.0mm_W2.5mm_P5.00mm
H1, H2, H3, H4: MountingHole_Pad; MountingHole_2.2mm_M2_Pad_Via
L1, L2: L_Small; L_Toroid_Vertical_L10.0mm_W5.0mm_P5.08mm

Connections:
GND: C1.2, C2.2, C3.2, C4.2, C5.2, C6.2, H1.1, H2.1, H3.1, H4.1; also elsewhere on the board
unnamed: C3.1, C4.1, L1.2, L2.1
unnamed 2: C1.1, C2.1, L1.1; also elsewhere on the board
unnamed 3: C5.1, C6.1, L2.2; also elsewhere on the board

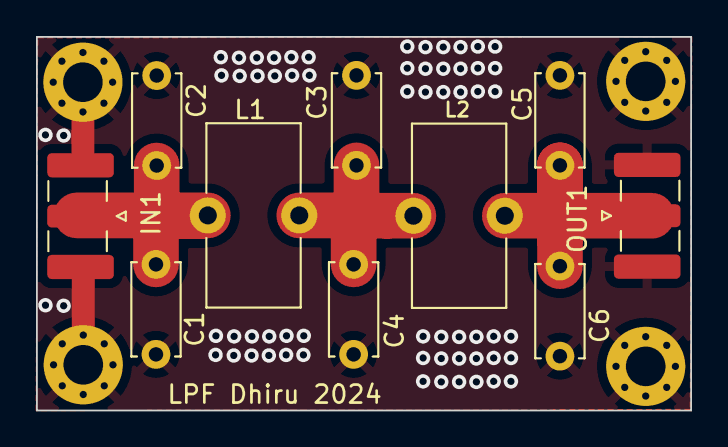
[picture p120: board 5-Pole-LPF/LPF.kicad_pcb from above]

Board: 2 copper layers, 36.3 x 20.8 mm, 14 parts (0 on the bottom side), 4 nets.

Other parts of the board:
IN1: SMA; SMA_Samtec_SMA-J-P-H-ST-EM1_EdgeMount
OUT1: SMA; SMA_Samtec_SMA-J-P-H-ST-EM1_EdgeMount

Their connections:
GND: IN1.2 (Ext), OUT1.2 (Ext); also elsewhere on the board
unnamed 2: IN1.1 (In); also elsewhere on the board
unnamed 3: OUT1.1 (In); also elsewhere on the board
