kholia/HF-PA-v10/IRFP-Hacks-v2/HF-PA-v10.kicad_pcb

## KiCad design IRFP-Hacks-v2/HF-PA-v10.kicad_pcb (2024-09-08, an earlier design)

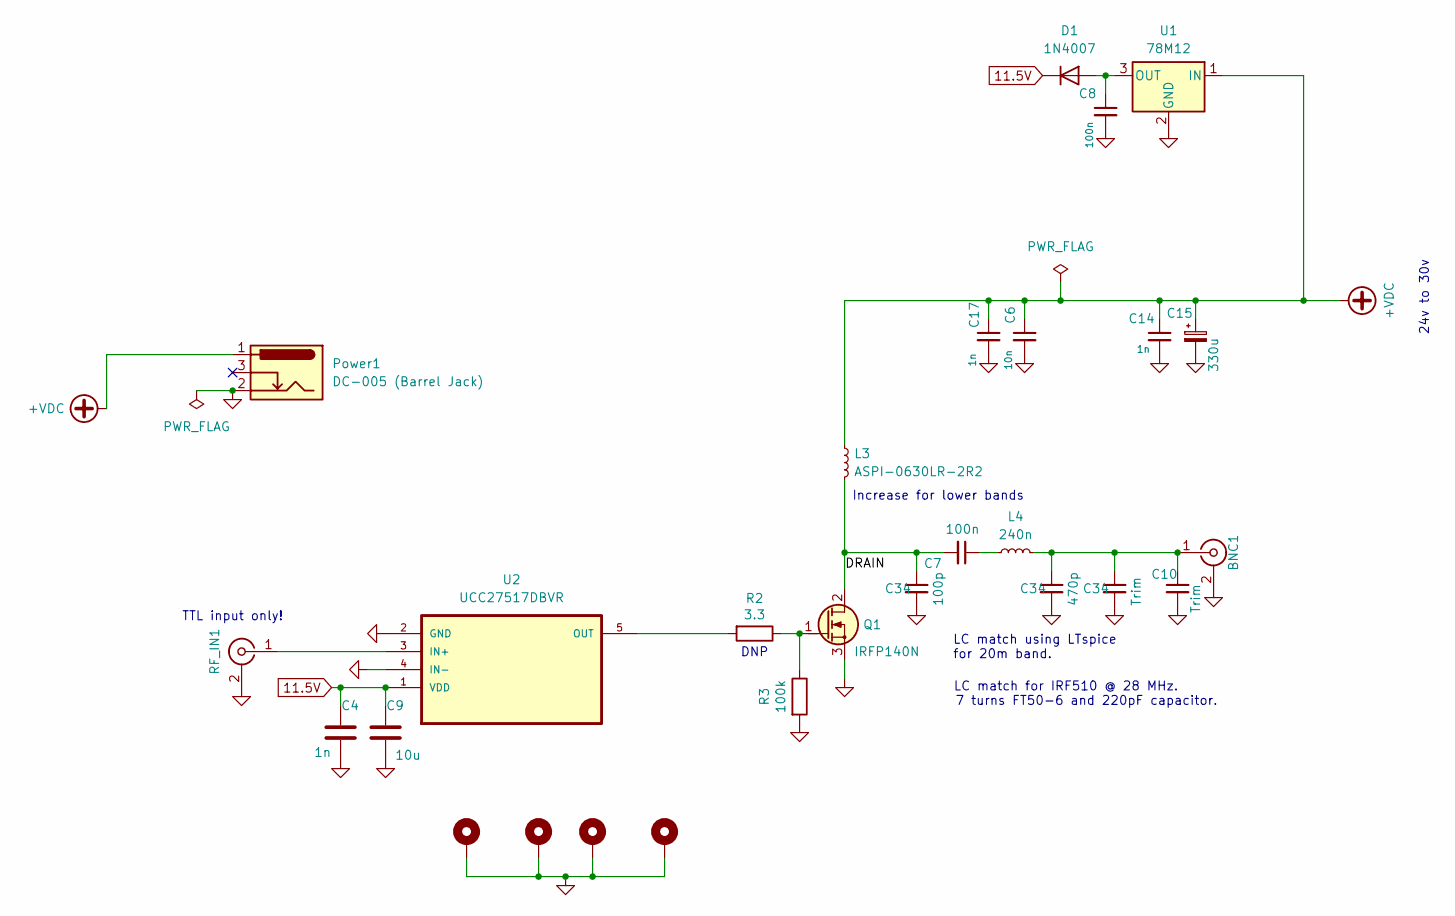
[picture p121: schematic HF-PA-v10.kicad_sch, IRFP-TO-247-Single-Ended Hack Amp]

Parts:
BNC1: SMA; SMA_Samtec_SMA-J-P-X-ST-EM1_EdgeMount
C4, C14, C17: 1n; C_1206_3216Metric_Pad1.33x1.80mm_HandSolder
C6: 10n; C_1206_3216Metric_Pad1.33x1.80mm_HandSolder
C7, C8: 100n; C_1206_3216Metric_Pad1.33x1.80mm_HandSolder
C9: 10u; C_1206_3216Metric_Pad1.33x1.80mm_HandSolder
C10: Trim; C_1206_3216Metric_Pad1.33x1.80mm_HandSolder
C15: 330u; CP_Radial_D8.0mm_P5.00mm
C34: 100p; C_1206_3216Metric_Pad1.33x1.80mm_HandSolder
D1: 1N4007; D_DO-41_SOD81_P2.54mm_Vertical_KathodeUp
H1, H2, H3, H4: MountingHole_Pad; MountingHole_3.2mm_M3_Pad_Via
L3: ASPI-0630LR-2R2; L_7.3x7.3_H3.5
L4: 240n; L_Toroid_Vertical_L10.0mm_W5.0mm_P5.08mm
Power1: DC-005 (Barrel Jack); XKB_DC-005-5A-2.0_Modded
Q1: IRFP140N; TO-247-3_Horizontal_TabDown_Modded
R2: 3.3; R_1206_3216Metric_Pad1.30x1.75mm_HandSolder
R3: 100k; R_1206_3216Metric_Pad1.30x1.75mm_HandSolder
RF_IN1: SMA; SMA_Samtec_SMA-J-P-X-ST-EM1_EdgeMount
U1: 78M12; TO-252-2-Longer
U2: UCC27517DBVR; SOT-23-5_HandSoldering

Connections:
11.5V: C4.1, C9.1, D1.1 (K), U2.1 (VDD)
+VDC: C6.1, C14.1, C15.1, C17.1, L3.1, Power1.1, U1.1 (IN)
/DRAIN: C7.2, L3.2, Q1.2 (D); also elsewhere on the board
GND: C4.2, C6.2, C8.2, C9.2, C10.2, C14.2, C15.2, C17.2, H1.1, H2.1, H3.1, H4.1, Power1.2, Q1.3 (S), R3.2, RF_IN1.2 (Ext), U1.2 (GND), U2.2 (GND), U2.4 (IN-); also elsewhere on the board
unnamed: C7.1, L4.1
unnamed: C8.1, D1.2 (A), U1.3 (OUT)
unnamed: Q1.1 (G), R2.1, R3.1
unnamed: RF_IN1.1 (In), U2.3 (IN+)
unnamed 8: C10.1, L4.2; also elsewhere on the board
unnamed: R2.2, U2.5 (OUT)

Notes on the sheet:
DNP
TTL input only!
LC match for IRF510 @ 28 MHz. 7 turns FT50-6 and 220pF capacitor.
LC match using LTspice for 20m band.
24v to 30v
Increase for lower bands

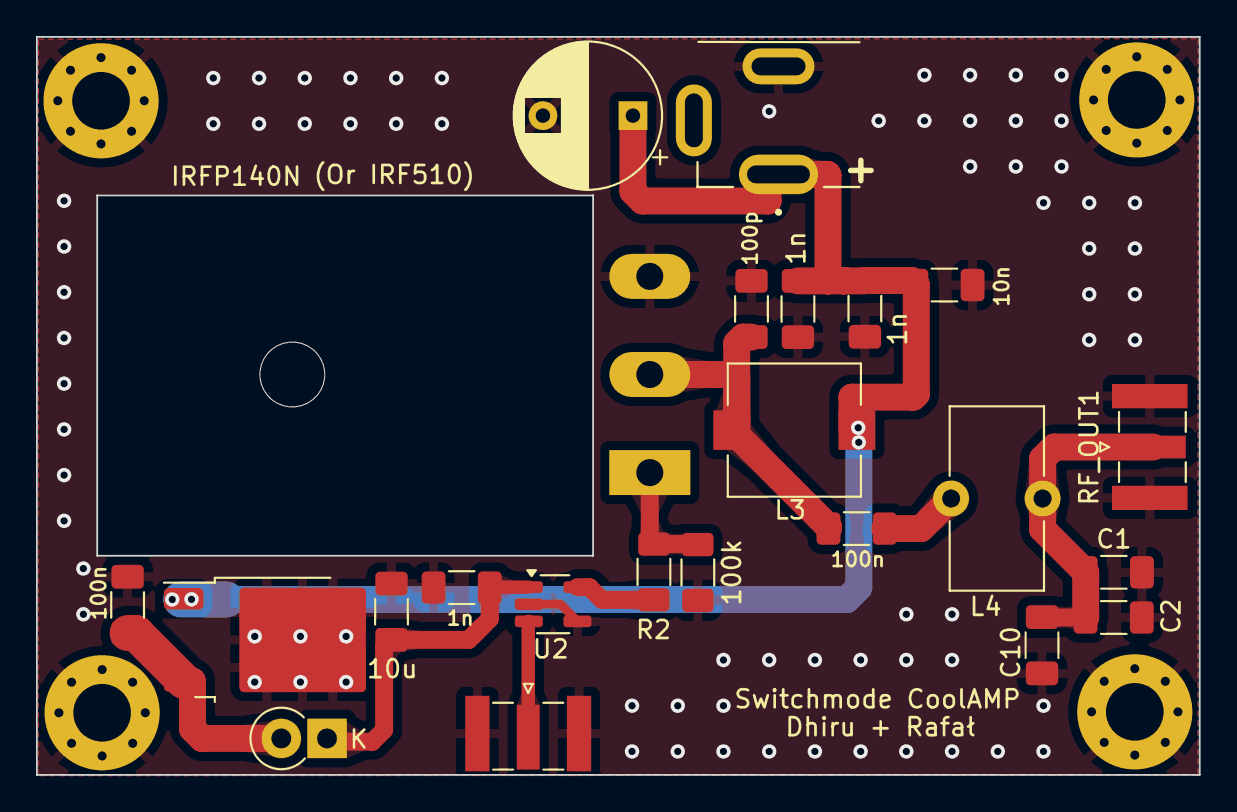
[picture p122: board IRFP-Hacks-v2/HF-PA-v10.kicad_pcb from above]

Board: 2 copper layers, 64.6 x 41.0 mm, 27 parts (0 on the bottom side), 10 nets.

Other parts of the board:
C1: 470p; C_1206_3216Metric_Pad1.33x1.80mm_HandSolder
C2: Trim; C_1206_3216Metric_Pad1.33x1.80mm_HandSolder
C3: 100p; C_1206_3216Metric_Pad1.33x1.80mm_HandSolder
RF_OUT1: SMA; SMA_Samtec_SMA-J-P-X-ST-EM1_EdgeMount

Their connections:
/DRAIN: C3.1; also elsewhere on the board
GND: C1.2, C2.2, C3.2, RF_OUT1.2 (Ext); also elsewhere on the board
unnamed 8: C1.1, C2.1, RF_OUT1.1 (In); also elsewhere on the board
